b5463/kino-d4/apps/twin/README.md

# KINO Twin acceptance

Build both applications, then serve them from one origin:

```text
npm run build
npm run preview:all
```

Open `http://localhost:4400/dev/twin/` and `http://localhost:4400/studio/` in separate tabs. Keep this checklist blunt: record PASS, FAIL, or BLOCKED with evidence for every line.

Part of this walk is automated: `npm run build && npm run test:acceptance` runs `e2e/twin-acceptance.spec.ts` headless on port 4401, and CI runs the same job on every pull request. It covers the render, inspect, optics, power-on, KDP connect, capture, CAM3 fault, battery sag, measured-override, disconnect and recorder lines. The 3D/WebGL confirmations and the Studio configuration, UART stress, Skew Bench, gallery-scale, Roll and firmware-update lines stay manual.

- [ ] Open KINO Twin and confirm the D4 V1 scene renders without the recovery screen.
- [ ] Inspect components and confirm dimensions and provenance are visible.
- [ ] Change camera pitch and lens-FOV scenario; confirm the camera row and overlap change.
- [ ] Power on Twin; connect Studio with CONNECT KINO TWIN.
- [ ] Confirm HELLO, DEVICE_INFO, CAPABILITIES, and CONFIG_SCHEMA complete through KDP.
- [ ] Configure Wiggle, Quad, and looks in Studio.
- [ ] Perform a four-camera capture.
- [ ] Confirm boot, exposure, UART, SD, and transfer changes appear in Twin's 3D scene.
- [ ] Run the Studio UART stress test and exercise slow-uart and crc-noise faults.
- [ ] Run Skew Bench and compare separate GPIO, VSYNC, and effective-exposure rows.
- [ ] Browse the large simulated gallery without an unbounded load.
- [ ] Exercise Roll connectivity loss, recovery, and upload backlog.
- [ ] Run firmware update UX and confirm target progress and reboot visuals.
- [ ] Set CAM3 offline and confirm Studio diagnoses CAM3 through KDP.
- [ ] Exercise batterySag and fuseBlown; confirm power warnings.
- [ ] Record, save, import, replay, and verify the exact scenario.
- [ ] Enter a real measured override; confirm MEASURED, refreshed geometry, and refreshed collision findings without application-code edits.

## WebSocket bridge (cross-machine Studio)

BroadcastChannel reaches only same-origin tabs. To serve this Twin to a Studio in another browser, container, or machine (issue #29):

```bash
npm run twin:relay                       # dumb message bus on ws://127.0.0.1:5179
# KINO_TWIN_WS_HOST=0.0.0.0 for LAN use — no auth, trusted networks only
```

Open the Twin with `?ws=1` (default relay on this host) or `?ws=ws://host:5179`; open Studio with `?twinWs=ws://host:5179` and its connect screen offers CONNECT KINO TWIN (BRIDGE). Transport only: the wire vocabulary, handshake, busy and close semantics are the same `TwinBusTransport` state machine the BroadcastChannel carrier uses, and `TwinDeviceServer` is unchanged.

## Tier A meshes (converted CAD)

A component renders as a parametric proxy until a real converted mesh is registered for it. The mechanism is in `@kino/three-assets` and needs no application change to use (issue #30):

```ts
import { registerComponentMesh, glbProvider } from '@kino/three-assets';

registerComponentMesh('camera-node', glbProvider(xiaoGlbUrl));
```

The mesh is fitted into the component's resolved dimensions, so the profile stays authoritative: clearance, keepouts, the BOM and the inspector all keep reading the recorded numbers, and a prettier mesh can never quietly move a wall. A missing or broken asset leaves the proxy on screen.

**The conversion itself is a human step and stays out of this repository's build:** download the official STEP (XIAO first), open it in FreeCAD or Blender, export a GLB in millimetres with the part centred on its own origin, and register it as above. Do not commit a mesh whose extents disagree with the profile — the fit will scale it, and the mismatch will only show up as a part that looks wrong next to its neighbours.

## Deliberately deferred

- The converted XIAO GLB itself. The loader, fit and fallback are in place and tested; the asset needs the offline conversion above.
- (shipped in #31) Front-panel DXF, transform CSV, and envelope STEP live in the RECORD tab beside the other engineering exports; the DXF lens-cutout diameter stays PROVISIONAL until a lens barrel is measured.
- Playwright coverage of the WebGL confirmations. The automated walk asserts that the scene mounts and that no render error boundary fires; whether the 3D actually looks right stays a human check.
