b5463/kino-d4/docs/ARCHITECTURE.md

# KINO architecture

KINO has two operating worlds. The camera and Studio form a local instrument. Roll adds a server when photographs need to leave the room. The boundary stays sharp so a network failure cannot disable capture or service work.

## System map

```mermaid
flowchart TB
    subgraph Camera["KINO D4"]
        P4["ESP32-P4 main controller"]
        N1["CAM1 ESP32-S3"]
        N2["CAM2 ESP32-S3"]
        N3["CAM3 ESP32-S3"]
        N4["CAM4 ESP32-S3"]
        SD[("microSD originals")]
        P4 <-->|UART| N1
        P4 <-->|UART| N2
        P4 <-->|UART| N3
        P4 <-->|UART| N4
        P4 --> SD
    end

    Studio["KINO Studio"] <-->|"KDP / Web Serial"| P4
    Device["Device upload client"] --> API["KINO API"]
    P4 --> Device
    API --> PG[("PostgreSQL metadata")]
    API --> Redis[("Redis events")]
    API --> S3[("S3 originals + derivatives")]
    API -->|SSE| Roll["KINO Roll clients"]
    Twin["KINO Twin"] -.->|"virtual transport, same KDP"| Studio
```

## Local device path

Studio connects to the main controller through Web Serial. Boot noise is expected. The decoder scans for the KDP magic bytes, resynchronizes, performs a nonce handshake, then asks the device for identity, capabilities, configuration, camera status, power, storage, and network state.

Feature code never owns a serial port. It talks to `KinoProtocolClient` through a `Transport`:

```text
Studio page
  → device service
  → KinoProtocolClient
  → Transport
  → SerialTransport or simulator transport
  → KDP frame
```

This seam keeps the future Twin honest. A simulated device must obey the same framing, sequence IDs, timeouts, jobs, and capabilities as physical hardware.

## Shared package ownership

| Package | Owns |
|---|---|
| `@kino/kdp` | Frame encoding and decoding, CRC-32, command IDs, wire types, request lifecycle, timing vocabulary, serial and mock transports |
| `@kino/schemas` | Versioned portable documents for devices, configuration, captures, assets, firmware, and errors |
| `@kino/test-fixtures` | Reference device behavior, media fixtures, scenarios, recipes, and device audio |

Wire payloads and portable documents solve different jobs. KDP payloads live inside protocol frames and follow `PROTOCOL_VERSION`. Portable `kino.*` documents carry their own schema name and version. A field name that works on the wire may still be wrong in a stored document. The firmware contract records the known crossings.

## Studio state

Studio keeps three classes of state apart:

- Device truth: the latest value acknowledged or reported by KINO.
- Draft state: local edits that have not been applied.
- Transient state: connection attempts, transfers, calibration jobs, retries, and updates.

The Apply bar exists because draft state cannot masquerade as camera state. After a write, Studio reads back or waits for the device report before showing the value as saved.

## Capture path

The camera captures every original to microSD before network work begins.

```text
four sensor frames
  → central SD originals
  → optional preview
  → resumable upload
  → immutable S3 original keys
  → processing jobs
  → derived wiggle, thumbnail, metadata, export
```

Original keys live under:

```text
rolls/<rollId>/captures/<captureId>/original/cam-<NN>.jpg
```

Workers write under `derived/`. Completion streams the stored object back through SHA-256 before the asset becomes ready. Database uniqueness constraints, rather than preflight reads, enforce capture and asset idempotency under concurrent retries.

## Roll events

The API appends each event to a bounded Redis stream before publishing it live. Guests receive named Server-Sent Events. Reconnects carry `Last-Event-ID` and replay the missed stream range.

One subscriber connection serves all Roll guests in an API process. If that connection drops, the API closes the open SSE responses. Browsers reconnect and replay the gap instead of sitting on a healthy-looking socket that missed photographs.

## Repository map

```text
apps/
  api/                 Fastify API, migrations, auth, uploads, SSE
  studio/              React device workbench
  worker/              BullMQ media workers: derivatives, recaps, exports, purge
  roll-web/            public Roll guest PWA and host dashboard
  twin/                KINO Twin 3D assembly, simulation, and measurement
packages/
  kdp/                 protocol implementation
  schemas/             portable document schemas
  test-fixtures/       reference device and fixtures
  design-system/       shared tokens and accessible primitives
  media/               wiggle frame sequencing shared by web and worker
  hardware-profiles/   versioned D4 geometry, nets, GPIO map
  simulator-engine/    boot, capture choreography, power/thermal models, replay
  three-assets/        parametric 3D component builders
firmware/              ESP-IDF firmware: P4 main controller, XIAO camera node, portable KDP C core
firmware-contract/     firmware-facing contract
infra/                 dev/staging/production compose, backup and drill scripts
kino_dev_spec_pack/    product specifications
kino_twin_spec/        digital-twin specification and source data
docs/                  maintained guides, audits, historical plans
archive/               retained recovery material
```

## Current implementation line

The main branch contains Studio, the full Roll backend and workers, the public Roll client, KINO Twin, shared contracts, production/staging infrastructure with tested backup and restore, and broad tests. All of it runs against the simulated device. The D4-V1 firmware now also lives here (`firmware/`): the P4 and camera-node applications build clean in CI and implement the Milestone 1B single-camera surface, but nothing has run on physical hardware — `firmware/HARDWARE_VALIDATION.md` records what the bench has actually proven (currently nothing), and measured hardware dimensions remain outstanding. Hardware-gated acceptance items are marked as such where they appear.

For exact protocol authority, start at [the firmware contract](../firmware-contract/README.md). For the hardware boundary, read [the hardware reference](HARDWARE.md).
