b5463/kino-d4/docs/DEVICE_COPY.md

# Device copy

Every line the KINO D4 body says on its own screen, and when. Source of truth is `firmware/p4/main/ui.c`, `conditions.h` and `capture.c`. `npm run copy:check` walks those three files and fails when a line they can draw is not in this table, so the sentence above is a check rather than a promise.

## The rule

The person holding the camera has read nothing and will not phone anyone. Each line names what happened and, when there is one, what to do about it. Under 40 characters for a toast, one short line for a banner, two for a dialog. Plain words: lens, photo, card, cells. No codes, no camera numbers, no contract names on the glass; those go to the log and the KDP reply.

## Header chip

| Text | When |
|---|---|
| `PROBLEM` / `CHECK` / `NOTE` | The worst open condition. Absent when there is none. |
| `4571 SHOTS` | Card mounted, photographs left at 6 MB each. |
| `LAST 5` .. `LAST 1` | Five or fewer left. |
| `CARD FULL` | None left. |
| `NO CARD` | No card mounted since boot. |
| `CARD OUT` | The card was pulled while running. |
| `USB` / `BATTERY` | Where the power comes from. |

## STATUS rows

Severity words: PROBLEM stops photographs, CHECK does not yet, NOTE is information.

| Title | Detail | Severity |
|---|---|---|
| No card | Put a card in. Photos cannot be saved. | PROBLEM |
| The card was taken out | Put it back. Photos cannot be saved. | PROBLEM |
| The card cannot be read | Not a format KINO reads. Use a card up to 32 GB, or format it. | PROBLEM |
| This card failed a write | Copy your photos off it and change the card. | PROBLEM |
| This card is slow | Photos take longer to save. A faster card helps. | CHECK |
| The card is full | Delete photos or change the card. | PROBLEM |
| Card nearly full | Room for about N more photos. | CHECK |
| A lens is not answering | The second from the left. Try RESTART THE CAMERAS below. | PROBLEM, with the four cells |
| Lenses are not answering | 2 of 4. Try RESTART THE CAMERAS below. | PROBLEM, with the four cells |
| The cameras need an update | Connect to Studio to update them. | CHECK |
| The date is not set | Wi-Fi or Studio sets it once. | CHECK |
| Cameras not measured | The first photograph measures them. | NOTE |
| The camera lost power while running | Charge or replace the cells. | CHECK |
| Running without Wi-Fi | It crashed 3 times in a row. Restart to try again. | PROBLEM |
| The camera is warm | 78 C inside. The finder slows until it cools. | CHECK |
| The clock is on UTC | Set the time zone in CONNECTION. | NOTE |
| Uploads have no server | Set the Roll server in Studio. Photos stay on the card. | CHECK |

Action rows at the foot of STATUS: **Restart the cameras** (always) and **Measure cameras again** (once measured).

## SHOOT banner

| Text | When |
|---|---|
| `SHOOTING` / `READING` / `SAVING` | The capture's stages. |
| `SAVING - NEXT SHOT QUEUED` | A second shutter press landed while saving; it fires when the report does. |
| `TAKE THE LENS COVER OFF` | On SHOOT, every pane was lit and then all went dark for a second: the cover went on. A body switched on facing the desk says nothing. |
| `CHECK THE SECOND LENS` | On SHOOT, one pane was lit and then went a third as bright as the rest for a second while the others stayed lit. |
| `10` .. `1`, `SELF-TIMER.  PRESS TO CANCEL` | A long shutter press started the timer. |
| `SAVED` | Every lens that answered is on the card. |
| `SAVED, 1 CAMERA MISSED` | A partial photograph; the cells show which. |
| `No card. Put one in.` | Shutter with no card. |
| `Card full. Delete photos or change the card.` | Shutter with no room. |
| `No lens answered. Try a restart.` | No camera node answered the probe. |
| `The lenses did not wake. Try a restart.` | The camera bank did not come back after a cycle. |
| `Card error. Photo not saved.` | The capture folder could not be made, or META.JSON would not commit and the half-made folder was removed. Both end with nothing on the card, so both say so; the log and the KDP reply separate the causes. |

## Working banners

| Text | When |
|---|---|
| `FORMATTING THE CARD` | FORMAT confirmed; the card is locked for the seconds it takes. |
| `RESTARTING THE CAMERAS` | RESTART THE CAMERAS pressed; three seconds. |

## Toasts

| Text | When |
|---|---|
| Card ready, 4571 SHOTS | A card was put in while running and mounted. |
| Card taken out. Photos cannot be saved | The card was pulled while running. |
| Card busy. Try again | The card lock was held for two seconds by a capture or an upload. |
| Card formatted | FORMAT finished. |
| The card could not be formatted | FORMAT failed; the log has the reason. |
| Deleted.  TAP TO UNDO | One photograph moved to the trash; the toast stays thirty seconds and a tap restores it. |
| Restored | UNDO tapped in time. |
| Could not restore it | The folder would not move back. |
| Timer cancelled | A press during the self-timer. |
| Deleting photos | DELETE ALL started on the gallery task. |
| No photos on the card | DELETE ALL with nothing to delete. |
| No card in the slot | FORMAT with nothing in the slot. |
| Cameras measured | The first photograph's measurement stored. |
| Not measured: aim at something with detail | The measurement found a flat scene. |
| The next photo measures the cameras | MEASURE AGAIN pressed. |
| Sent to the roll | SEND TO ROLL queued the photograph. |
| Could not send. Try again later | SEND TO ROLL could not queue it. |
| No active roll | SEND TO ROLL with no Roll joined. |
| No pictures on the card to send | SEND TO ROLL on a photograph with no frames left. |
| Could not save the change | The favourite flag could not be written. |
| Still reading the card | A tile tapped before the gallery had its id. |
| No looks on this camera | LOOK with no recipes. |
| Hold the power slide to switch off | SHUT DOWN row, which has no soft power-off. |
| The cameras did not start. Restart the camera | The shutter, on a body whose capture pipeline failed to come up at boot. Said instead of blaming a capture that is not running. |
| Favourite / Not favourite | FAVOURITE pressed on PHOTO; the mark went on or came off. |
| First photo / Last photo | PREV on the first photograph, or NEXT on the last. |

## Dialogs

| Title | Body | Buttons | When |
|---|---|---|---|
| FIRST START | Take a photograph first. It measures the cameras. See STATUS. | GOT IT | The first boot, once. |
| UPDATED | KINO has been updated. Now on 0.4.58. Nothing to do. | OK | The first boot on a new version, once. |
| RESTART | Back in a moment? KINO restarts and comes back to SHOOT. | RESTART / CANCEL | POWER > RESTART |
| FACTORY RESET | Reset the camera? Settings, networks and roll are erased. | RESET / CANCEL | POWER > FACTORY RESET |
| DELETE | Delete this photo? N frames. This cannot be undone. | DELETE / CANCEL | PHOTO > DELETE |
| DELETE ALL | Delete all photos? N photos. This cannot be undone. | DELETE / CANCEL | STORAGE > DELETE ALL PHOTOS |
| FORMAT CARD | Erase the card? Every photo on it is deleted. | FORMAT / CANCEL | STORAGE > FORMAT CARD |

## Screen rows and labels

What each screen puts on itself, beyond the chip, the banner and the toasts
above. Every one of these is drawn by `ui.c`; the check script walks the same
calls and fails when one of them is not in this table.

### SHOOT

| Text | When |
|---|---|
| `MENU` | The way out, on the back button beside the picture. |
| `WIGGLE` / `QUAD` | The mode, on the decisions bar. Tapping the bar opens LOOK. |
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
