b5463/kino-d4/firmware/FIRMWARE_ROADMAP.md

# KINO D4 firmware roadmap — current state to validated prototype

Dependency-ordered plan from firmware 0.3.0 to a physically validated KINO D4, then toward
product-ready firmware. Derived from the Phase 1 baseline audit of HEAD `7a6066a`.

**Status:** planning document. Nothing here is implemented.
**Companion documents:** [`HARDWARE_VALIDATION.md`](HARDWARE_VALIDATION.md) (bench evidence),
[`FIRMWARE_START_PLAN.md`](FIRMWARE_START_PLAN.md) (original tree plan),
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
