b5463/kino-d4/docs/assets/brand/kino-d4-silver-on-dark.png

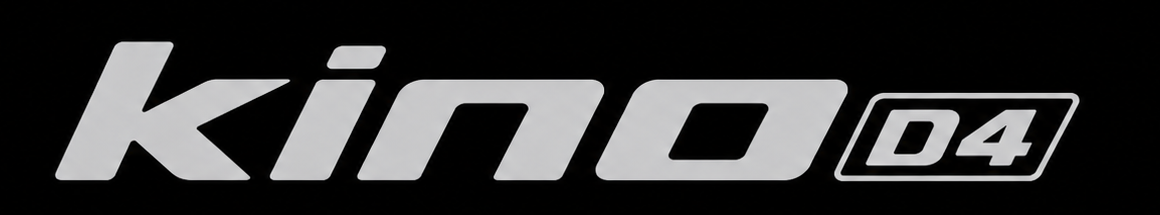
docs/assets/brand/kino-d4-silver-on-dark.png
