b5463/kino-d4/docs/assets/brand/kino-d4-wordmark-sheet.png

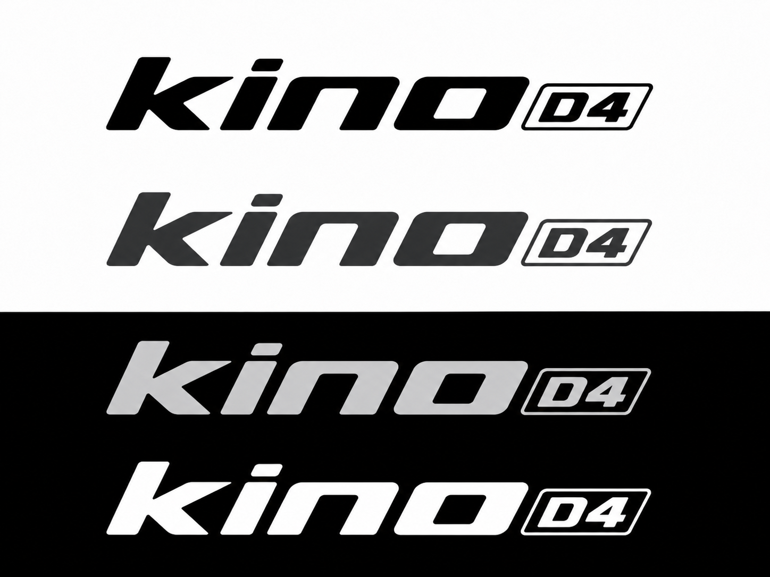
docs/assets/brand/kino-d4-wordmark-sheet.png
