b5463/kino-d4/docs/assets/brand/kino-roll.png

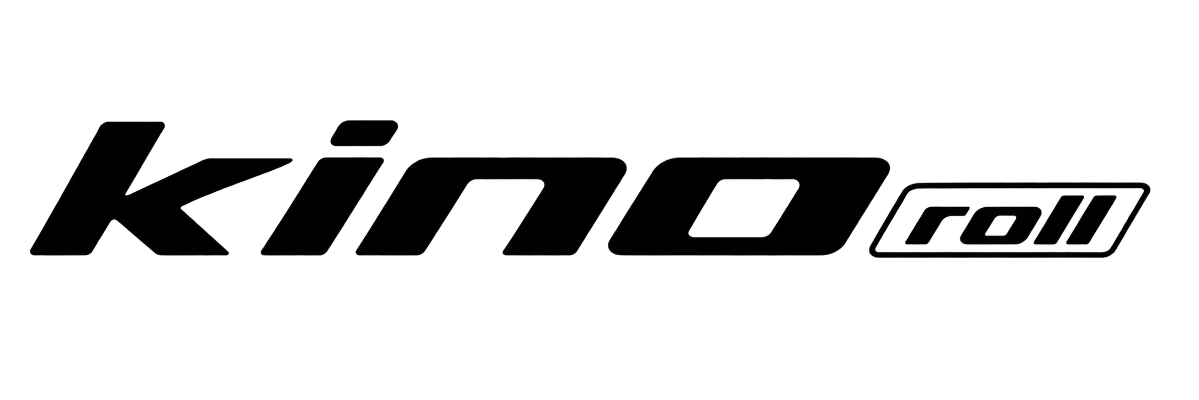
docs/assets/brand/kino-roll.png
