b5463/kino-d4/docs/assets/brand/kino-studio-wordmark.png

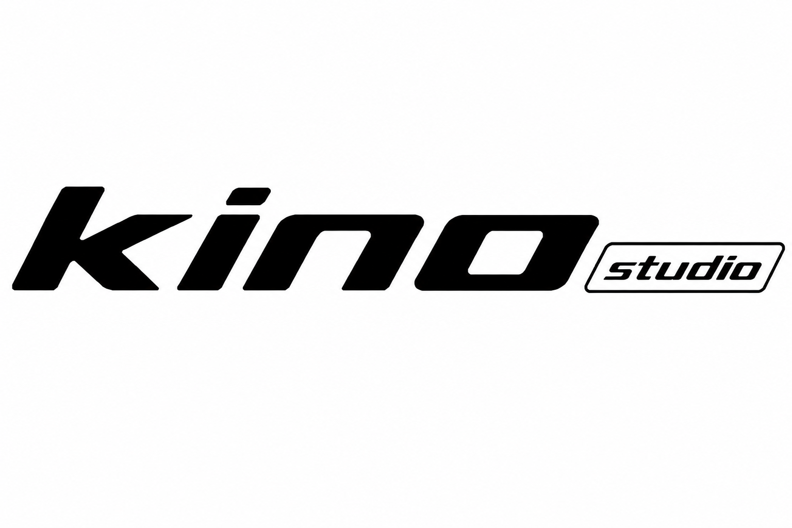
docs/assets/brand/kino-studio-wordmark.png
