b5463/kino-d4/firmware/p4/host_preview/specimen/GUEST.png

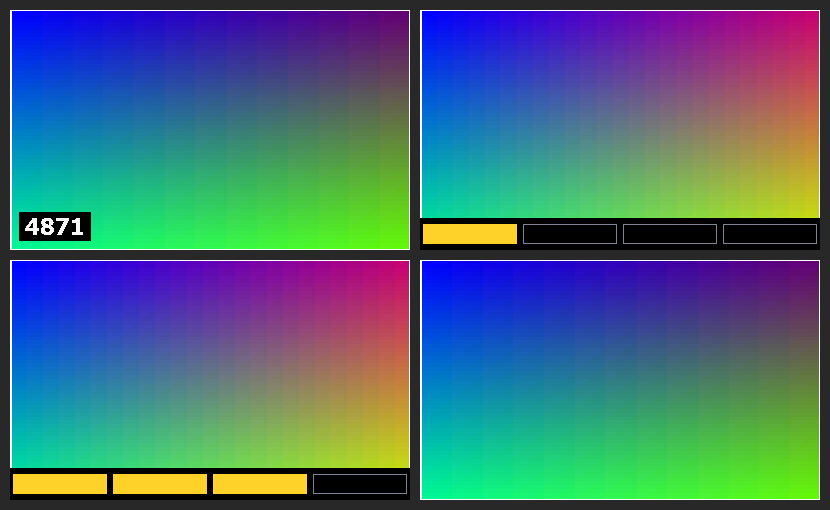
firmware/p4/host_preview/specimen/GUEST.png
