b5463/kino-d4/firmware/p4/host_preview/specimen/MENU_STACK.png

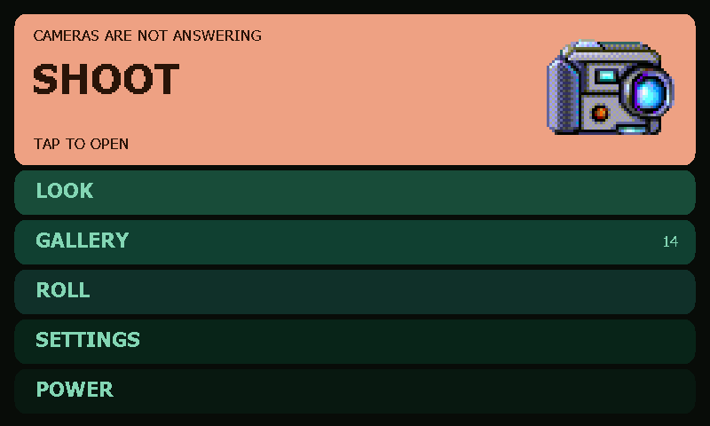
firmware/p4/host_preview/specimen/MENU_STACK.png
