b5463/kino-d4/hardware/cad/KINO_FIELD_BODY/previews/KINO_DOOR_JOINT_COUPON_PREVIEW.png

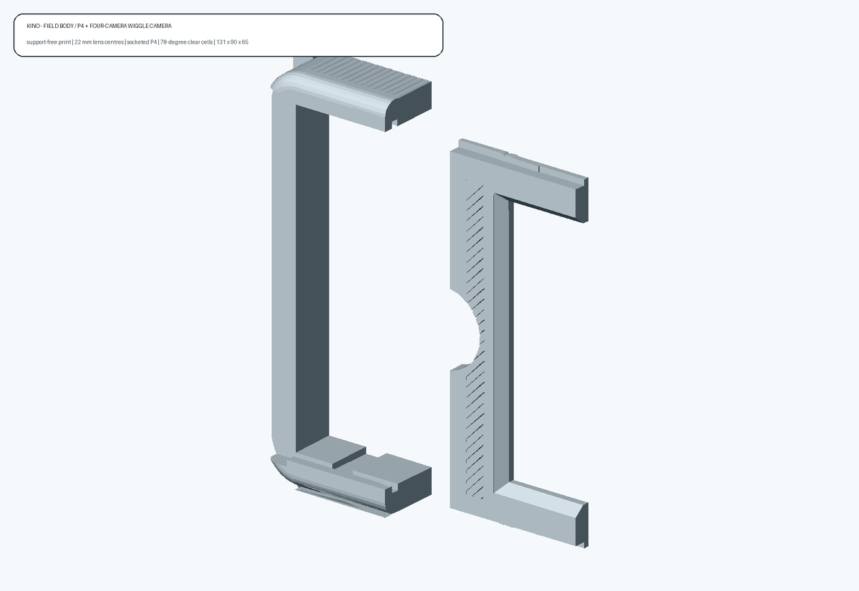
hardware/cad/KINO_FIELD_BODY/previews/KINO_DOOR_JOINT_COUPON_PREVIEW.png
