b5463/kino-d4/hardware/cad/KINO_FIELD_BODY/previews/KINO_FACE_ALIGN_TOOL_PREVIEW.png

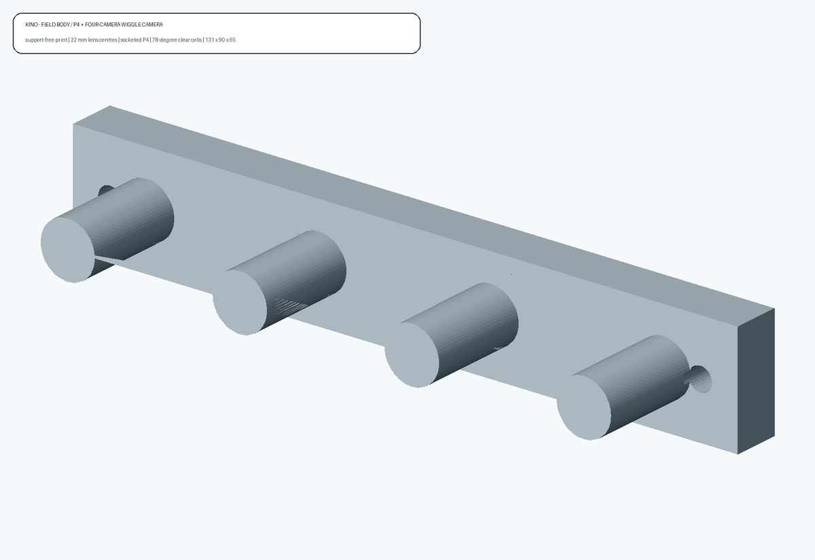
hardware/cad/KINO_FIELD_BODY/previews/KINO_FACE_ALIGN_TOOL_PREVIEW.png
