b5463/kino-d4/hardware/cad/KINO_FIELD_BODY/previews/KINO_FIELD_BEZEL_PREVIEW.png

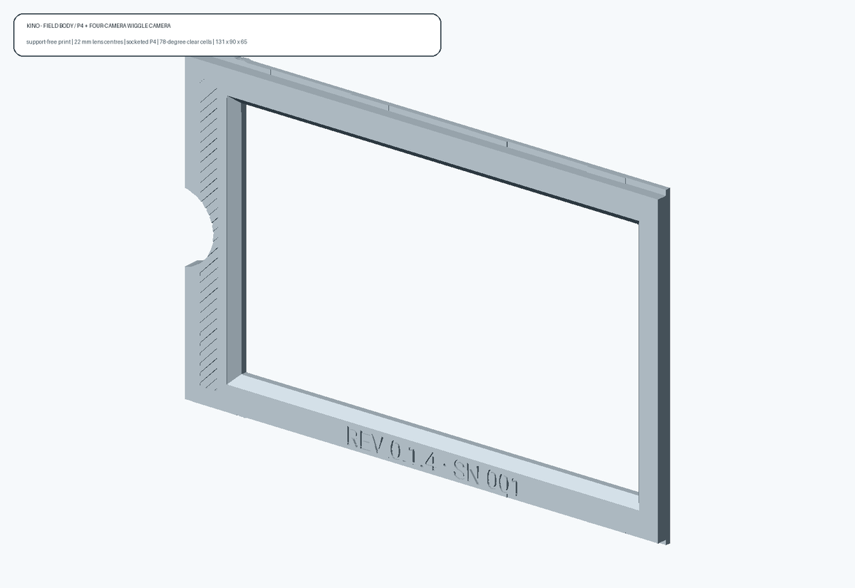
hardware/cad/KINO_FIELD_BODY/previews/KINO_FIELD_BEZEL_PREVIEW.png
