b5463/kino-d4/hardware/cad/KINO_FIELD_BODY/previews/KINO_FIELD_LENS_SLIDER_FRONT.png

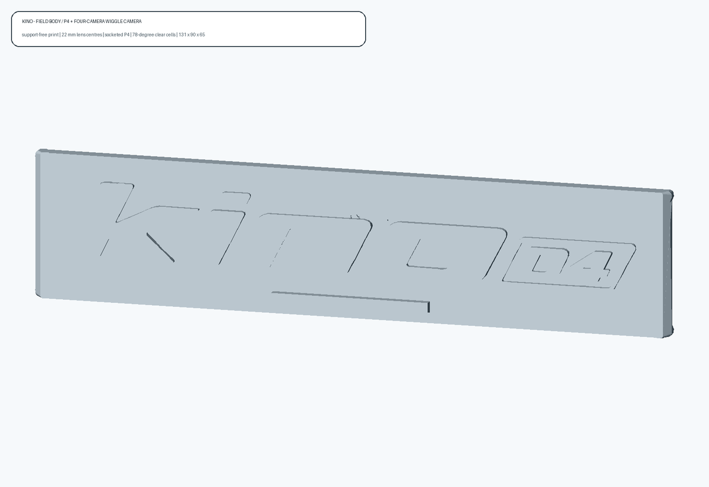
hardware/cad/KINO_FIELD_BODY/previews/KINO_FIELD_LENS_SLIDER_FRONT.png
