b5463/kino-d4/hardware/cad/KINO_FIELD_BODY/previews/KINO_FIELD_LENS_SLIDER_PREVIEW.png

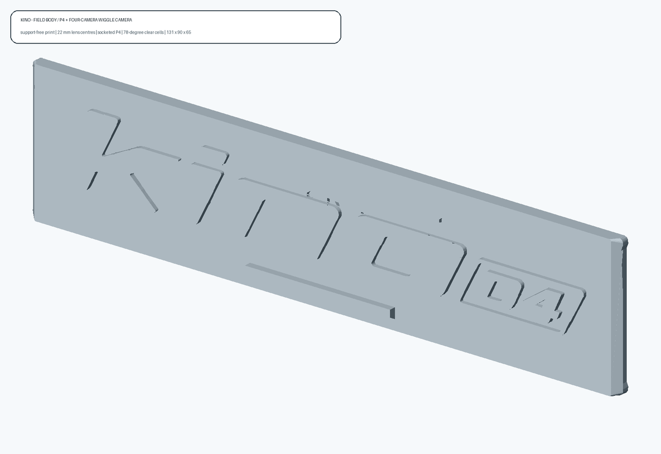
hardware/cad/KINO_FIELD_BODY/previews/KINO_FIELD_LENS_SLIDER_PREVIEW.png
