b5463/kino-d4/hardware/cad/KINO_FIELD_BODY/previews/KINO_PLATE_2_FACE_DOOR_COVER_PREVIEW.png

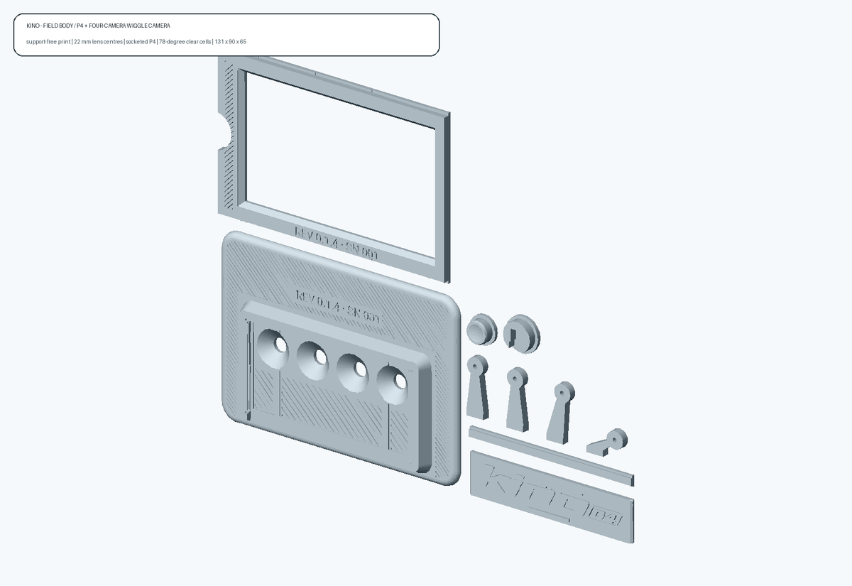
hardware/cad/KINO_FIELD_BODY/previews/KINO_PLATE_2_FACE_DOOR_COVER_PREVIEW.png
