b5463/kino-d4/hardware/cad/KINO_FIELD_BODY/previews/KINO_SPLIT_JOINT_COUPON_PREVIEW.png

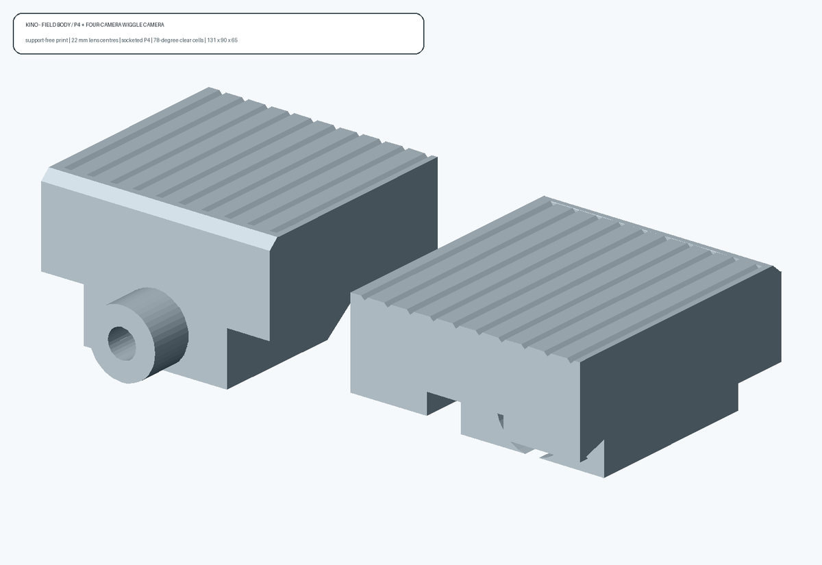
hardware/cad/KINO_FIELD_BODY/previews/KINO_SPLIT_JOINT_COUPON_PREVIEW.png
