b5463/kino-d4/hardware/pcb/kino-d4-carrier-a0/outputs/P4-MOUNTING-TEMPLATE.png

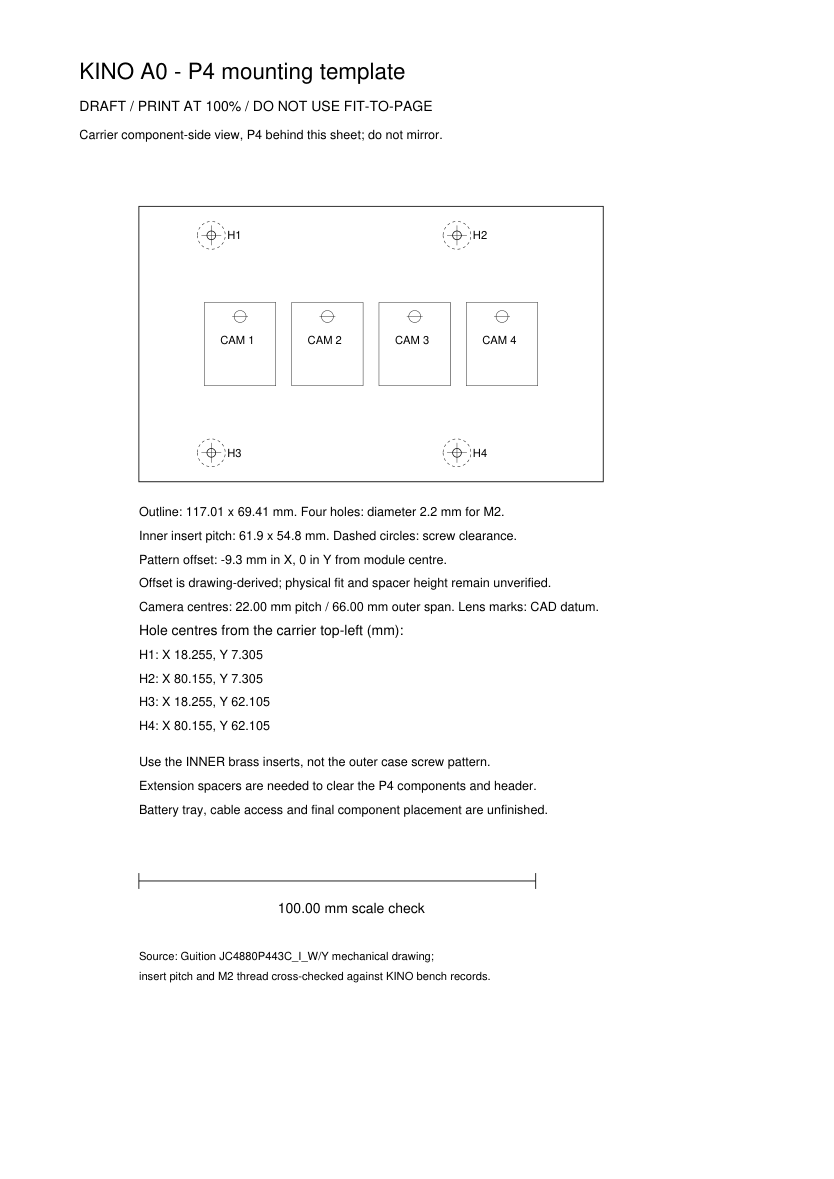
hardware/pcb/kino-d4-carrier-a0/outputs/P4-MOUNTING-TEMPLATE.png
