b5463/kino-d4/hardware/pcb/kino-d4-carrier-a0/outputs/page-3.png

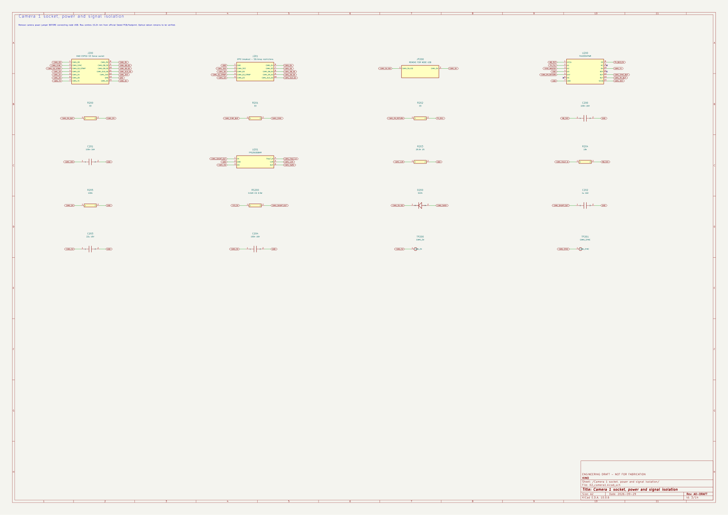
hardware/pcb/kino-d4-carrier-a0/outputs/page-3.png
