b5463/kino-d4/hardware/pcb/kino-d4-carrier-a0/outputs/PLACEMENT-DRAFT.png

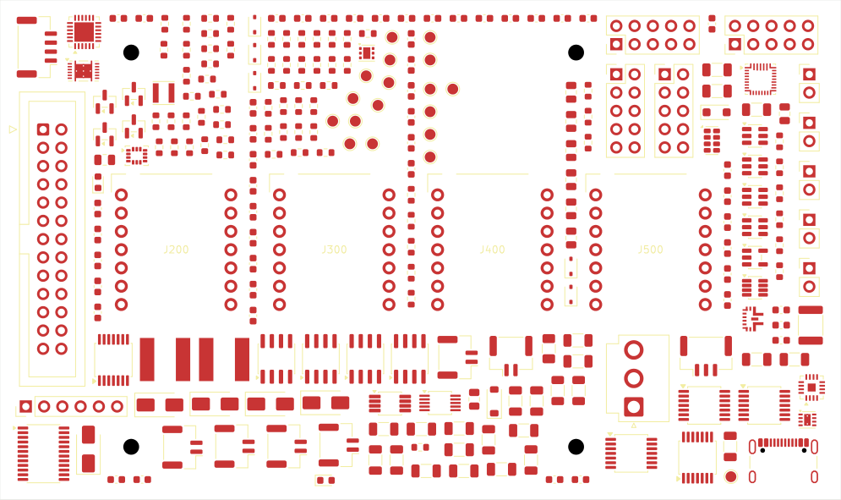
hardware/pcb/kino-d4-carrier-a0/outputs/PLACEMENT-DRAFT.png
