b5463/kino-d4/hardware/pcb/kino-d4-carrier-a0/outputs/REVIEW-TOP.png

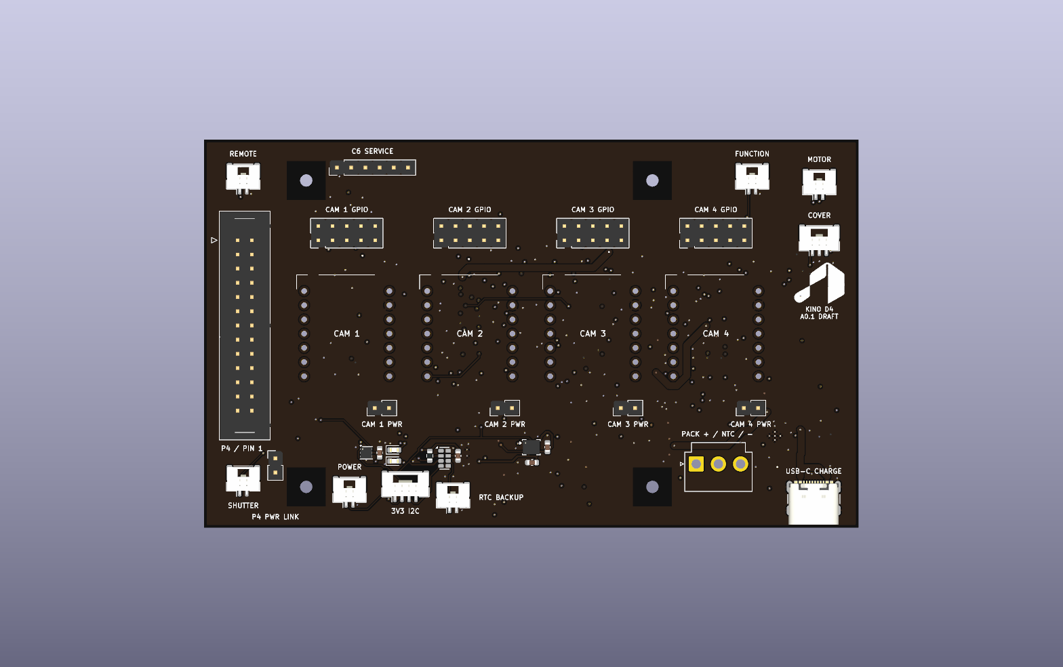
hardware/pcb/kino-d4-carrier-a0/outputs/REVIEW-TOP.png
