b5463/kino-d4/hardware/pcb/kino-d4-mainboard-rev1/outputs/KINO_D4_Mainboard_Rev1-envelope.png

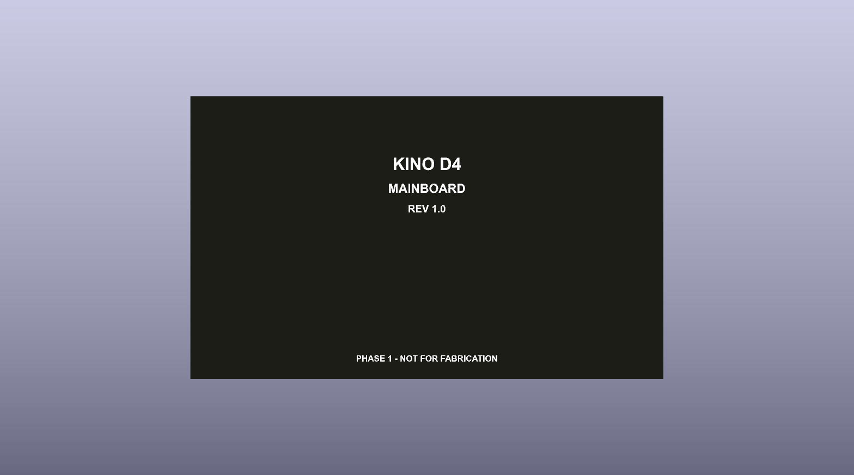
hardware/pcb/kino-d4-mainboard-rev1/outputs/KINO_D4_Mainboard_Rev1-envelope.png
