b5463/kino-d4/hardware/cad/KINO_FIELD_BODY/coupons/KINO_WIGGLE_TEST_RIG.stl

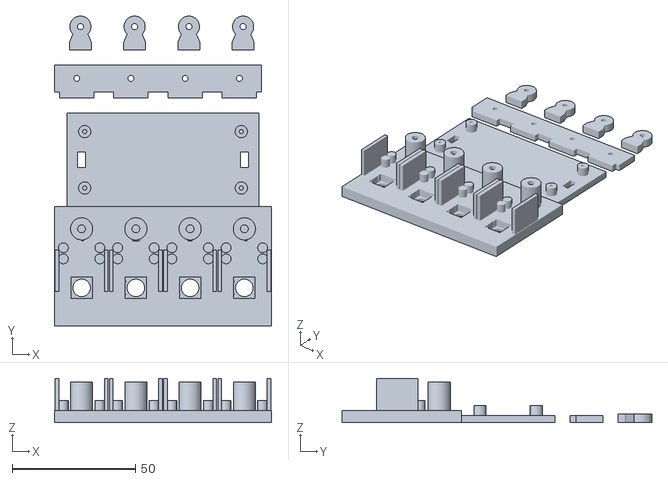
[picture p69: CAD file, 2026-09-08]
hardware/cad/KINO_FIELD_BODY/coupons/KINO_WIGGLE_TEST_RIG.stl
88.0 x 125.7 x 18.0
