b5463/kino-d4/hardware/cad/KINO_FIELD_BODY/print/KINO_FIELD_SHUTTER_BUTTON.stl

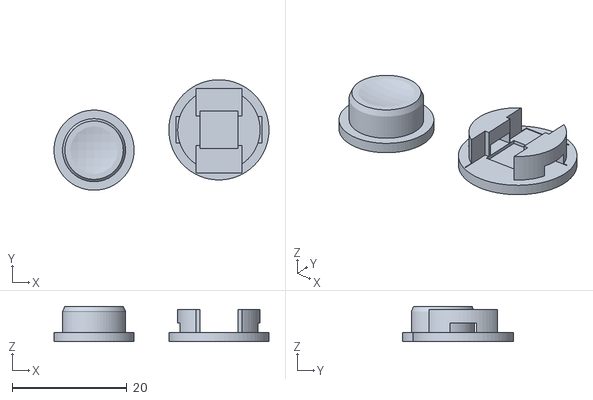
[picture p70: CAD file, 2026-09-08]
hardware/cad/KINO_FIELD_BODY/print/KINO_FIELD_SHUTTER_BUTTON.stl
37.5 x 19.3 x 6.20
