b5463/kino-d4/hardware/cad/KINO_FIELD_BODY/twin/KINO_TWIN_DOOR.stl

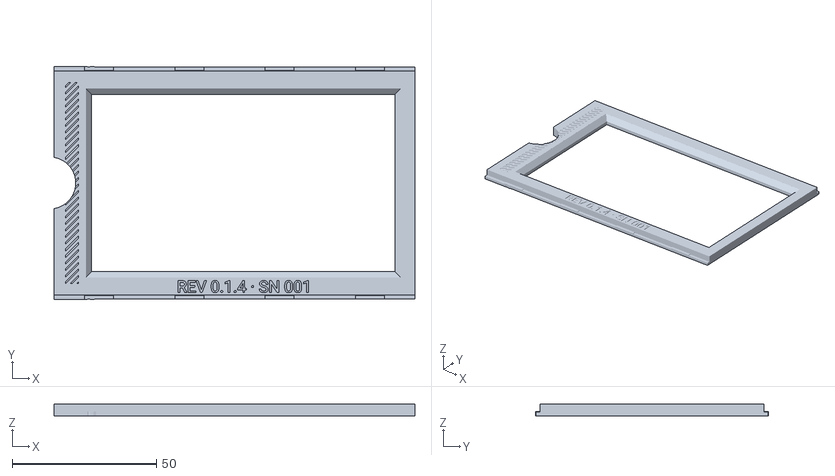
[picture p71: CAD file, 2026-09-19]
hardware/cad/KINO_FIELD_BODY/twin/KINO_TWIN_DOOR.stl
125.0 x 80.7 x 4.00
