b5463/kino-d4/hardware/cad/KINO_FIELD_BODY/coupons/KINO_SHUTTER_COUPON.stl

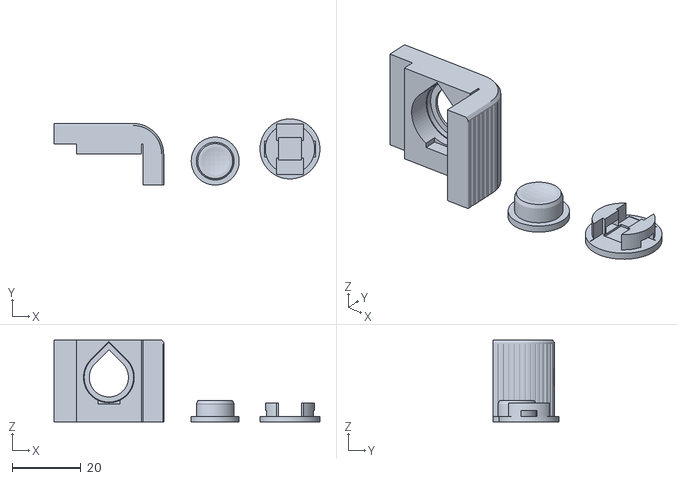
[picture p72: CAD file, 2026-09-08]
hardware/cad/KINO_FIELD_BODY/coupons/KINO_SHUTTER_COUPON.stl
77.6 x 19.3 x 23.9
