b5463/kino-d4/hardware/cad/KINO_FIELD_BODY/coupons/KINO_XIAO_STACK_COUPON.stl

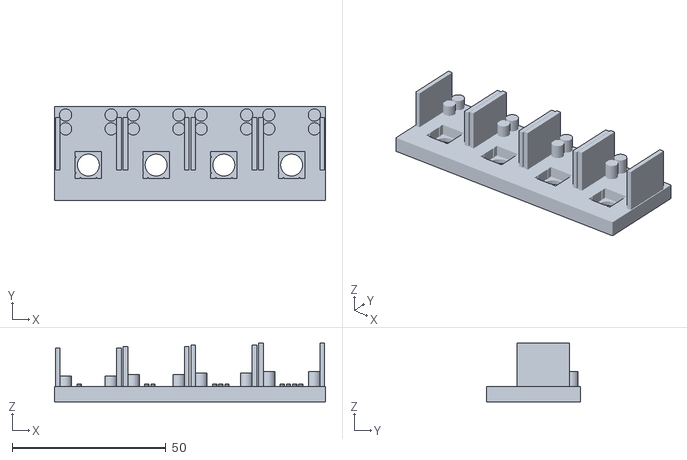
[picture p73: CAD file, 2026-09-08]
hardware/cad/KINO_FIELD_BODY/coupons/KINO_XIAO_STACK_COUPON.stl
88.0 x 30.4 x 19.0
