b5463/kino-d4/hardware/cad/KINO_FIELD_BODY/coupons/KINO_SLIDER_TRACK_COUPON.stl

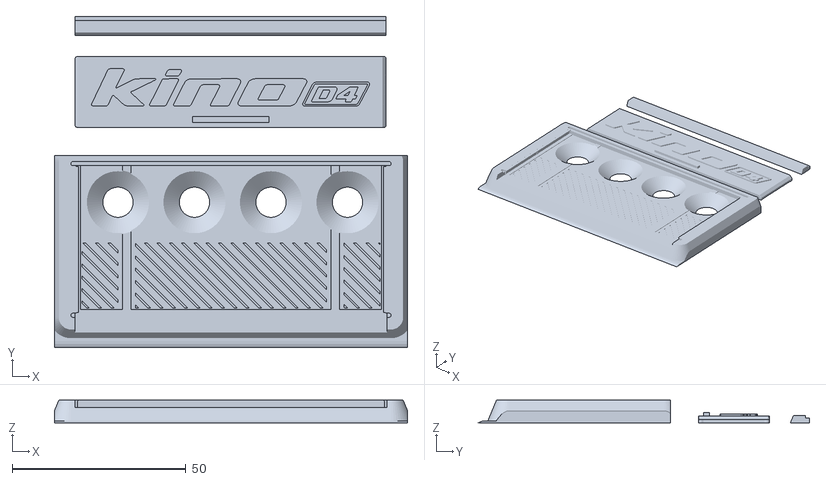
[picture p74: CAD file, 2026-09-08]
hardware/cad/KINO_FIELD_BODY/coupons/KINO_SLIDER_TRACK_COUPON.stl
101.6 x 95.2 x 6.60
