b5463/kino-d4/hardware/cad/KINO_FIELD_BODY/coupons/KINO_WIGGLE_RIG_SKELETAL.stl

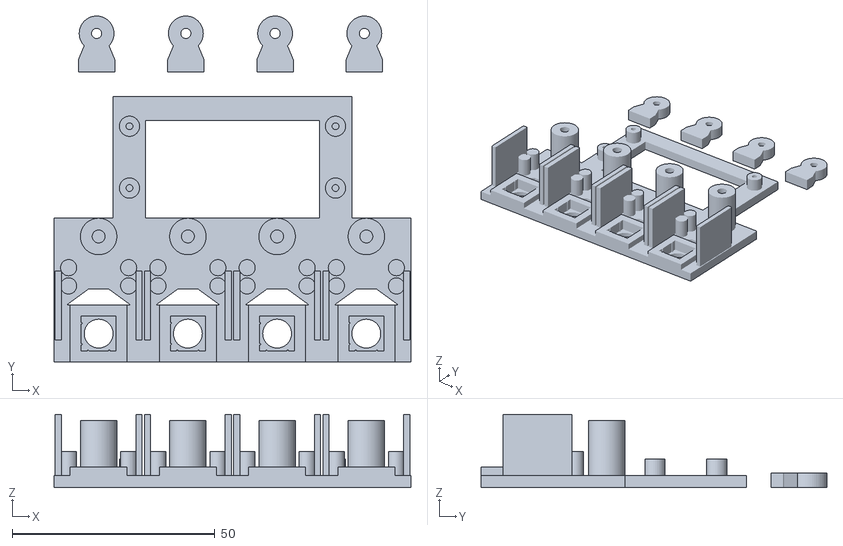
[picture p75: CAD file, 2026-09-08]
hardware/cad/KINO_FIELD_BODY/coupons/KINO_WIGGLE_RIG_SKELETAL.stl
88.0 x 85.3 x 18.0
