b5463/kino-d4/hardware/cad/KINO_FIELD_BODY/coupons/KINO_CAM_FIT_COUPON.stl

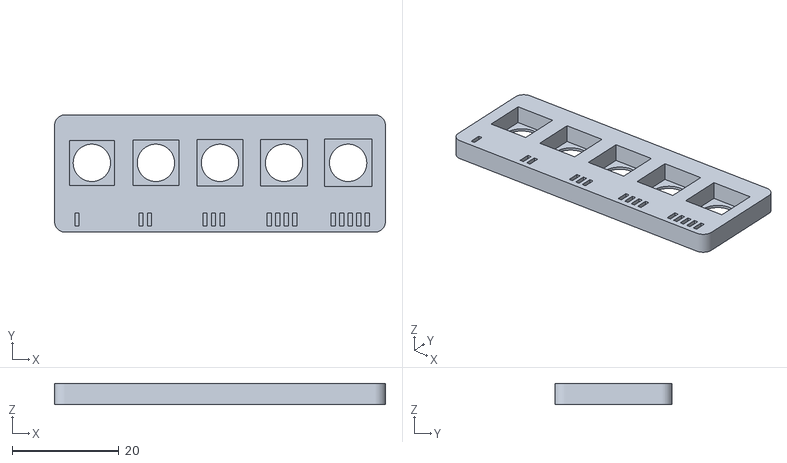
[picture p76: CAD file, 2026-09-08]
hardware/cad/KINO_FIELD_BODY/coupons/KINO_CAM_FIT_COUPON.stl
62.0 x 22.0 x 4.00
