b5463/kino-d4/hardware/cad/KINO_FIELD_BODY/coupons/KINO_FACE_ALIGN_TOOL.stl

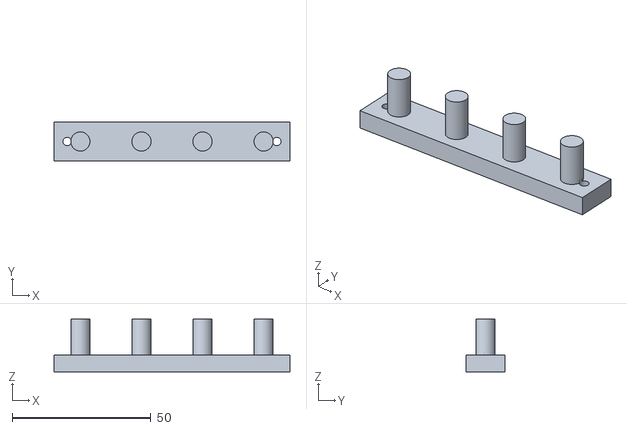
[picture p77: CAD file, 2026-09-08]
hardware/cad/KINO_FIELD_BODY/coupons/KINO_FACE_ALIGN_TOOL.stl
85.0 x 14.0 x 19.0
