b5463/kino-d4/hardware/pcb/kino-d4-carrier-a0/outputs/A02-ASSEMBLY-BACK.png

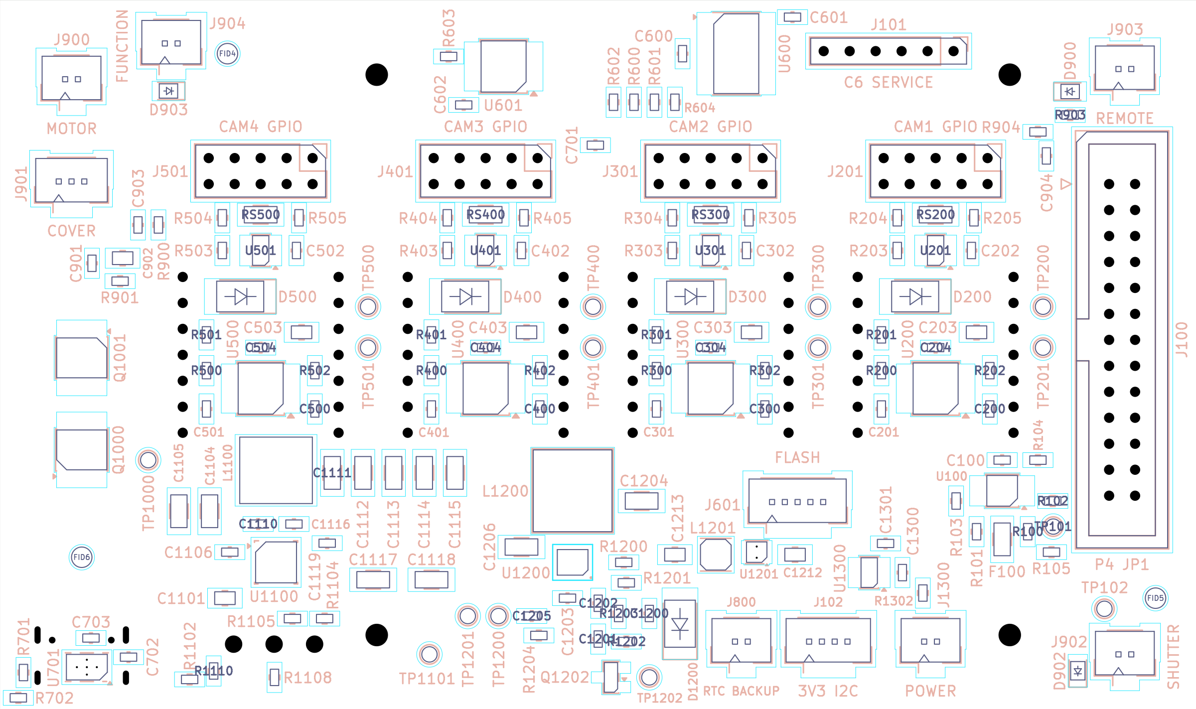
hardware/pcb/kino-d4-carrier-a0/outputs/A02-ASSEMBLY-BACK.png
