b5463/kino-d4/hardware/cad/KINO_FIELD_BODY/previews/KINO_P4_POST_SCREW_TEST_PREVIEW.png

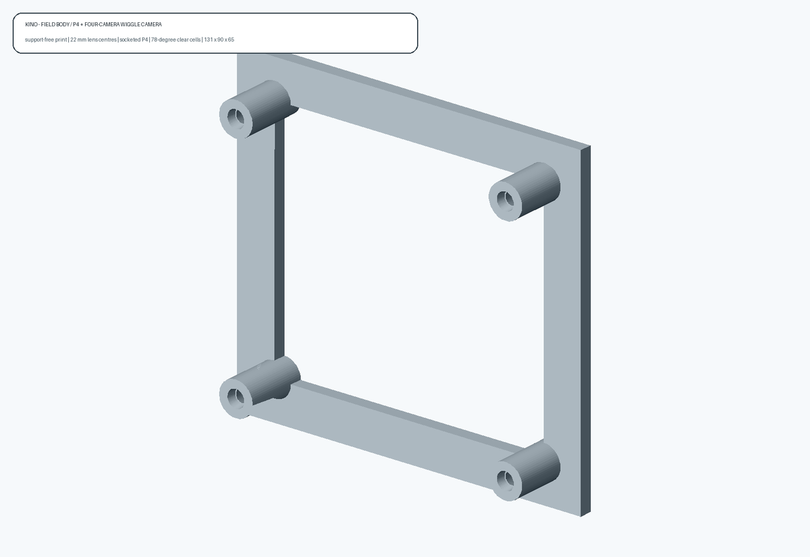
hardware/cad/KINO_FIELD_BODY/previews/KINO_P4_POST_SCREW_TEST_PREVIEW.png
