b5463/kino-d4/hardware/cad/KINO_FIELD_BODY/previews/KINO_WIGGLE_TEST_RIG_PREVIEW.png

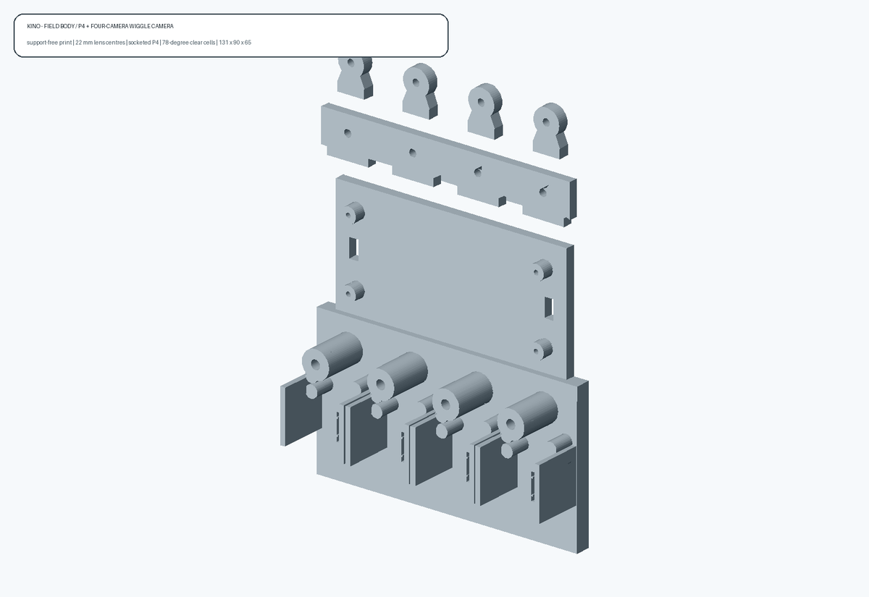
hardware/cad/KINO_FIELD_BODY/previews/KINO_WIGGLE_TEST_RIG_PREVIEW.png
