b5463/kino-d4/packages/test-fixtures/media/frame-01.jpg

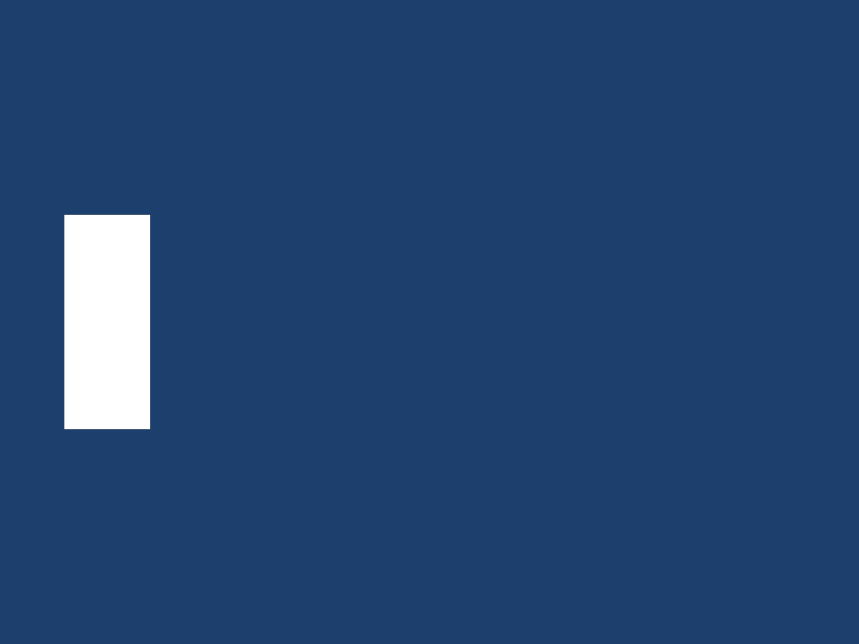
packages/test-fixtures/media/frame-01.jpg
