b5463/kino-d4/hardware/revisions/D4-V1.md

# D4-V1

| Field | Value |
|---|---|
| Product | KINO D4 |
| Physical revision | D4-V1 |
| Current design package | 0.1.3 |
| Lifecycle | Prototype |
| KDP compatibility | Protocol 1 |
| First recorded | 2026-08-17 |
| Physical acceptance | Not passed |

## Fixed architecture

- One Guition JC4880P443C-I-W ESP32-P4 and ESP32-C6 main module.
- Four Seeed XIAO ESP32-S3 Sense camera nodes with OV3660 sensors.
- Four independent switched 5 V camera channels.
- Four full-duplex UART links and one shared sync branch per camera.
- Central microSD storage.
- One 1S LiPo power system with an F3A fuse, protection board, and SW6106 boost stage.
- No built-in flash. The constant-current direct-flash assembly was dropped in design package 0.1.3 (ECN-0003); an external flash module will be used and has no P4 pin in this revision.

## Open items

- Final P4 GPIO assignments. The JP1 header map was measured on the board (ECN-0002) and its twelve GPIOs carry eleven signals: the four camera UART pairs, SYNC_OUT on GPIO32, CAM_PWR_EN on GPIO31, and BTN_SHUTTER on GPIO28 since ECN-0003. Every row is electrically UNVALIDATED until a node answers or the button is pressed on a board. GPIO35 on pin 15 is the spare and stays unconnected. BTN_FN, SLIDE_MODE and the four per-camera power-switch lines have no header pin.
- Measured main-board, battery, BMS, carrier, speaker, and connector envelopes.
- Locked enclosure CAD.
- Locked carrier layout or PCB.
- Closed-enclosure thermal record.
- Effective exposure-skew record from physical hardware.
- Full acceptance and party-duration soak.

## Compatibility rule

A V1-compatible change preserves the camera-node harness, supply topology, controller family, lens order, service openings, and firmware-visible hardware identity. Breaking any of those requires a revision review and may require D4 V2.
