b5463/kino-d4/firmware/components/node_link/include/node_link/node_link.h

// P4 <-> XIAO camera-node link. Reuses the KDP frame layout, CRC and decoder
// from kdp_core on a separate physical UART, so boot-spew tolerance and
// resync behavior are identical on both links. Command ids below are this
// link's own namespace — they never appear on the Studio link.
#ifndef NODE_LINK_H
#define NODE_LINK_H

#define NL_PROTOCOL_VERSION 1

// Default camera-link baud. Escalation to 1.5/2/3 Mbaud is bench work driven
// through KDP SET_LINK_BAUD/LINK_BENCH (milestone 3), not a compile default.
/*
 * 921600. Halving it to 460800 was tried and is not kept.
 *
 * The RX FIFO is 128 bytes, which is 1.39 ms of tolerance at this rate, and
 * overruns do happen: the driver resets the FIFO on one, so the frame in
 * flight is lost and the read times out. 460800 doubles the tolerance and did
 * cut overruns from 4-10 per capture to 1-4, but it did not eliminate them and
 * it doubles every transfer on all four cameras. Since a lost chunk is
 * recovered by a retry either way, the faster line with retries beats the
 * slower line without them.
 */
/*
 * The largest preview frame the link will carry, and both ends mean it.
 *
 * This was two numbers that disagreed (#208): the node treated anything above
 * 32 KB as a photograph-sized leftover and took the next frame, while the body
 * refused anything above 24 KB by size. A 320x240 frame of a detailed scene at
 * the highest preview quality lands between the two, so the node kept it and
 * the body dropped it - the pane blinked on a camera that was working.
 *
 * One number, at the larger value, so there is no band where a frame is
 * acceptable at one end and not the other. The body's buffer is in PSRAM, so
 * the difference costs 8 KB a channel on a body with megabytes to spare.
 */
#define NL_PREVIEW_MAX_BYTES (32 * 1024)

#define NL_DEFAULT_BAUD 921600

/*
 * The rates a node will accept.
 *
 * 921600 is the floor and the fallback. The rest are what the bench is for:
 * the measured cost of a shutter is the largest JPEG divided by the line rate
 * (#218), so this is the only lever on it that does not cost picture quality.
 *
 * Both ends derive the UART clock from a source that divides exactly to all
 * four, so none of them is an approximation with a built-in error budget.
 */
#define NL_BAUD_SUPPORTED_N 4
#define NL_BAUD_SUPPORTED_LIST \
  { 921600, 1500000, 2000000, 3000000 }

/*
 * The rate the body drives the link to, once it has found its nodes.
 *
 * Not NL_DEFAULT_BAUD, which is a different thing and does not move: a node
 * powers on at that rate and both ends fall back to it when a switch fails,
 * so it has to work with no negotiation behind it.
 *
 * 3 Mbaud, measured on KD4-D121BC across 24 captures and six switches in both
 * directions with no CRC failure, resync or timeout: a four-camera capture
 * takes 1755 ms against 3716 ms at 921600, because the cost of a shutter is
 * the largest JPEG divided by the line rate (#218).
 *
 * What it spends is interrupt headroom. The body's receive FIFO is 128 bytes
 * with its threshold at 32, so it has about 1.0 ms to service a full buffer at
 * 921600 and about 0.32 ms at this rate. Anything that blanks interrupts for
 * longer than that loses bytes mid-transfer, which is why #158 moved card
 * writes out of the transfer window. A body that cannot hold it puts all four
 * channels back on the default at boot and says so.
 *
 * `body.linkBaud` overrides this.
 */
#define NL_BAUD_PREFERRED 3000000

/*
 * How long a provisional baud lasts without a clean frame.
 *
 * Long enough for the body to finish its own switch and get a HELLO across at
 * the new rate, short enough that a person watching a bench does not think the
 * camera has died. The body's own revert has to be longer than this, so that
 * the node is always back on the default before the body gives up on it.
 */
#define NL_BAUD_PROBE_MS 2500

// Largest data slice in one NL_CMD_READ response (matches the KDP firmware
// chunk convention; well under KDP_MAX_PAYLOAD).
/*
 * 8192, and the size was tested rather than assumed.
 *
 * An overrun destroys the frame in flight, so shrinking chunks looked like it
 * should limit the damage. It did the opposite: at 2048 a 170 KB capture takes
 * 83 requests instead of 21 and the bench measured about one overrun per
 * request - 30 overruns and 30 retries in a single capture, against 4 with 8 KB
 * chunks. The hazard scales with the number of request/response turnarounds,
 * not with the bytes carried, so fewer and larger chunks is the cheaper trade.
 */
#define NL_CHUNK_MAX 8192
// Largest data slice in one NL_CMD_FW_CHUNK request. Smaller than a READ
// reply because the node's request decoder is sized for requests: 2 KB is
// 22 ms on the link and a 400 KB node image is 200 of them.
#define NL_FW_CHUNK_MAX 2048

typedef enum {
  // -> {} <- {product,protocol,firmware,sessionId,resetReason,chipRevision,
  //           heapKB,psramKB,baud,sensor,sensorPid,sensorDetected,autofocus,
  //           maxResolution}
  NL_CMD_HELLO = 0x01,
  // -> {} <- {state,frameId,frameSize?,heapKB,psramKB,tempC,crcFailures,resyncs,
  //           sensor?}
  /*
   * `sensor` is the last set NL_CMD_SENSOR actually got into the sensor on
   * this node, same field names and same units as the SENSOR reply's
   * `applied`. Only the fields the node has applied appear — and in practice
   * it is always present with at least `quality`, because camsensor_init
   * seeds the read-back JPEG quality on boot. Do not read presence as "the
   * P4 has configured this node".
   *
   * A bench diagnostic, not a control input: the P4 detects a node reset by
   * comparing HELLO's boot session (cam_link.c caches it per camera and
   * clears its change-only sensor cache on a mismatch), and nothing on the
   * P4 parses this field. It is here so a human at a terminal can ask a node
   * what its sensor is actually set to.
   */
  NL_CMD_STATUS = 0x02,
  // -> {resolution?,quality?} <- {ok,frameId,size,durationMs,crc32,heapKB,psramKB,
  //      cmdUs,fbGetUs,frameStartUs,frameAgeUs,
  //      syncSeq,syncEdgeUs|null,syncToCmdUs|null,syncToFrameUs|null}   (0.4.30+, #165:
  //      the node's own esp_timer; syncSeq counts SYNC_IN rising edges since boot and is
  //      the generation id; syncToFrameUs = frameStartUs - syncEdgeUs is the cross-node
  //      comparable figure; none of it is exposure time)
  NL_CMD_CAPTURE = 0x10,
  NL_CMD_READ = 0x11,    // -> {frameId,offset,length} <- BINARY slice (short past EOF)
  NL_CMD_RELEASE = 0x12, // -> {frameId} <- {ok}

  /*
   * ---- RESERVED, NOT IMPLEMENTED ----
   *
   * The arm/trigger flow. Specified here and deliberately unimplemented on
   * both ends: firmware/SYNC_FEASIBILITY.md (verdict SMALL_DRIVER_EXTENSION)
   * establishes that the mechanism is constructible, and the roadmap holds it
   * for M4 so that it is built against measured skew rather than a prediction.
   * A node that receives either of these today answers UNSUPPORTED_COMMAND,
   * which is the correct behaviour for a reserved opcode.
   *
   * Reserving the numbers now costs nothing and stops two people picking the
   * same one later.
   */

  /*
   * NL_CMD_ARM — prepare to capture on a GPIO edge instead of on a command.
   *
   *   -> {resolution?, quality?, timeoutMs?}
   *   <- {ok, armed, armReceivedUs, armedUs}
   *
   * The node prepares the sensor, holds its frame buffer so the driver's
   * capture stalls (buffer availability is the gate — see the study), installs
   * an ISR on BOARD_SYNC_IN, and reports ARMED. It must self-disarm after
   * `timeoutMs` so a node whose trigger never arrives returns to READY rather
   * than holding the buffer for ever.
   */
  NL_CMD_ARM = 0x13,

  /*
   * NL_CMD_TRIGGER_INFO — what the node observed about the last armed capture.
   *
   *   -> {}
   *   <- {ok, frameId, timing:{...}}
   *
   * Every timing field is nullable and MUST be null rather than 0 when the
   * node did not observe it. A fabricated timestamp here would be laundered
   * into a skew figure and then into a product claim.
   *
   *   armReceivedUs    node esp_timer at ARM receipt
   *   armedUs          node esp_timer once the sensor was held and the ISR set
   *   syncEdgeUs       node esp_timer in the GPIO ISR  (null if never fired)
   *   captureStartUs   node esp_timer when the buffer was released to the driver
   *   frameStartUs     camera_fb_t.timestamp — DMA start for the returned
   *                    frame. PUBLIC API, available today, and the one field
   *                    that anchors a cross-node comparison: the difference
   *                    (frameStartUs - syncEdgeUs) is comparable between nodes
   *                    with no clock synchronisation between them.
   *   frameCompleteUs  node esp_timer when esp_camera_fb_get() returned
   *
   * All values are that node's own esp_timer microseconds and share no epoch
   * with any other node or with the P4. Only DIFFERENCES within one node are
   * meaningful across nodes.
   *
   * What this is not: none of these is exposure skew. Frame start is not
   * exposure start, and a rolling shutter integrates per row. The three
   * kino.capture skews stay null with an unavailableReason regardless of what
   * this reports.
   */
  NL_CMD_TRIGGER_INFO = 0x14,

  /*
   * NL_CMD_SENSOR — put capture settings into the sensor before the shutter.
   *
   *   -> {aeLevel?, gainCeiling?, denoise?, sharpness?, quality?}
   *   <- {ok:true, applied:{...}}
   *
   * Why it exists: a QUAD slot carries exposureBias and gain per camera and
   * every look carries a capture block (jpegQuality, exposureBias, gainLimit,
   * denoise, sharpness), and until this command none of it reached a sensor.
   * The link could only ask for a resolution and a JPEG quality, so a slot set
   * to -1.5 EV and a slot set to 0 EV produced the same photograph and the
   * only honest thing to call the exposure controls was decorative.
   *
   * Request fields, all OPTIONAL — an absent field means "leave that knob as
   * it is", which is what makes the P4's change-only cache possible:
   *
   *   aeLevel      -2..2, the AEC target offset. The driver takes -5..5 on the
   *                OV3660; the link is narrower because that is the range
   *                Studio's exposureBias slider covers.
   *   gainCeiling  an X-FACTOR, not an enum ordinal: 2, 4, 8, 16, 32, 64 or
   *                128. Anything else is snapped to the nearest of those by
   *                the node, so a look's gainLimit of 12 may be sent as it is.
   *   denoise      0..8, 0 being off.
   *   sharpness    -3..3.
   *   quality      the SENSOR's JPEG scale, 5..63, where LOWER is better —
   *                not the 60..95 percentage the KDP contract and Studio use.
   *                The P4 converts (pure_quality_to_sensor). Optional because
   *                NL_CMD_CAPTURE also carries it.
   *
   * The reply's `applied` echoes what the sensor accepted AFTER clamping and
   * snapping, field by field, and it is the only truthful record of the
   * exposure: META.JSON stores this, never what was asked. A knob the node
   * could not write (no such setter on the detected part, or the driver
   * refused the value) is simply absent from `applied`.
   *
   * NACK HARDWARE_ERROR when no sensor answered the node's bus. A NACK or a
   * timeout does not stop the capture: a photograph taken with the previous
   * settings beats no photograph.
   */
  NL_CMD_SENSOR = 0x15,

  /*
   * NL_CMD_SET_BAUD - change the link's speed, with a way back.
   *
   *   -> {baud}     one of NL_BAUD_SUPPORTED
   *   <- {ok, baud, revertMs}   sent at the OLD baud, before the switch
   *
   * The reply goes out at the current rate and the node switches only once
   * that reply has left the shift register. So the body always hears the
   * acknowledgement, whatever happens next.
   *
   * THE REVERT IS THE POINT. This link has no flow control and no out-of-band
   * channel: if the two ends disagree about the rate, nothing either of them
   * sends can say so. The node therefore treats a switch as provisional. It
   * arms a deadline of `revertMs`, and unless a frame decodes cleanly at the
   * new rate before then, it puts the baud back to NL_DEFAULT_BAUD. The body
   * has the same rule in reverse, so a failed negotiation costs a couple of
   * seconds and settles back where it started.
   *
   * A capture in flight is not a good moment: the node refuses with BUSY
   * while it holds a frame.
   */
  NL_CMD_SET_BAUD = 0x16,

  NL_CMD_REBOOT = 0x20,  // -> {} <- {ok}, then the node restarts

  /*
   * Firmware update, proxied by the P4 from the host's FW_* session
   * (firmware/p4/main/fw_update.c). The node writes the image into the OTA
   * slot it is not running, verifies the whole thing against the SHA-256
   * named at BEGIN, selects the slot and restarts. Its bootloader has
   * rollback armed: the image confirms itself when it answers its first
   * HELLO, and an image that never does is rolled back on the next reset,
   * which the P4 forces by cycling the camera bank.
   *
   *   FW_BEGIN -> {size, sha256, version}  <- {ok, chunkSize, slot}
   *   FW_CHUNK -> BINARY: u32 LE offset, then data  <- {ok, received}
   *   FW_END   -> {}  <- {ok, verified}, then the node restarts
   *   FW_ABORT -> {}  <- {ok}
   *
   * Refusals: BAD_SIZE, BAD_OFFSET (chunks are in order), NO_SESSION,
   * SHORT_IMAGE, CHECKSUM_FAILED, FLASH_WRITE, HARDWARE_ERROR (a node still on
   * the single-app table has no slot to write), BUSY (a capture is held).
   */
  NL_CMD_FW_BEGIN = 0x30,
  NL_CMD_FW_CHUNK = 0x31,
  NL_CMD_FW_END = 0x32,
  NL_CMD_FW_ABORT = 0x33,
} nl_cmd_t;

// Node state machine, reported as strings in NL_CMD_STATUS. The P4 maps
// these onto the KDP CameraState vocabulary.
#define NL_STATE_BOOTING "booting"
#define NL_STATE_INIT_SENSOR "initializing-sensor"
#define NL_STATE_READY "ready"
#define NL_STATE_EXPOSING "exposing"
#define NL_STATE_JPEG_READY "jpeg-ready"
#define NL_STATE_TRANSFERRING "transferring"
#define NL_STATE_ERROR "error"
/* RESERVED alongside NL_CMD_ARM: sensor prepared, frame buffer held, GPIO ISR
 * installed, waiting for the trigger edge. No node reports this yet. */
#define NL_STATE_ARMED "armed"

#endif
