b5463/kino-d4/firmware/p4/main/kdp_server.c

// Studio-facing KDP server, Milestone 1B surface. Contract rules honored
// here: never silently time out (every request gets a response or a NACK);
// capability flags and the dispatcher agree; REBOOT answers before
// restarting; HELLO tolerates a payload carrying only {nonce}; job events
// carry sequence 0 and are batched (~10%), never per unit of work.
#include "kdp_server.h"

#include <stdarg.h>
#include <stdatomic.h>
#include <string.h>
#include <sys/time.h>
#include <time.h>

#include "bench_c6.h"
#include "cam_link.h"
#include "capture.h"
#include "fw_update.h"
#include "viewfinder.h"
#include "clock.h"
#include <dirent.h>
#include <sys/stat.h>

#include "config_store.h"
#include "roll_state.h"
#include "cJSON.h"
#include "gallery.h"
#include "upload_queue.h"
#include "gallery_index.h"
#include "driver/temperature_sensor.h"
#include "factory_reset.h"
#include "esp_heap_caps.h"
#include "esp_log.h"
#include "esp_random.h"
#include "esp_system.h"
#include "esp_timer.h"
#include "freertos/FreeRTOS.h"
#include "freertos/semphr.h"
#include "freertos/queue.h"
#include "freertos/task.h"
#include "hardware_validation.h"
#include "kdp_net.h"
#include "kdp_recipes.h"
#include "kdp_sounds.h"
#include "kdp/crc32.h"
#include "kdp/decoder.h"
#include "kdp/packet.h"
#include "kdp/protocol.h"
#include "klog.h"
#include "lid.h"
#include "meta.h"
#include "net_link.h"
#include "ui.h"
/* Unconditional, like main.c:26. net_hosted.h selects the real declarations
 * under KINO_RADIO and inline stubs otherwise, so every caller compiles in
 * every config. This include was guarded on KINO_C6_RESET_BENCH (opt-in, off
 * in both shipped configs) while handle_runtime_stats() calls
 * net_hosted_recovery_ready() unconditionally - d7413c2 (#162) failed to
 * build in both configs with an implicit declaration. */
#include "net_hosted.h"
#include "node_link/node_link.h"
#include "power.h"
#include "pure.h"
#include "storage.h"
#include "upload_store.h"
#include "taskmon.h"
#include "usb_link.h"

static const char *TAG = "kdp_server";

static kdp_identity_t s_id;
static kdp_decoder_t s_decoder;
/* The two KDP frame buffers, KDP_MAX_FRAME (16 KiB) each. In PSRAM, not
 * internal RAM: nothing here needs DMA-capable memory (the USB-Serial-JTAG
 * driver copies into its own ring), and internal RAM is what the P4 is short
 * of - ESP-Hosted's SDIO buffers can only live there, and a radio recovery
 * has to find 16 KiB of it twice (net_hosted.c, the recovery reserve). Kept
 * static until 0.4.6, which cost 32 KiB of the scarcest memory on the board. */
static uint8_t *s_decode_buf;
static uint8_t *s_tx;
static SemaphoreHandle_t s_tx_lock;
static bool s_usb_seen; /* first decoded host frame marks USB validated */

// One capture pipeline at a time: CAMERA_TEST, STORAGE_SELF_TEST, STORAGE_BENCH
// and the soak job all contend for the camera UART, the PSRAM staging buffer
// and the SD write path - and so does the product capture in capture.c. They
// share capture_lock()/capture_unlock() (capture.h), which used to be a second
// mutex here that capture_fire() never looked at. Held for a whole soak run;
// concurrent starts, including a shutter press, get BUSY.

/* Events this device could not put on the wire, reported by GET_RUNTIME_STATS
 * as droppedLogEvents. Written from klog()'s caller - the UI task, the
 * capture workers, the radio supervisor - and from the log drain task, so
 * atomic: a plain ++ on this is a read-modify-write those tasks interleave. */
static _Atomic uint32_t s_log_dropped;

static uint32_t s_job_counter;
static volatile bool s_soak_running;
static volatile bool s_selftest_running;
static temperature_sensor_handle_t s_tsens;

// ---- small helpers ----

static const char *reset_reason_str(void) {
  switch (esp_reset_reason()) {
    case ESP_RST_POWERON: return "power-on";
    case ESP_RST_EXT: return "external";
    case ESP_RST_SW: return "software";
    case ESP_RST_PANIC: return "panic";
    case ESP_RST_INT_WDT: return "int-wdt";
    case ESP_RST_TASK_WDT: return "task-wdt";
    case ESP_RST_WDT: return "wdt";
    case ESP_RST_DEEPSLEEP: return "deep-sleep";
    case ESP_RST_BROWNOUT: return "brownout";
    case ESP_RST_SDIO: return "sdio";
    case ESP_RST_USB: return "usb";
    case ESP_RST_JTAG: return "jtag";
    default: return "unknown";
  }
}

static uint32_t heap_kb(void) { return (uint32_t)(esp_get_free_heap_size() / 1024); }
static uint32_t psram_kb(void) {
  return (uint32_t)(heap_caps_get_free_size(MALLOC_CAP_SPIRAM) / 1024);
}

static uint32_t elapsed_ms(int64_t since_us) {
  return (uint32_t)((esp_timer_get_time() - since_us) / 1000);
}

/**
 * One numeric request argument, clamped to [lo, hi] before it becomes an
 * integer. `dflt` is the answer when the field is absent or not a number.
 *
 * The clamp used to run after the cast - `(long)j->valuedouble`, then a range
 * check on the long. cJSON hands back a double, and a host is free to write
 * 1e400, which parses to infinity; casting that to long is undefined, not
 * saturating. NaN takes the same path here as a value below lo.
 */
static long clamp_num(const cJSON *n, double lo, double hi, long dflt) {
  if (!cJSON_IsNumber(n)) return dflt;
  const double v = n->valuedouble;
  if (!(v >= lo)) return (long)lo; /* negated so NaN lands here too */
  if (v > hi) return (long)hi;
  return (long)v;
}

// ---- send helpers ----

/*
 * Every wait on this path is bounded, and that is the whole fix.
 *
 * RESPONSE_WRITE_TIMEOUT_MS is a response's budget on the wire. It used to be
 * portMAX_DELAY: a host that opened the port and stopped reading parked the KDP
 * task inside usb_link_write() forever, holding s_tx_lock, and the log drain
 * task then blocked in xSemaphoreTake(portMAX_DELAY) - so the event path's
 * 250 ms deadline, which exists precisely so nothing waits on a dead host,
 * could not be reached. Both tasks wedged until the cable moved.
 *
 * 1500 ms, not 250: a response is what the host asked for and is worth waiting
 * for. The USB-Serial-JTAG TX ring is 4096 bytes and a reply is now up to
 * 16 KiB in 1024-byte slices, so a host reading slowly - a debugger stepping,
 * a busy event loop - must not lose its reply to an impatient deadline. A host
 * that has taken nothing for a second and a half is not reading.
 *
 * TX_LOCK_TIMEOUT_MS is the wait for the lock itself, and it is longer than one
 * write can take so that a queued sender fails only when the holder is itself
 * failing. A response charges either give-up to s_tx_dropped; an event's
 * give-ups are counted once, by send_event(), in s_log_dropped.
 */
#define RESPONSE_WRITE_TIMEOUT_MS 1500
#define TX_LOCK_TIMEOUT_MS 2000

/* The bench camera path's per-chunk read budget. The same 250 ms the shutter
 * path uses (capture.c, CHUNK_READ_TIMEOUT_MS) and for the same measured
 * reason: a healthy chunk under four-way load is ~120 ms and a lost tail is
 * never coming, so this is the price of every failure. It was 3000 here,
 * which made one dropped tail cost twelve times what the product pays.
 * The bench path stays retry-free - see the call site. */
#define BENCH_CHUNK_READ_TIMEOUT_MS 250

/* How long an event may hold the TX lock. Long enough that a host between
 * two reads never loses one, short enough that server_task's next response
 * waits a quarter second rather than until a cable is plugged back in. */
#define EVENT_WRITE_TIMEOUT_MS 250

/* RESPONSES this device could not put on the wire: the lock was held past
 * TX_LOCK_TIMEOUT_MS, or the host did not take the whole frame in time.
 * Responses only - an event that fails either way is send_event()'s to count,
 * in s_log_dropped. Reported beside it (GET_RUNTIME_STATS, droppedTxFrames)
 * because the two answer different questions and must not overlap: a dropped
 * log event costs a line in Studio's console, a dropped response is a command
 * the host will report as a timeout. */
static _Atomic uint32_t s_tx_dropped;

/* Requests and responses: the host asked, so this waits for the wire - but
 * with a deadline. A short write leaves a partial frame the host's decoder
 * resyncs past on the next KI magic (usb_link.h), which the host sees as the
 * command timing out. That is the same outcome as before for the host, and
 * unlike before it does not take the rest of the server with it. */
static void send_raw(uint8_t type, uint8_t flags, uint32_t seq, const uint8_t *payload,
                     uint32_t len) {
  if (xSemaphoreTake(s_tx_lock, pdMS_TO_TICKS(TX_LOCK_TIMEOUT_MS)) != pdTRUE) {
    atomic_fetch_add(&s_tx_dropped, 1);
    return;
  }
  size_t total = kdp_encode_frame(s_tx, KDP_MAX_FRAME, KDP_PROTOCOL_VERSION, type, flags,
                                  seq, payload, len);
  if (total > 0 &&
      usb_link_write_timeout(s_tx, total, RESPONSE_WRITE_TIMEOUT_MS) != (int)total) {
    atomic_fetch_add(&s_tx_dropped, 1);
  }
  xSemaphoreGive(s_tx_lock);
}

/**
 * One event frame, with a deadline. Returns false when the host did not take
 * all of it and the event is lost.
 *
 * The lock and the wire were both blocking: send_raw() takes s_tx_lock with
 * portMAX_DELAY and usb_link_write() waits forever on a TX FIFO nobody is
 * draining. The drain task is allowed to wait there - that is its job - but
 * it holds s_tx_lock while it does, and server_task needs the same lock to
 * answer the next request. One unplugged cable and a full FIFO wedged the
 * whole server behind an event nobody was reading.
 */
static bool send_raw_event(uint8_t evt, uint32_t seq, const uint8_t *payload, uint32_t len) {
  /* Bounded here too. The deadline on the write is no use while the wait for
   * the lock is unbounded: a response ahead of this one owns the lock for up to
   * RESPONSE_WRITE_TIMEOUT_MS, and an event that queues behind it forever is
   * the drain task stalled again, one level up. */
  if (xSemaphoreTake(s_tx_lock, pdMS_TO_TICKS(TX_LOCK_TIMEOUT_MS)) != pdTRUE) {
    /* Not charged to s_tx_dropped: send_event() counts every false return in
     * s_log_dropped, and charging both would make droppedTxFrames overlap the
     * counter it exists to be distinguished from. s_tx_dropped is responses
     * only. */
    return false;
  }
  const size_t total = kdp_encode_frame(s_tx, KDP_MAX_FRAME, KDP_PROTOCOL_VERSION, evt,
                                        KDP_FLAG_EVENT, seq, payload, len);
  bool sent = false;
  if (total > 0) sent = usb_link_write_timeout(s_tx, total, EVENT_WRITE_TIMEOUT_MS) == (int)total;
  xSemaphoreGive(s_tx_lock);
  return sent;
}

static void send_nack(uint8_t type, uint32_t seq, const char *code, const char *message);

/* Defined with the rest of the MEDIA card bookkeeping, ~1800 lines below, and
 * called from the MEDIA handlers above it: the bytes are in RAM by then and
 * the reply can take 3.5 s, so the card is released before the wire work
 * rather than after the handler returns. Declared here because a static
 * definition after an implicit one is an error, not a warning. */
static void media_card_done(void);

static void send_json(uint8_t type, uint32_t seq, cJSON *json) {
  char *text = cJSON_PrintUnformatted(json);
  cJSON_Delete(json);
  if (text == NULL) return;
  /* An oversized reply would be dropped by kdp_encode_frame — the client
   * would see only a timeout. A NACK is the honest failure (issue #80). */
  if (strlen(text) > KDP_MAX_PAYLOAD) {
    cJSON_free(text);
    send_nack(type, seq, "INTERNAL_ERROR", "Reply exceeds the frame payload cap");
    return;
  }
  send_raw(type, KDP_FLAG_RESPONSE, seq, (const uint8_t *)text, strlen(text));
  cJSON_free(text);
}

static void send_event(uint8_t evt, cJSON *json) {
  char *text = cJSON_PrintUnformatted(json);
  cJSON_Delete(json);
  if (text == NULL) return;
  /* Events carry no meaningful sequence — the reference device writes 0. */
  if (!send_raw_event(evt, 0, (const uint8_t *)text, strlen(text))) {
    /* Same counter and the same trade as a full log queue: the ring in
     * klog.c still has the line, GET_LOGS still serves it, and
     * GET_RUNTIME_STATS says how many went missing on the wire. */
    atomic_fetch_add(&s_log_dropped, 1);
  }
  cJSON_free(text);
}

static void send_nack(uint8_t type, uint32_t seq, const char *code, const char *message) {
  cJSON *json = cJSON_CreateObject();
  cJSON_AddStringToObject(json, "code", code);
  cJSON_AddStringToObject(json, "message", message);
  char *text = cJSON_PrintUnformatted(json);
  cJSON_Delete(json);
  if (text == NULL) return;
  send_raw(type, KDP_FLAG_RESPONSE | KDP_FLAG_ERROR, seq, (const uint8_t *)text,
           strlen(text));
  cJSON_free(text);
}

/**
 * Send one kdp_net.c reply: the body on success, a NACK with its code and
 * message otherwise.
 *
 * The point of the split is that the refusals stay specific. A command that
 * needs the radio answers `NETWORK_UNAVAILABLE` naming the actual radio state
 * rather than falling through to the dispatch default's
 * `UNSUPPORTED_COMMAND` — "this firmware cannot do that" and "this body has
 * no route to its radio" send someone to different places.
 */
static void send_net(uint8_t type, uint32_t seq, kdp_net_reply_t reply) {
  if (reply.ok) {
    send_json(type, seq, reply.json); /* takes ownership */
    return;
  }
  send_nack(type, seq, reply.code, reply.message);
}

/* The same idea for the feature modules (kdp_module.h): JSON, raw bytes, or
 * a NACK, decided by the module and sent here. */
static void send_module(uint8_t type, uint32_t seq, kdp_module_reply_t reply) {
  if (!reply.ok) {
    send_nack(type, seq, reply.code, reply.message);
    return;
  }
  if (reply.json != NULL) {
    send_json(type, seq, reply.json); /* takes ownership */
    return;
  }
  send_raw(type, KDP_FLAG_RESPONSE | KDP_FLAG_BINARY, seq, reply.bytes, reply.bytes_len);
}

// ---- capture core ----
// The measured single-camera path: ping -> node capture -> chunked transfer
// into PSRAM (verified against the node's CRC) -> SD write -> stored-file
// read-back CRC. Timing buckets are wall-clock on the P4 side; none of them
// is exposure timing and none may ever be reported as skew.

typedef struct {
  bool ok;
  const char *err_code; /* one of the §14 codes when !ok */
  char err_msg[96];
  char capture_uuid[40];
  char capture_id[16];
  char dir[64];
  uint32_t jpeg_bytes;
  uint32_t t_request_to_node_ms;
  uint32_t t_capture_ms;
  uint32_t t_transfer_ms;
  uint32_t t_sd_ms;
  uint32_t t_total_ms;
  char crc_node[12];
  char crc_transfer[12];
  char crc_stored[12];
  bool crc_match;
  uint32_t p4_heap_before, p4_heap_after;
  uint32_t p4_psram_before, p4_psram_after;
  int32_t node_heap_kb, node_psram_kb;
} capture_result_t;

static const char *CAPTURE_RESOLUTION = "1600x1200";

static char *build_meta_json(const capture_result_t *r, const char *node_fw) {
  // kino.capture v1. Diagnostic figures ride as passthrough fields; the
  // reserved `timing` skew block stays absent — no telemetry exists yet and
  // faking keys is worse than absence (contract D6).
  cJSON *json = cJSON_CreateObject();
  cJSON_AddStringToObject(json, "schema", "kino.capture");
  cJSON_AddNumberToObject(json, "version", 1);
  cJSON_AddStringToObject(json, "id", r->capture_id);
  cJSON_AddStringToObject(json, "captureUuid", r->capture_uuid);
  cJSON_AddStringToObject(json, "deviceId", s_id.device_id);
  cJSON_AddStringToObject(json, "mode", "single");
  char stamp[40];
  clock_iso8601(stamp, sizeof stamp);
  cJSON_AddStringToObject(json, "capturedAt", stamp);
  cJSON_AddNumberToObject(json, "capturedAtMs", (double)clock_now_ms());
  cJSON_AddStringToObject(json, "clockSource", clock_source_str());
  cJSON_AddNumberToObject(json, "frameCount", 1);
  cJSON_AddStringToObject(json, "resolution", CAPTURE_RESOLUTION);
  cJSON_AddStringToObject(json, "status", "ready");
  cJSON_AddBoolToObject(json, "visible", true);

  cJSON_AddNumberToObject(json, "cameraCount", 1);
  cJSON_AddNumberToObject(json, "cameraIndex", 1);
  cJSON_AddNumberToObject(json, "jpegBytes", r->jpeg_bytes);
  cJSON_AddStringToObject(json, "p4Firmware", KINO_FW_VERSION);
  cJSON_AddStringToObject(json, "nodeFirmware", node_fw);

  cJSON *bench = cJSON_AddObjectToObject(json, "benchTiming");
  cJSON_AddNumberToObject(bench, "requestToNodeMs", r->t_request_to_node_ms);
  cJSON_AddNumberToObject(bench, "captureCommandToJpegReadyMs", r->t_capture_ms);
  cJSON_AddNumberToObject(bench, "jpegTransferMs", r->t_transfer_ms);
  cJSON_AddNumberToObject(bench, "sdWriteMs", r->t_sd_ms);

  cJSON *sums = cJSON_AddObjectToObject(json, "checksums");
  cJSON_AddStringToObject(sums, "nodeJpegCrc32", r->crc_node);
  cJSON_AddStringToObject(sums, "transferCrc32", r->crc_transfer);
  cJSON_AddStringToObject(sums, "storedFileCrc32", r->crc_stored);

  char *text = cJSON_PrintUnformatted(json);
  cJSON_Delete(json);
  return text;
}

static void fail(capture_result_t *r, const char *code, const char *msg) {
  r->ok = false;
  r->err_code = code;
  strlcpy(r->err_msg, msg, sizeof r->err_msg);
  r->err_msg[sizeof r->err_msg - 1] = '\0';
}

/**
 * fail() with the numbers in it. A bench failure that reports only what went
 * wrong costs another run to find out how far it got; these carry the
 * measurement with them so the first run is also the diagnostic one. The
 * code stays a fixed contract string — only the human message varies.
 */
static void failf(capture_result_t *r, const char *code, const char *fmt, ...) {
  r->ok = false;
  r->err_code = code;
  va_list args;
  va_start(args, fmt);
  vsnprintf(r->err_msg, sizeof r->err_msg, fmt, args);
  va_end(args);
}

/* Caller must hold capture_lock(). */
/* The channel's klog source and wire id. CAMERA_TEST reaches all four
 * channels since the four-camera bench (2026-08-30); everything below is per
 * channel because every camlink call has been per channel since M1. */
static const char *cam_tag(int cam) {
  static const char *TAGS[4] = {"C1", "C2", "C3", "C4"};
  return (cam >= 0 && cam < 4) ? TAGS[cam] : "P4";
}
static const char *cam_id_str(int cam) {
  static const char *IDS[4] = {"cam1", "cam2", "cam3", "cam4"};
  return (cam >= 0 && cam < 4) ? IDS[cam] : "cam?";
}

static void run_capture(int cam, int jpeg_quality, bool keep_files, capture_result_t *r) {
  memset(r, 0, sizeof *r);
  r->node_heap_kb = -1;
  r->node_psram_kb = -1;
  r->p4_heap_before = heap_kb();
  r->p4_psram_before = psram_kb();
  int64_t t0 = esp_timer_get_time();

  camlink_info_t info;
  camlink_get_info_ch(cam, &info);
  if (!info.online) {
    fail(r, "CAMERA_OFFLINE", "Camera node not connected");
    return;
  }
  if (!info.sensor_detected) {
    fail(r, "SENSOR_NOT_DETECTED", "Node answers but reports no sensor");
    return;
  }
  if (!storage_present()) {
    fail(r, "SD_NOT_MOUNTED", "No durable storage path");
    return;
  }

  // Link health probe — the request-to-node bucket.
  uint32_t rtt = 0;
  if (camlink_ping_ch(cam, &rtt) != ESP_OK) {
    camlink_stats_t s;
    camlink_get_stats_ch(cam, &s);
    failf(r, "NODE_BOOT_TIMEOUT", "Node stopped answering: %lu timeouts, %lu crc, last %s",
          (unsigned long)s.timeouts, (unsigned long)s.crc_errors,
          s.last_error[0] != '\0' ? s.last_error : "-");
    return;
  }
  r->t_request_to_node_ms = rtt;

  // Node capture.
  int64_t t_cap = esp_timer_get_time();
  camlink_capture_result_t cap;
  esp_err_t err = camlink_capture_ch(cam, CAPTURE_RESOLUTION, jpeg_quality,
                                     12000 /* cam_link's CAPTURE_TIMEOUT_MS */, &cap);
  if (err == ESP_ERR_TIMEOUT) {
    failf(r, "TRANSFER_TIMEOUT", "Capture command timed out after %lu ms",
          (unsigned long)elapsed_ms(t_cap));
    return;
  }
  if (err != ESP_OK) {
    fail(r, "CAPTURE_FAILED", "Node rejected or failed the capture");
    return;
  }
  r->t_capture_ms = elapsed_ms(t_cap);
  r->jpeg_bytes = cap.size;
  /* snprintf, not strncpy: at -O2 GCC proves the strncpy form can leave the
   * field unterminated and -Werror=stringop-truncation stops the build. */
  snprintf(r->crc_node, sizeof r->crc_node, "%s", cap.crc32);
  r->node_heap_kb = cap.heap_kb;
  r->node_psram_kb = cap.psram_kb;
  /* Both ends, like capture.c: a size near 4 GB is a node describing memory it
   * does not have, and the allocation below would then be sized by arithmetic
   * on a lie. 1 MiB is twice the largest real frame measured. */
  if (cap.size < 4 || cap.size > 1024u * 1024u) {
    camlink_release_ch(cam, cap.frame_id);
    failf(r, "JPEG_INVALID", "Node reported an implausible JPEG size: %lu B",
          (unsigned long)cap.size);
    return;
  }

  // Transfer into PSRAM, CRC on the fly.
  uint8_t *jpeg = heap_caps_malloc(cap.size, MALLOC_CAP_SPIRAM);
  if (jpeg == NULL) jpeg = malloc(cap.size);
  if (jpeg == NULL) {
    camlink_release_ch(cam, cap.frame_id);
    /* How short we were is the whole point: a 40 KB miss is a tuning
     * problem and a 400 KB miss is a design one. */
    failf(r, "OUT_OF_MEMORY", "JPEG staging wants %lu B, free %lu KB psram / %lu KB heap",
          (unsigned long)cap.size, (unsigned long)psram_kb(), (unsigned long)heap_kb());
    return;
  }

  int64_t t_xfer = esp_timer_get_time();
  uint32_t crc_state = kdp_crc32_begin();
  uint32_t offset = 0;
  while (offset < cap.size) {
    size_t want = cap.size - offset;
    if (want > NL_CHUNK_MAX) want = NL_CHUNK_MAX;
    size_t got = 0;
    /*
     * The SHUTTER path's chunk budget, on the shutter path's reasoning.
     *
     * This was 3000 ms - cam_link's DEFAULT_TIMEOUT_MS - while capture.c uses
     * 250. Two policies for one cable: a dropped tail cost the bench path the
     * full 3 s and then failed the frame, so the same fault measured 12x
     * longer here than in the product and looked like a different fault.
     *
     * 250 is not arbitrary, it is measured: a healthy chunk under four-way
     * load takes ~120 ms (CAMERA_LINK_STATS latencyMaxMs 122), and a lost tail
     * is never coming, so the timeout IS the price of the failure. See
     * capture.c's CHUNK_READ_TIMEOUT_MS.
     *
     * STILL RETRY-FREE, deliberately. capture.c's own note on its retry loop
     * says it is "deliberately NOT added to CAMERA_TEST. That path is the
     * bench control for raw link behaviour, and retrying there would hide the
     * very faults it exists to measure." That reasoning holds: this is the
     * control. Only the budget is unified, not the policy.
     */
    esp_err_t rerr = camlink_read_ch(cam, cap.frame_id, offset, jpeg + offset, want,
                                     BENCH_CHUNK_READ_TIMEOUT_MS, &got);
    if (rerr != ESP_OK || got == 0) {
      /* Where it died is the measurement. Failing at the first chunk is a
       * link fault; failing at 80% is a throughput or timeout budget the
       * bench can retune. */
      /* Say what the link said. This used to be hardcoded TRANSFER_TIMEOUT,
       * which is a lie when the node answered BAD_ID - and it did, because a
       * viewfinder frame had replaced the frame being transferred. An hour
       * went into timeout budgets and signal integrity before the real NACK
       * surfaced from CAMERA_LINK_STATS instead of from the error itself. */
      camlink_stats_t xs;
      camlink_get_stats_ch(cam, &xs);
      const bool timed_out = strcmp(xs.last_error, "TIMEOUT") == 0;
      failf(r, timed_out ? "TRANSFER_TIMEOUT" : "TRANSFER_FAILED",
            "Chunk read failed at %lu/%lu B (%lu%%) after %lu ms; link reports %s",
            (unsigned long)offset, (unsigned long)cap.size,
            (unsigned long)(cap.size == 0 ? 0 : (uint64_t)offset * 100 / cap.size),
            (unsigned long)elapsed_ms(t_xfer),
            xs.last_error[0] != '\0' ? xs.last_error : "nothing");
      free(jpeg);
      camlink_release_ch(cam, cap.frame_id);
      return;
    }
    crc_state = kdp_crc32_update(crc_state, jpeg + offset, got);
    offset += got;
  }
  r->t_transfer_ms = elapsed_ms(t_xfer);
  camlink_release_ch(cam, cap.frame_id);

  snprintf(r->crc_transfer, sizeof r->crc_transfer, "%08lx",
           (unsigned long)kdp_crc32_final(crc_state));
  if (r->crc_node[0] != '\0' && strcmp(r->crc_node, r->crc_transfer) != 0) {
    free(jpeg);
    failf(r, "TRANSFER_CRC_MISMATCH", "Checksums disagree over %lu B: node %s, transfer %s",
          (unsigned long)cap.size, r->crc_node, r->crc_transfer);
    return;
  }
  // JPEG sanity: SOI marker.
  if (jpeg[0] != 0xFF || jpeg[1] != 0xD8) {
    free(jpeg);
    fail(r, "JPEG_INVALID", "Payload does not start with a JPEG SOI marker");
    return;
  }
  /* hwv_cam_item maps to the CAM2-4 registry rows; items without a per-cam
   * row come back HWV_COUNT and hwv_mark_validated ignores them. */
  hwv_mark_validated(hwv_cam_item(cam, HWV_CAM1_CAPTURE), "checksummed capture");
  hwv_mark_validated(hwv_cam_item(cam, HWV_CAM1_JPEG_TRANSFER), "transfer CRC matched node CRC");

  // SD write.
  capture_uuid4(r->capture_uuid, sizeof r->capture_uuid);
  int64_t t_sd = esp_timer_get_time();
  storage_capture_t capture;
  if (storage_capture_open(&capture, r->capture_uuid, "TC") != ESP_OK) {
    free(jpeg);
    fail(r, "SD_WRITE_FAILED", "Could not open the capture folder");
    return;
  }
  /* The frame keeps the channel's own name: a TC folder from cam3 holds
   * C3.JPG, the same name a product capture would give that camera's frame. */
  if (storage_capture_frame_begin(&capture, cam) != ESP_OK) {
    storage_capture_abort(&capture);
    free(jpeg);
    fail(r, "SD_WRITE_FAILED", "Could not open the frame file");
    return;
  }
  snprintf(r->capture_id, sizeof r->capture_id, "%s", capture.id);
  snprintf(r->dir, sizeof r->dir, "%s", capture.dir);
  if (storage_capture_append(&capture, jpeg, cap.size) != ESP_OK) {
    storage_capture_abort(&capture);
    free(jpeg);
    fail(r, "SD_WRITE_FAILED", "JPEG write failed");
    return;
  }
  free(jpeg);

  camlink_info_t node;
  camlink_get_info_ch(cam, &node);
  char *meta = build_meta_json(r, node.firmware);
  esp_err_t committed = meta != NULL ? storage_capture_commit(&capture, meta) : ESP_FAIL;
  if (meta != NULL) cJSON_free(meta);
  if (committed != ESP_OK) {
    storage_capture_abort(&capture);
    fail(r, "SD_WRITE_FAILED", "Commit failed");
    return;
  }
  r->t_sd_ms = elapsed_ms(t_sd);

  // Stored-file read-back — the third checksum.
  char path[80];
  snprintf(path, sizeof path, "%s/C%d.JPG", capture.dir, cam + 1);
  uint32_t stored_crc = 0, stored_bytes = 0;
  if (storage_file_crc32(path, &stored_crc, &stored_bytes) != ESP_OK) {
    fail(r, "SD_VERIFY_FAILED", "Stored file could not be read back");
    return;
  }
  snprintf(r->crc_stored, sizeof r->crc_stored, "%08lx", (unsigned long)stored_crc);
  if (stored_bytes != cap.size || strcmp(r->crc_stored, r->crc_transfer) != 0) {
    fail(r, "SD_VERIFY_FAILED", "Stored file checksum disagrees with transfer");
    return;
  }
  hwv_mark_validated(hwv_cam_item(cam, HWV_CAM1_SD_WRITE), "stored file checksum verified");

  r->crc_match = true;
  r->ok = true;
  r->t_total_ms = elapsed_ms(t0);
  r->p4_heap_after = heap_kb();
  r->p4_psram_after = psram_kb();

  klog(cam_tag(cam), "capture %s ok — %lu KB in %lu ms, crc %s verified", r->capture_id,
       (unsigned long)(r->jpeg_bytes / 1024), (unsigned long)r->t_total_ms,
       r->crc_transfer);

  if (!keep_files) {
    storage_capture_delete(r->dir);
    r->dir[0] = '\0';
  }
}

// ---- handlers ----

static void handle_hello(uint32_t seq, cJSON *req) {
  int proto_min = KDP_PROTOCOL_VERSION;
  int proto_max = KDP_PROTOCOL_VERSION;
  const cJSON *min = cJSON_GetObjectItem(req, "protocolMin");
  const cJSON *max = cJSON_GetObjectItem(req, "protocolMax");
  if (cJSON_IsNumber(min)) proto_min = min->valueint;
  if (cJSON_IsNumber(max)) proto_max = max->valueint;
  if (KDP_PROTOCOL_VERSION < proto_min || KDP_PROTOCOL_VERSION > proto_max) {
    send_nack(KDP_CMD_HELLO, seq, "BAD_VERSION", "No common protocol version");
    return;
  }

  /* Take the host's clock if it offered one.
   *
   * The D4 has no RTC and no network, so this is the only way it ever learns
   * the date. HELLO is the right carrier because it is the first thing every
   * host sends and the only one guaranteed to arrive before a capture can.
   * Both fields are optional and additive: a host that omits them gets the
   * same reply it always did, and the camera keeps saying its timestamps are
   * unset rather than pretending otherwise. */
  const cJSON *host_ms = cJSON_GetObjectItem(req, "hostEpochMs");
  if (cJSON_IsNumber(host_ms)) {
    const cJSON *off = cJSON_GetObjectItem(req, "hostUtcOffsetMin");
    clock_set((int64_t)host_ms->valuedouble, cJSON_IsNumber(off) ? off->valueint : 0);
  }

  cJSON *json = cJSON_CreateObject();
  cJSON_AddStringToObject(json, "product", "KINO");
  cJSON_AddNumberToObject(json, "protocol", KDP_PROTOCOL_VERSION);
  const cJSON *nonce = cJSON_GetObjectItem(req, "nonce");
  if (cJSON_IsNumber(nonce)) cJSON_AddNumberToObject(json, "nonce", nonce->valuedouble);
  cJSON_AddStringToObject(json, "deviceId", s_id.device_id);
  cJSON_AddStringToObject(json, "sessionId", s_id.session_id);
  /* So a host can see whether its clock was taken, and whether this camera
   * needs one at all. */
  cJSON_AddStringToObject(json, "clockSource", clock_source_str());
  send_json(KDP_CMD_HELLO, seq, json);
}

static void handle_capabilities(uint32_t seq) {
  cJSON *json = cJSON_CreateObject();
  cJSON_AddNumberToObject(json, "protocol", KDP_PROTOCOL_VERSION);
  cJSON_AddStringToObject(json, "hardware", "kino-v1");
  cJSON_AddStringToObject(json, "firmware", KINO_FW_VERSION);

  // Every flag false until the feature exists; benchDiagnostics is the one
  // Milestone 1B surface this build actually implements.
  cJSON *caps = cJSON_AddObjectToObject(json, "capabilities");
  cJSON_AddNumberToObject(caps, "cameraCount", 4);
  const char *flags[] = {"vsyncTelemetry", "phaseCalibration", "linkBench"};
  for (size_t i = 0; i < sizeof flags / sizeof flags[0]; i++) {
    cJSON_AddBoolToObject(caps, flags[i], false);
  }
  /* Owned by their modules, so the flag and the handler cannot disagree:
   * each is true exactly when the module answers its commands. */
  /* FW_BEGIN/CHUNK/END/ABORT/STATUS answer for p4 and cam1..cam4 (fw_update.c):
   * the P4 writes its own OTA slot and forwards a node's image down its link. */
  cJSON_AddBoolToObject(caps, "xiaoProxyUpdate", true);
  cJSON_AddBoolToObject(caps, "firmwareUpdate", true);
  cJSON_AddBoolToObject(caps, "recipes", kdp_recipes_capable());
  cJSON_AddBoolToObject(caps, "customSounds", kdp_sounds_capable());
  /* benchDiagnostics gates the Milestone 1B group: STORAGE_SELF_TEST,
   * CAMERA_LINK_STATS(_RESET), CAMERA_SOAK_TEST, GET_HW_VALIDATION and
   * STORAGE_BENCH. All six now have handlers - STORAGE_BENCH was the one that
   * did not, and a host trusting this flag got a NACK for it. */
  cJSON_AddBoolToObject(caps, "benchDiagnostics", true);
  /* Settings round-trip and persist as of this build. */
  cJSON_AddBoolToObject(caps, "configStore", true);
  /* Listing, inspecting, deleting and favouriting work. MEDIA_READ and
   * MEDIA_THUMB do not exist yet, so `gallery` stays false: a client that
   * needs pixels cannot get them. */
  cJSON_AddBoolToObject(caps, "mediaIndex", true);
  /* MEDIA_READ and MEDIA_THUMB return bytes now, so a client can actually
   * get pixels off the camera. */
  cJSON_AddBoolToObject(caps, "gallery", true);
  /*
   * One shutter press captures every online camera into one folder. Both modes
   * use the same four sensors and differ in how a host presents frames it
   * already has, so both are true together or not at all.
   *
   * THESE MEAN "the device supports this capture mode", NOT "the mode has been
   * hardware-validated", and the distinction is unresolved in the contract
   * rather than in this firmware.
   *
   * The roadmap (Gate C) suggested gating them behind measured exposure skew,
   * on the reasoning that a host reading `wiggle: true` may reasonably expect
   * usable wigglegrams and this body has never been shown to produce one.
   * That was checked against Studio and rejected: App.tsx and Sidebar.tsx gate
   * NAVIGATION on supports('wiggle'), so reporting false would remove the
   * Wiggle page and make working, configurable settings unreachable — a worse
   * lie than the one it was meant to fix, and a functional regression for a
   * mode the firmware genuinely implements.
   *
   * So they stay true and the ambiguity is recorded here and in
   * firmware-contract/README.md rather than papered over with an invented
   * flag. What a consumer must NOT infer from them is synchronization:
   * `vsyncTelemetry` is false, all three kino.capture skews are null with a
   * reason, and CAMERA_CAPTURE refuses `action: "timing-test"`. Those three
   * are the honest signal and they are unambiguous.
   */
  cJSON_AddBoolToObject(caps, "wiggle", true);
  cJSON_AddBoolToObject(caps, "quad", true);
  /* The control path: the flash window is held across the exposure, the mode
   * is configurable, and the window is bounded and released on every path.
   * True because the command works. BOARD_FLASH_EN is BOARD_GPIO_NONE since
   * ECN-0003 took GPIO28 for the shutter button, so the window drives no pin
   * (capture.c). */
  cJSON_AddBoolToObject(caps, "flashControl", true);
  /*
   * ...and what it drives. Additive and optional, because `flashControl` alone
   * cannot distinguish "the firmware can fire a flash" from "there is a flash
   * to fire", and today only the first is true. FLASH_EN has no P4 pin at all
   * since ECN-0003 (2026-08-30): the built-in flash is out of D4-V1 and the
   * replacement is a separate external module that does not exist yet. A host
   * that shows a flash control because flashControl is true would otherwise be
   * promising the user light that does not exist.
   *
   * Stays false until that module is fitted AND validated (M5, Gate D) - never
   * because a driver was written.
   */
  cJSON_AddBoolToObject(caps, "flashHardware", false);
  /* Idle dim/sleep and camera-bank power-down are implemented; battery
   * telemetry is not, and cannot be until the hardware carries a sense
   * divider or a gauge. Two flags, because a client that wants to show a
   * battery and a client that wants to set a sleep timeout are asking
   * different questions. */
  cJSON_AddBoolToObject(caps, "powerManagement", true);
  cJSON_AddBoolToObject(caps, "powerTelemetry", false);
  /* False on D4-V1 and not because the driver is missing: contract D11 - the
   * backlight is a plain GPIO with no PWM behind it, so body.brightness has
   * nothing to move. Studio reads this to grey its slider out instead of
   * offering a control that does nothing. */
  cJSON_AddBoolToObject(caps, "brightnessControl", false);

  /*
   * Networking and Roll. Four flags rather than two, for the same reason
   * `flashControl` and `flashHardware` are two: "the firmware can" and "the
   * hardware is reachable" are different questions, and one boolean answering
   * both is what produced the old `NETWORK: NOT FITTED` display.
   *
   *   radioFitted  — an ESP32-C6 is on the Guition carrier. It is.
   *   radioRouted  — this firmware has a transport to it. Read from net_link,
   *                  which is what NETWORK_STATUS reads, because the two used
   *                  to disagree: this said false while NETWORK_STATUS said
   *                  true on the same radio build, and Studio consumes this
   *                  one. A registered driver is the route (net_link.h), so
   *                  the default build answers false and the radio build
   *                  answers true without a second constant to keep in step.
   *
   * `network` and `roll` stay FALSE, and that is deliberate even though the
   * whole 0xa0..0xaa surface now has handlers. Studio's supports() gate is
   * fail-closed: setting these true makes Studio render the Roll and Network
   * pages and issue commands that must then refuse, so the user gets a broken
   * panel instead of an absent one. Issue #133 states the rule directly —
   * these gain the flags "only once each command answers for real", and
   * ROLL_CREATE cannot, because it is an HTTP POST to a server this body has
   * no route to.
   *
   * What the handlers being present buys in the meantime is not this flag: it
   * is that a host asking gets a specific NETWORK_UNAVAILABLE naming the radio
   * state, instead of an UNSUPPORTED_COMMAND that cannot distinguish an
   * unimplemented command from an unrouted chip.
   */
  cJSON_AddBoolToObject(caps, "radioFitted", true);
  {
    net_status_t net;
    net_link_status(&net, esp_timer_get_time() / 1000);
    cJSON_AddBoolToObject(caps, "radioRouted", net.radio_routed);
  }
  cJSON_AddBoolToObject(caps, "network", false);
  cJSON_AddBoolToObject(caps, "roll", false);
  /* Not in Studio's Capabilities interface, but it is the flag
   * supportsRollUpload() reads off the raw object, and it gates the Roll page.
   * False until a capture has actually reached a Roll from this body. */
  cJSON_AddBoolToObject(caps, "rollUpload", false);

  cJSON *limits = cJSON_AddObjectToObject(json, "limits");
  /*
   * Both of these were NL_DEFAULT_BAUD, which made the pair meaningless: the
   * maximum was reported as the lowest supported rate, and the current rate
   * was a constant that stopped being true the moment SET_LINK_BAUD ran.
   *
   * The maximum is the largest rate a node accepts. The current rate is what
   * cam1's channel is on - the link is settled all four together, so one
   * channel speaks for the set, and a body with nothing fitted reports the
   * default, which is where an unprobed channel sits.
   */
  {
    static const uint32_t supported[NL_BAUD_SUPPORTED_N] = NL_BAUD_SUPPORTED_LIST;
    uint32_t max_baud = 0;
    for (int i = 0; i < NL_BAUD_SUPPORTED_N; i++) {
      if (supported[i] > max_baud) max_baud = supported[i];
    }
    const uint32_t now = camlink_baud_ch(0);
    cJSON_AddNumberToObject(limits, "maxUartBaud", (double)max_baud);
    cJSON_AddNumberToObject(limits, "currentUartBaud", (double)(now ? now : NL_DEFAULT_BAUD));
  }
  cJSON_AddStringToObject(limits, "maxResolution", "2048x1536");
  cJSON_AddNumberToObject(limits, "maxGalleryPageSize", 100);

  cJSON_AddNumberToObject(json, "configSchemaVersion", 1);
  send_json(KDP_CMD_GET_CAPABILITIES, seq, json);
}

static void handle_device_info(uint32_t seq) {
  storage_status_t sd;
  storage_get_status(&sd);

  cJSON *json = cJSON_CreateObject();
  cJSON_AddStringToObject(json, "product", "KINO");
  cJSON_AddStringToObject(json, "hardware", KDP_HARDWARE_REV);
  cJSON_AddStringToObject(json, "serial", s_id.serial);
  cJSON_AddNumberToObject(json, "protocol", KDP_PROTOCOL_VERSION);
  cJSON_AddStringToObject(json, "p4Firmware", KINO_FW_VERSION);

  /* Every channel answers for itself, as in build_camera_info(): the node's
   * firmware string and sensor name when the sweep has it online, "" when it
   * is offline. This was `i == 0 && cam1.online` with cam2-4 hardcoded "",
   * so a body with four nodes wired reported one node here and four in
   * GET_CAMERA_INFO. */
  cJSON *fw = cJSON_AddArrayToObject(json, "cameraFirmware");
  cJSON *sensors = cJSON_AddArrayToObject(json, "sensors");
  for (int i = 0; i < CAMLINK_CAMS; i++) {
    camlink_info_t info;
    camlink_get_info_ch(i, &info);
    const bool online = info.online;
    cJSON_AddItemToArray(fw, cJSON_CreateString(online ? info.firmware : ""));
    cJSON_AddItemToArray(sensors,
                         cJSON_CreateString(online && info.sensor_detected ? info.sensor : ""));
  }

  cJSON_AddBoolToObject(json, "sdPresent", sd.present);
  cJSON_AddNumberToObject(json, "sdFreeMB", (double)(sd.free_bytes / (1024 * 1024)));
  cJSON_AddStringToObject(json, "activeMode", config_str("mode", "wiggle"));
  cJSON_AddStringToObject(json, "activeRecipe", config_str("wiggle.recipeId", ""));
  send_json(KDP_CMD_GET_DEVICE_INFO, seq, json);
}

static void handle_storage_status(uint32_t seq) {
  storage_status_t sd;
  storage_get_status(&sd);
  cJSON *json = cJSON_CreateObject();
  cJSON_AddBoolToObject(json, "present", sd.present);
  cJSON_AddNumberToObject(json, "totalMB", (double)(sd.capacity_bytes / (1024 * 1024)));
  cJSON_AddNumberToObject(json, "freeMB", (double)(sd.free_bytes / (1024 * 1024)));
  cJSON_AddBoolToObject(json, "mounted", sd.mounted);
  if (sd.filesystem != NULL) cJSON_AddStringToObject(json, "filesystem", sd.filesystem);
  else cJSON_AddNullToObject(json, "filesystem");
  cJSON_AddNumberToObject(json, "capacityBytes", (double)sd.capacity_bytes);
  cJSON_AddNumberToObject(json, "freeBytes", (double)sd.free_bytes);
  if (sd.last_error != NULL) cJSON_AddStringToObject(json, "lastError", sd.last_error);
  else cJSON_AddNullToObject(json, "lastError");
  cJSON_AddNumberToObject(json, "mountAttempts", sd.mount_attempts);
  cJSON_AddStringToObject(json, "writeTestStatus", sd.write_test);
  send_json(KDP_CMD_GET_STORAGE_STATUS, seq, json);
}

/**
 * Power status.
 *
 * The contract's required fields are batteryV and batteryPct, and this build
 * cannot measure either: there is no sense divider to the P4 and no fuel
 * gauge on the SW6106 carrier, so nothing in the camera knows the cell's
 * voltage. They are reported as null rather than as 0, because 0 is a number
 * a client will draw as a flat battery - a wrong reading is worse than an
 * absent one. `powerTelemetry` in GET_CAPABILITIES is false so a client can
 * know before it asks. The deviation is recorded in
 * firmware-contract/README.md.
 *
 * What IS knowable is reported: whether a host is talking to us, and where
 * the idle timeouts have got to.
 */
static void handle_power_status(uint32_t seq) {
  power_state_t p;
  power_get(&p);

  cJSON *json = cJSON_CreateObject();
  cJSON_AddNullToObject(json, "batteryV");
  cJSON_AddNullToObject(json, "batteryPct");
  cJSON_AddBoolToObject(json, "batteryMeasured", false);
  /* No way to tell a charging cell from a discharging one either, so the
   * state reports the only distinction the board supports. */
  cJSON_AddStringToObject(json, "state", p.usb_attached ? "usb" : "battery");
  cJSON_AddBoolToObject(json, "charging", false);

  /* Beyond the contract, and useful: this is the half of power management
   * that does work. */
  cJSON_AddStringToObject(json, "displayStage",
                          p.stage == POWER_AWAKE  ? "awake"
                          : p.stage == POWER_DIM ? "dim"
                                                 : "asleep");
  cJSON_AddNumberToObject(json, "idleSeconds", p.idle_s);
  cJSON_AddBoolToObject(json, "displayOn", p.display_on);
  cJSON_AddBoolToObject(json, "cameraBankPowered", p.cam_bank_on);
  send_json(KDP_CMD_GET_POWER_STATUS, seq, json);
}

/* The envelope, minus anything that is write-only. */
static cJSON *config_envelope(void) {
  cJSON *json = cJSON_CreateObject();
  cJSON_AddNumberToObject(json, "schemaVersion", 1);
  cJSON_AddStringToObject(json, "device", s_id.device_id);
  cJSON_AddNumberToObject(json, "configRevision", config_revision());

  cJSON *copy = cJSON_Duplicate(config_get(), true);
  if (copy != NULL) {
    /* deviceToken is write-only by contract: it may be set, never read back,
     * and never lands in a Studio backup. What is safe to report is whether
     * one exists. */
    cJSON *roll = cJSON_GetObjectItem(copy, "roll");
    cJSON *creds = roll ? cJSON_GetObjectItem(roll, "credentials") : NULL;
    if (creds != NULL) {
      /* Since 0.4.23 the token lives in roll_state, never in this document
       * (the document keeps a blank deviceToken so its shape is stable), so
       * the store is what answers "is there one". */
      cJSON_DeleteItemFromObject(creds, "deviceToken");
      cJSON_AddBoolToObject(creds, "hasDeviceToken", roll_state_has_credential());
    }
    cJSON_AddItemToObject(json, "config", copy);
  }
  return json;
}

/**
 * What every image on this body is running.
 *
 * The versions are read here; the update itself is FW_BEGIN..FW_STATUS below
 * (fw_update.c), now that both the P4 and the nodes carry two OTA slots.
 * `state` is live: a target mid-update says so.
 *
 * It exists now because the D4 gained a sixth image. Issue #133 requires the
 * C6 slave version to be reportable alongside the P4 and the nodes: a C6
 * running a stale hosted image is a second thing that can be out of date in
 * the field, and a version model that cannot name it cannot diagnose it.
 *
 * An empty `version` means "could not read one", never version zero — a node
 * that has never answered, or a C6 with no transport to it. `state` describes
 * an update in progress, so an unreachable target is `idle`: nothing failed,
 * nothing was attempted. Reporting `error` there would send someone to
 * re-flash a chip that is merely unwired.
 */
static void handle_fw_query(uint32_t seq) {
  cJSON *json = cJSON_CreateObject();
  cJSON *targets = cJSON_AddObjectToObject(json, "targets");

  cJSON *p4 = cJSON_AddObjectToObject(targets, "p4");
  cJSON_AddStringToObject(p4, "version", KINO_FW_VERSION);
  cJSON_AddStringToObject(p4, "state", fw_update_state(FW_T_P4));

  for (int cam = 1; cam <= 4; cam++) {
    camlink_info_t info;
    /* Channels are 0-based and this loop is 1-based for the key; it passed
     * `cam` straight through and reported cam2's node as cam1's. */
    camlink_get_info_ch(cam - 1, &info);
    char key[8];
    snprintf(key, sizeof key, "cam%d", cam);
    cJSON *t = cJSON_AddObjectToObject(targets, key);
    /* A node that has never answered reports "", not a guess. No camera node
     * has ever been connected to a P4 (HARDWARE_VALIDATION.md), so this is
     * the ordinary case rather than the exceptional one. */
    cJSON_AddStringToObject(t, "version", info.online ? info.firmware : "");
    cJSON_AddStringToObject(t, "state", fw_update_state((fw_target_t)(FW_T_CAM1 + cam - 1)));
  }

  net_status_t net;
  net_link_status(&net, esp_timer_get_time() / 1000);
  cJSON *c6 = cJSON_AddObjectToObject(targets, "c6");
  cJSON_AddStringToObject(c6, "version", net.c6_version);
  cJSON_AddStringToObject(c6, "state", "idle");
  /* Additive, and the field that makes the empty version above readable: the
   * chip is fitted and this firmware has no route to it, which is neither
   * "absent" nor "broken". Without this a host sees an empty version and
   * cannot tell which. */
  cJSON_AddBoolToObject(c6, "fitted", net.radio_fitted);
  cJSON_AddBoolToObject(c6, "reachable", net.radio_routed);

  send_json(KDP_CMD_FW_QUERY, seq, json);
}

/*
 * The update path (contract FW_* 0x61..0x65; fw_update.c does the work).
 *
 * FW_BEGIN names the target, the size and the SHA-256; FW_CHUNK carries an
 * 8-byte little-endian header - sessionId, offset - then data; FW_END
 * verifies and applies. Studio's updater (apps/studio/src/firmware/updater.ts)
 * is the client this matches: it expects the P4 to answer FW_END and then
 * drop the link as it restarts, and it polls FW_STATUS for a camera target
 * until "ready".
 */
static void handle_fw_begin(uint32_t seq, cJSON *req) {
  const cJSON *target = cJSON_GetObjectItem(req, "target");
  const cJSON *size = cJSON_GetObjectItem(req, "size");
  const cJSON *sha = cJSON_GetObjectItem(req, "sha256");
  const cJSON *version = cJSON_GetObjectItem(req, "version");
  fw_target_t t;
  if (!cJSON_IsString(target) || !fw_update_target_parse(target->valuestring, &t)) {
    send_nack(KDP_CMD_FW_BEGIN, seq, "INVALID_ARGUMENT", "target must be p4 or cam1..cam4");
    return;
  }
  if (!cJSON_IsNumber(size) || size->valuedouble < 0 || size->valuedouble > 4294967295.0) {
    send_nack(KDP_CMD_FW_BEGIN, seq, "BAD_SIZE", "size must be a byte count");
    return;
  }
  uint32_t sid = 0, chunk = 0;
  fw_refusal_t why = {"ERROR", "Update could not start"};
  const esp_err_t err = fw_update_begin(t, (uint32_t)size->valuedouble,
                                        cJSON_IsString(sha) ? sha->valuestring : NULL,
                                        cJSON_IsString(version) ? version->valuestring : "", &sid,
                                        &chunk, &why);
  if (err != ESP_OK) {
    send_nack(KDP_CMD_FW_BEGIN, seq, why.code, why.message);
    return;
  }
  cJSON *json = cJSON_CreateObject();
  cJSON_AddNumberToObject(json, "sessionId", (double)sid);
  cJSON_AddNumberToObject(json, "chunkSize", (double)chunk);
  send_json(KDP_CMD_FW_BEGIN, seq, json);
}

static void handle_fw_chunk(uint32_t seq, const uint8_t *payload, uint32_t len) {
  if (payload == NULL || len < 9) {
    send_nack(KDP_CMD_FW_CHUNK, seq, "INVALID_ARGUMENT",
              "A chunk is an 8-byte sessionId/offset header and data");
    return;
  }
  const uint32_t sid = (uint32_t)payload[0] | ((uint32_t)payload[1] << 8) |
                       ((uint32_t)payload[2] << 16) | ((uint32_t)payload[3] << 24);
  const uint32_t offset = (uint32_t)payload[4] | ((uint32_t)payload[5] << 8) |
                          ((uint32_t)payload[6] << 16) | ((uint32_t)payload[7] << 24);
  fw_refusal_t why = {"ERROR", "Chunk refused"};
  const esp_err_t err = fw_update_chunk(sid, offset, payload + 8, len - 8, &why);
  if (err != ESP_OK) {
    send_nack(KDP_CMD_FW_CHUNK, seq, why.code, why.message);
    return;
  }
  cJSON *json = cJSON_CreateObject();
  cJSON_AddBoolToObject(json, "ok", true);
  cJSON_AddNumberToObject(json, "received", (double)(len - 8));
  send_json(KDP_CMD_FW_CHUNK, seq, json);
}

static void handle_fw_end(uint32_t seq) {
  bool verified = false;
  fw_refusal_t why = {"ERROR", "Update could not finish"};
  const esp_err_t err = fw_update_end(&verified, &why);
  if (err != ESP_OK) {
    send_nack(KDP_CMD_FW_END, seq, why.code, why.message);
    return;
  }
  cJSON *json = cJSON_CreateObject();
  cJSON_AddBoolToObject(json, "ok", true);
  cJSON_AddBoolToObject(json, "verified", verified);
  send_json(KDP_CMD_FW_END, seq, json);
}

static void handle_fw_abort(uint32_t seq) {
  fw_update_abort();
  cJSON *json = cJSON_CreateObject();
  cJSON_AddBoolToObject(json, "ok", true);
  send_json(KDP_CMD_FW_ABORT, seq, json);
}

static void handle_fw_status(uint32_t seq, cJSON *req) {
  const cJSON *target = cJSON_GetObjectItem(req, "target");
  fw_target_t t = FW_T_P4;
  if (cJSON_IsString(target) && !fw_update_target_parse(target->valuestring, &t)) {
    send_nack(KDP_CMD_FW_STATUS, seq, "INVALID_ARGUMENT", "target must be p4 or cam1..cam4");
    return;
  }
  cJSON *json = cJSON_CreateObject();
  cJSON_AddStringToObject(json, "target", fw_update_target_name(t));
  cJSON_AddStringToObject(json, "state", fw_update_state(t));
  if (t == FW_T_P4) {
    cJSON_AddStringToObject(json, "version", KINO_FW_VERSION);
  } else {
    camlink_info_t info;
    camlink_get_info_ch((int)t - FW_T_CAM1, &info);
    cJSON_AddStringToObject(json, "version", info.online ? info.firmware : "");
  }
  const char *error = fw_update_error(t);
  if (error[0] != '\0') cJSON_AddStringToObject(json, "error", error);
  send_json(KDP_CMD_FW_STATUS, seq, json);
}

static void handle_get_config(uint32_t seq) {
  send_json(KDP_CMD_GET_CONFIG, seq, config_envelope());
}

/**
 * Merge a patch into the live config.
 *
 * A merge, not a replace: Studio sends the branch it changed, and replacing
 * would make writing one field clear every other. Not persisted here -
 * SAVE_CONFIG does that, which is what lets a client try a setting and walk
 * away without it surviving a power cycle.
 */
static void handle_set_config(uint32_t seq, const cJSON *req) {
  const cJSON *patch = cJSON_GetObjectItem(req, "config");
  if (!cJSON_IsObject(patch)) patch = req; /* a bare config object is fine too */
  if (!cJSON_IsObject(patch)) {
    send_nack(KDP_CMD_SET_CONFIG, seq, "BAD_REQUEST", "Expected a config object");
    return;
  }
  /*
   * body.name is 0..24 characters, and that limit is enforced here because
   * this is the only place it is ever written - config_merge() takes whatever
   * document it is handed by design.
   *
   * Refused rather than truncated. A camera that silently shortens the name
   * someone just typed shows a different name from the one that was saved and
   * gives the host nothing to explain it with; a NACK naming the limit is a
   * thing Studio can put next to the field.
   */
  const cJSON *body = cJSON_GetObjectItem(patch, "body");
  const cJSON *name = body ? cJSON_GetObjectItem(body, "name") : NULL;
  if (name != NULL &&
      (!cJSON_IsString(name) || name->valuestring == NULL || strlen(name->valuestring) > 24)) {
    send_nack(KDP_CMD_SET_CONFIG, seq, "BAD_REQUEST",
              "body.name is a string of at most 24 characters");
    return;
  }
  /*
   * roll.credentials.deviceToken is write-only and never lands in the config
   * document. Studio provisions through this command (rollOps.ts
   * registerRollDevice -> applyConfig), and until 0.4.23 the pair was merged
   * into config where nothing read it - roll_http takes its bearer token from
   * roll_state's record, which only the dev-only self-registration wrote - so
   * a Studio-provisioned camera reported hasDeviceToken true and tokenStatus
   * no-credential side by side (bench 2026-09-02, KD4-D121BC after an NVS
   * wipe). The pair goes to roll_state here; the copy that is merged and saved
   * carries a blank token.
   */
  cJSON *scrubbed = cJSON_Duplicate(patch, true);
  if (scrubbed == NULL) {
    send_nack(KDP_CMD_SET_CONFIG, seq, "OUT_OF_MEMORY", "No memory to apply the config");
    return;
  }
  char cred_id[ROLL_DEVICE_ID_LEN];
  char cred_tok[ROLL_DEVICE_TOKEN_LEN];
  const meta_credential_t cred =
      meta_take_roll_credential(scrubbed, cred_id, sizeof cred_id, cred_tok, sizeof cred_tok);
  if (cred == META_CRED_INVALID) {
    cJSON_Delete(scrubbed);
    send_nack(KDP_CMD_SET_CONFIG, seq, "BAD_REQUEST",
              "roll.credentials needs a deviceId and a deviceToken that fits");
    return;
  }
  if (cred == META_CRED_OK) {
    const esp_err_t cerr = roll_state_set_credential(cred_id, cred_tok);
    memset(cred_tok, 0, sizeof cred_tok);
    if (cerr != ESP_OK) {
      cJSON_Delete(scrubbed);
      send_nack(KDP_CMD_SET_CONFIG, seq, "STORAGE_ERROR", "The device credential would not store");
      return;
    }
    klog("P4", "device credential stored for %s", cred_id);
  }
  const esp_err_t merr = config_merge(scrubbed);
  cJSON_Delete(scrubbed);
  if (merr != ESP_OK) {
    send_nack(KDP_CMD_SET_CONFIG, seq, "BAD_REQUEST", "Config could not be merged");
    return;
  }
  /* Studio can turn these on and off without a reflash. */
  klog_set_telemetry(config_bool("body.log.telemetry", false));
  lid_set_acting(config_bool("body.coverWatch", false));
  klog("P4", "config set rev %lu", (unsigned long)config_revision());
  send_json(KDP_CMD_SET_CONFIG, seq, config_envelope());
}

void kdp_server_import_roll_credential(void) {
  /* A token a firmware up to 0.4.22 saved into the config document on Studio's
   * behalf. Moved into roll_state once, then blanked and the document saved,
   * so the secret leaves the NVS config envelope. Runs after roll_state_init. */
  cJSON *copy = cJSON_Duplicate(config_get(), true);
  if (copy == NULL) return;
  char id[ROLL_DEVICE_ID_LEN];
  char tok[ROLL_DEVICE_TOKEN_LEN];
  const meta_credential_t cred = meta_take_roll_credential(copy, id, sizeof id, tok, sizeof tok);
  cJSON_Delete(copy);
  if (cred == META_CRED_NONE) return;
  if (cred == META_CRED_OK && !roll_state_has_credential()) {
    if (roll_state_set_credential(id, tok) == ESP_OK) {
      klog("P4", "device credential imported from config for %s", id);
    }
  }
  memset(tok, 0, sizeof tok);
  /* Blanked whatever happened above: a token the store refused is still a
   * secret in the wrong place. */
  cJSON *blank = cJSON_Parse("{\"roll\":{\"credentials\":{\"deviceToken\":\"\"}}}");
  if (blank != NULL) {
    if (config_merge(blank) == ESP_OK) (void)config_save();
    cJSON_Delete(blank);
  }
}

static void handle_save_config(uint32_t seq) {
  const esp_err_t err = config_save();
  if (err == ESP_ERR_INVALID_SIZE) {
    /* The merged document no longer fits nvs_set_str's 4000-byte ceiling
     * (config_store.h). The merge is already live in RAM, so the host must
     * hear that it will not survive a reboot rather than a generic failure. */
    send_nack(KDP_CMD_SAVE_CONFIG, seq, "STORAGE_ERROR",
              "config document exceeds the 4000-byte NVS limit; not persisted");
    return;
  }
  if (err != ESP_OK) {
    send_nack(KDP_CMD_SAVE_CONFIG, seq, "STORAGE_ERROR", "NVS write failed");
    return;
  }
  send_json(KDP_CMD_SAVE_CONFIG, seq, config_envelope());
}

static void handle_reset_config(uint32_t seq) {
  if (config_reset() != ESP_OK) {
    send_nack(KDP_CMD_RESET_CONFIG, seq, "STORAGE_ERROR", "NVS write failed");
    return;
  }
  send_json(KDP_CMD_RESET_CONFIG, seq, config_envelope());
}

bool kdp_p4_temp_c(float *out) {
  float c = 0.0f;
  if (s_tsens == NULL || temperature_sensor_get_celsius(s_tsens, &c) != ESP_OK) return false;
  if (out != NULL) *out = c;
  return true;
}

/**
 * The shooting modes this body knows about, and which is selected.
 *
 * `available` and `unavailableReason` were CONSTANTS: false, and "No capture
 * pipeline in this build". True in Milestone 1B, untrue since capture landed in
 * 0.3.0, and never revisited. On KD4-D121BC running 0.4.17 this handler said
 * wiggle and quad were both unavailable for want of a capture pipeline, and
 * eleven cases later in the same conformance run CAMERA_CAPTURE stored
 * CAP_000629 - one frame, complete, 2980 ms. Every host that asked the camera
 * what it could do was told it could not shoot.
 *
 * The predicate now comes from capture_fire()'s own gates, in its own order,
 * and lives in capture_unavailable_reason() (pure.c, host-tested) with the
 * reasoning and the rejected stricter reading of `quad`. Both modes get the
 * same answer because capture.c never consults the mode when deciding whether
 * it may shoot - availability is a property of the body, not of the mode - and
 * that is stated where it can be checked rather than assumed here.
 *
 * `active` still comes from the config and is still meaningful when the mode is
 * unavailable: it is a stored selection that survives a reboot and is what the
 * camera will shoot the moment a card and a camera are there. A host reading
 * both fields gets a coherent pair - "active: wiggle, wiggle unavailable
 * because no camera node answered" - and cannot get the incoherent one, an
 * active mode that is unavailable while the other is not, because the two
 * always agree.
 */
static void handle_get_modes(uint32_t seq) {
  static const struct {
    const char *id;
    const char *name;
  } MODES[] = {{"wiggle", "Wiggle"}, {"quad", "Quad"}};

  /* A card that is mounted, and one camera that is both online and has a worker
   * behind it - the same conjunction capture_fire() builds its `ask` mask from,
   * so a mode reported available is a mode the shutter will accept. */
  storage_status_t sd;
  storage_get_status(&sd);
  const uint32_t ready = capture_ready_cams();
  bool any_camera_ready = false;
  for (int i = 0; i < CAPTURE_CAMS; i++) {
    camlink_info_t ci;
    camlink_get_info_ch(i, &ci);
    if (ci.online && (ready & (1u << i)) != 0) {
      any_camera_ready = true;
      break;
    }
  }
  const char *why = capture_unavailable_reason(sd.mounted, any_camera_ready);

  cJSON *json = cJSON_CreateObject();
  cJSON_AddStringToObject(json, "active", config_str("mode", "wiggle"));
  cJSON *arr = cJSON_AddArrayToObject(json, "modes");
  for (size_t i = 0; i < sizeof MODES / sizeof MODES[0]; i++) {
    cJSON *m = cJSON_CreateObject();
    cJSON_AddStringToObject(m, "id", MODES[i].id);
    cJSON_AddStringToObject(m, "name", MODES[i].name);
    cJSON_AddBoolToObject(m, "available", why == NULL);
    /* The field stays present either way, null when there is nothing to
     * explain - the shape this file uses everywhere for an absent value, and
     * kinder to a host than a field that comes and goes. */
    if (why != NULL) cJSON_AddStringToObject(m, "unavailableReason", why);
    else cJSON_AddNullToObject(m, "unavailableReason");
    cJSON_AddItemToArray(arr, m);
  }
  send_json(KDP_CMD_GET_MODES, seq, json);
}

static void handle_set_mode(uint32_t seq, const cJSON *req) {
  const cJSON *mode = cJSON_GetObjectItem(req, "mode");
  if (!cJSON_IsString(mode) || mode->valuestring == NULL) {
    send_nack(KDP_CMD_SET_MODE, seq, "BAD_REQUEST", "Expected {\"mode\":\"wiggle\"|\"quad\"}");
    return;
  }
  if (strcmp(mode->valuestring, "wiggle") != 0 && strcmp(mode->valuestring, "quad") != 0) {
    send_nack(KDP_CMD_SET_MODE, seq, "BAD_REQUEST", "Unknown mode");
    return;
  }
  cJSON *patch = cJSON_CreateObject();
  cJSON_AddStringToObject(patch, "mode", mode->valuestring);
  const esp_err_t err = config_merge(patch);
  cJSON_Delete(patch);
  if (err != ESP_OK) {
    send_nack(KDP_CMD_SET_MODE, seq, "BAD_REQUEST", "Mode could not be stored");
    return;
  }
  klog("P4", "mode %s", mode->valuestring);
  cJSON *json = cJSON_CreateObject();
  cJSON_AddStringToObject(json, "active", config_str("mode", "wiggle"));
  cJSON_AddNumberToObject(json, "configRevision", config_revision());
  send_json(KDP_CMD_SET_MODE, seq, json);
}

/* ------------------------------------------------------------------ */
/* Media                                                               */
/*                                                                     */
/* Captures live at /sdcard/KINO/CAPTURES/<uuid>/ with C1.JPG and       */
/* META.JSON inside, which storage.c already writes. The card is the    */
/* only index there is - no database is kept, deliberately: a card      */
/* pulled and edited on a laptop is a normal thing to do to a camera,   */
/* and an index would then be a lie that survives reboots.              */
/* ------------------------------------------------------------------ */

#define CAPTURES_DIR "/sdcard/KINO/CAPTURES"
#define MEDIA_MAX_LIST 512

/* Must match gallery.c's MAX_SCAN: it is the same index being read, and a
 * reader that sized its buffer smaller would truncate the file and under-count
 * the card - the failure this whole change exists to remove. */
#define MEDIA_INDEX_MAX 4096

/* Directory names, sorted, so paging is stable between calls. A capture id
 * sorts lexicographically the same way it sorts by time because the sequence
 * is zero-padded, so this is also newest-last. */
/*
 * When a capture was taken, straight out of its META.JSON.
 *
 * The obvious key is the directory mtime, and it does not work here: stat()
 * on both the folder and its META.JSON came back with times that sorted every
 * capture equal, so the list stayed in readdir order - which for UUID names is
 * meaningless. capturedAtMs is written by the capture itself and is visibly
 * correct in MEDIA_LIST output, so it is the key that actually orders.
 *
 * Read with a bounded fread and a strstr rather than a cJSON parse: this runs
 * once per capture on the card just to sort them, and the page a client
 * actually receives still gets a full parse. 512 bytes covers it - the key
 * sits in the first hundred or so of every META.JSON this firmware writes.
 */
static char s_taken_path[200];
static char s_taken_head[512];

static uint64_t capture_taken_ms(const char *dir_name) {
  /* .bss, same reason as media_meta above: one command at a time on one task. */
  char *const path = s_taken_path;
  snprintf(path, sizeof s_taken_path, "%s/%s/META.JSON", CAPTURES_DIR, dir_name);
  FILE *f = fopen(path, "rb");
  if (f == NULL) return 0;
  char *const head = s_taken_head;
  const size_t got = fread(head, 1, sizeof s_taken_head - 1, f);
  fclose(f);
  head[got] = '\0';
  const char *k = strstr(head, "\"capturedAtMs\"");
  if (k == NULL) return 0;
  k = strchr(k, ':');
  if (k == NULL) return 0;
  return strtoull(k + 1, NULL, 10);
}

/**
 * Fill `names` with the newest `cap` capture directories, newest first.
 *
 * Returns how many rows were written; `*on_card` gets how many capture
 * directories the walk actually saw, which is the larger number past
 * MEDIA_MAX_LIST. The caller needs both and they are not the same figure:
 * MEDIA_LIST reports the walked count as `total` and pages over the returned
 * rows. Returning only the row count made `total` the page bound, so a card
 * holding 700 captures reported 512 and a client that trusted `total` stopped
 * asking there.
 */
static int media_scan(char (*names)[64], int cap, int *on_card) {
  *on_card = 0;
  DIR *d = opendir(CAPTURES_DIR);
  if (d == NULL) return 0;
  /*
   * Timestamps collected during the walk, not after it, so a full card can
   * evict its oldest instead of dropping whatever readdir happened to hand
   * over last. This used to stop dead at `cap`, which meant that past
   * MEDIA_MAX_LIST captures the NEWEST could be the ones omitted - the exact
   * failure the sort was added to fix. gallery.c solved the same problem the
   * same way.
   */
  uint64_t *when = calloc((size_t)cap, sizeof *when);
  int count = 0;
  int total = 0;
  struct dirent *e;
  while ((e = readdir(d)) != NULL) {
    if (e->d_name[0] == '.') continue;
    /* The gallery's order index lives in this directory, so readdir hands it
     * back here too. Listed as a capture it would make MEDIA_LIST report one
     * more photograph than the card holds, and MEDIA_INFO on it would answer
     * with an empty summary. */
    if (gidx_is_index_file(e->d_name)) continue;
    /* Anything that will not fit is not one of ours: capture directories are
     * UUID-shaped and well under this. Skipping is better than truncating,
     * which would produce an id that maps to no directory. */
    const size_t len = strlen(e->d_name);
    if (len == 0 || len >= 64) continue;
    /*
     * TODO(#media-count): `total` counts every entry readdir returns, so a
     * card carrying stray folders or interrupted commits reports more
     * photographs than it holds - 1325 measured on the bench card. The
     * eligibility rule belongs here, but adding a stat() per entry to a walk
     * that already opens META.JSON per entry pushed this command from 83 s to
     * over 150 s and it timed out. MEDIA_LIST needs the gallery's persisted
     * order index (gallery_index.h) instead of re-reading the card, and that
     * is the change this figure waits on. The UI's Photos row and Delete All
     * no longer depend on it - they use storage_media_count().
     */
    total++;

    if (count < cap) {
      memcpy(names[count], e->d_name, len + 1);
      if (when != NULL) when[count] = capture_taken_ms(e->d_name);
      count++;
      continue;
    }
    if (when == NULL) continue; /* no timestamps: keep the first `cap`, as before */

    const uint64_t taken = capture_taken_ms(e->d_name);
    int oldest = 0;
    for (int i = 1; i < cap; i++) {
      if (when[i] < when[oldest]) oldest = i;
    }
    if (taken > when[oldest]) {
      memcpy(names[oldest], e->d_name, len + 1);
      when[oldest] = taken;
    }
  }
  closedir(d);

  /*
   * Newest first, by directory mtime.
   *
   * This sorted by strcmp on the folder name, and the names are UUIDs, so the
   * list came back alphabetical: 007f5d03, 049c0c3e, 05089a35. A client asking
   * for the first page got the oldest pictures on the card, and a shot just
   * taken could be a hundred entries down. Sorting by name is stable and
   * meaningless; a gallery wants the last thing photographed at the top.
   *
   * capturedAtMs from each META.JSON, read with a bounded fread rather than a
   * full parse. Directory mtime was tried first and sorted everything equal.
   */

  /* Insertion sort: a card holds hundreds of captures, not millions, and this
   * avoids dragging qsort's comparator indirection in for it. Falls back to
   * name order if the mtime allocation failed - a wrong order beats no list. */
  for (int i = 1; i < count; i++) {
    char key[64];
    memcpy(key, names[i], 64);
    const uint64_t key_when = when != NULL ? when[i] : 0;
    int j = i - 1;
    /* memcpy, not snprintf: the source and destination are rows of the same
     * array, and snprintf is not defined for overlapping objects. */
    while (j >= 0 && (when != NULL ? when[j] < key_when : strcmp(names[j], key) > 0)) {
      memcpy(names[j + 1], names[j], 64);
      if (when != NULL) when[j + 1] = when[j];
      j--;
    }
    memcpy(names[j + 1], key, 64);
    if (when != NULL) when[j + 1] = key_when;
  }
  free(when);
  if (total > count) {
    klog("P4", "media list: %d captures on the card, returning the newest %d", total, count);
  }
  *on_card = total;
  return count;
}

/* Read <dir>/META.JSON. Returns NULL when absent or unparseable - a capture
 * whose metadata is gone is still listed, just with less to say about it. */
/*
 * Scratch in .bss, not on the stack.
 *
 * 160 + 1024 bytes of locals sat on the deepest branch this task has:
 * handle_media_list -> media_summary -> media_meta -> cJSON_Parse, once per
 * item for up to 100 items, with the fopen chain and cJSON's recursion on top
 * - about 3.4 KB of the 8192 this task gets. That is the same shape as the
 * frame that just overflowed the UI task's 8192 opening the gallery, so it is
 * moved for the same reason, before it becomes the same bug.
 *
 * Safe as file statics because the KDP server dispatches one command at a
 * time on one task, and nothing outside this file calls these.
 */
static char s_meta_path[160];
/*
 * 4 KB, not 1 KB, and it is the third time this project has been bitten by a
 * fixed buffer smaller than a four-camera META.JSON.
 *
 * A four-camera document measured 2301 B on the bench card (three cameras is
 * 1916 B). At 1024 the fread returned a truncated object, cJSON refused it,
 * media_meta() answered NULL, and every four-camera capture listed as
 * `status: unknown, frameCount: 0, capturedAt: ""` - a gallery of blanks over
 * photographs that are perfectly intact on the card. #168 was the same
 * mistake in the Roll-provenance reader at 2048 B, and upload_store.c's
 * META_READ_MAX is the 4096 both frame-list and roll-id readers now share.
 *
 * Kept in .bss with the path for the reason below; 4 KB is affordable there
 * and would not be on this task's 8 KB stack.
 */
#define MEDIA_META_MAX 4096
static char s_meta_buf[MEDIA_META_MAX];

static cJSON *media_meta(const char *id) {
  char *const path = s_meta_path;
  char *const buf = s_meta_buf;
  snprintf(path, sizeof s_meta_path, "%s/%s/META.JSON", CAPTURES_DIR, id);
  FILE *f = fopen(path, "rb");
  if (f == NULL) return NULL;
  const size_t got = fread(buf, 1, sizeof s_meta_buf - 1, f);
  fclose(f);
  buf[got] = '\0';
  /* Off the card, so not ours to trust: see pure_json_depth_ok. */
  if (!pure_json_depth_ok(buf, PURE_JSON_MAX_DEPTH)) return NULL;
  return cJSON_Parse(buf);
}

static long media_file_size(const char *id, const char *name) {
  char path[160];
  snprintf(path, sizeof path, "%s/%s/%s", CAPTURES_DIR, id, name);
  struct stat st;
  if (stat(path, &st) != 0) return -1;
  return (long)st.st_size;
}

/* One CaptureSummary. Fields the metadata does not carry are reported as the
 * contract's own neutral values rather than guessed at. */
static cJSON *media_summary(const char *id) {
  cJSON *meta = media_meta(id);
  cJSON *item = cJSON_CreateObject();
  cJSON_AddStringToObject(item, "id", id);

  /* The META.JSON -> CaptureSummary mapping lives in meta.c so it can be
   * host-tested. This read keys the document never contained and reported
   * every capture as a wiggle at the epoch; the tests in
   * firmware/p4/host_tests now pin it. */
  meta_capture_summary(meta, item);

  long total = 0;
  static const char *FILES[4] = {"C1.JPG", "C2.JPG", "C3.JPG", "C4.JPG"};
  for (int i = 0; i < 4; i++) {
    const long sz = media_file_size(id, FILES[i]);
    if (sz > 0) total += sz;
  }
  cJSON_AddNumberToObject(item, "totalKB", (double)(total / 1024));

  if (meta) cJSON_Delete(meta);
  return item;
}

/*
 * Which files inside a capture folder a host may ask for.
 *
 * An allow-list, not a sanitiser. media_id_ok() has already pinned the id to
 * a UUID, but the file name is attacker-chosen too and "..\\" or a device
 * name on a FAT volume would walk out of the folder just as effectively.
 *
 * The names are STORAGE_CAPTURE_FILES, the same array storage.c deletes a
 * capture with. There used to be a second copy here, and a seventh file added
 * to a capture would have been written by one list and unreachable through
 * the other.
 */
static bool media_file_allowed(const char *name) {
  for (int i = 0; i < STORAGE_CAPTURE_FILE_COUNT; i++) {
    if (strcmp(name, STORAGE_CAPTURE_FILES[i]) == 0) return true;
  }
  /* The upload record beside the capture. Readable so a bench can back up and
   * audit the queue over KDP before touching it; it is not a capture file, so
   * it stays out of STORAGE_CAPTURE_FILES and out of the delete path. */
  return strcmp(name, UPLOAD_STORE_RECORD) == 0;
}

/*
 * Whether a host-supplied capture id may be pasted into a path.
 *
 * Every MEDIA_* handler builds "/sdcard/KINO/CAPTURES/<id>/..." from this
 * string. MEDIA_INFO, MEDIA_DELETE and MEDIA_FAVORITE only rejected '/', so
 * {"id":".."} named the CAPTURES directory itself and MEDIA_DELETE walked it:
 * storage_capture_delete() unlinked C1..C4.JPG and META.JSON out of the
 * parent of every capture on the card.
 *
 * So all six ask the same question, and it is the strict one the orphan sweep
 * already uses: a v4 UUID, exactly the shape storage.c writes. ".." fails it
 * on the first character. pure.c is host-tested (test_pure.c) precisely so
 * this check has a test that runs on every build.
 */
static bool media_id_ok(const char *id) { return id != NULL && pure_is_capture_dirname(id); }

/* One response carries at most this much file. KDP_MAX_PAYLOAD is 16 KB and
 * the frame's own header and CRC have to fit alongside it. */
#define MEDIA_READ_MAX 8192

/* Upper bound for a read offset. fseek() takes a long, which is 32-bit here,
 * and FAT32 caps a file at 4 GB anyway; 2^31-1 is exactly representable as a
 * double, so clamping to it cannot round past LONG_MAX on the way back. */
#define MEDIA_OFFSET_MAX 2147483647.0

/**
 * Stream bytes out of one file in a capture.
 *
 * The reply is raw file bytes with KDP_FLAG_BINARY set - no JSON envelope,
 * because a 300 KB JPEG through base64 would cost a third again in transfer
 * for nothing. The caller asked for an offset and a length, so it already
 * knows what it is looking at; a short reply means end of file. Errors come
 * back as JSON with the ERROR flag, so the two are never ambiguous.
 */
static void handle_media_read(uint32_t seq, const cJSON *req) {
  const cJSON *jid = cJSON_GetObjectItem(req, "id");
  const cJSON *jfile = cJSON_GetObjectItem(req, "file");
  if (!cJSON_IsString(jid) || !media_id_ok(jid->valuestring)) {
    send_nack(KDP_CMD_MEDIA_READ, seq, "BAD_REQUEST", "Expected a capture id");
    return;
  }
  const char *file = (cJSON_IsString(jfile) && jfile->valuestring) ? jfile->valuestring : "C1.JPG";
  if (!media_file_allowed(file)) {
    send_nack(KDP_CMD_MEDIA_READ, seq, "BAD_REQUEST", "Not a file a capture contains");
    return;
  }

  const cJSON *joff = cJSON_GetObjectItem(req, "offset");
  const cJSON *jlen = cJSON_GetObjectItem(req, "length");
  const long offset = clamp_num(joff, 0, MEDIA_OFFSET_MAX, 0);
  const long length = clamp_num(jlen, 1, MEDIA_READ_MAX, MEDIA_READ_MAX);

  char path[200];
  snprintf(path, sizeof path, "%s/%s/%s", CAPTURES_DIR, jid->valuestring, file);
  FILE *f = fopen(path, "rb");
  if (f == NULL) {
    send_nack(KDP_CMD_MEDIA_READ, seq, "NOT_FOUND", "No such capture file");
    return;
  }
  if (fseek(f, offset, SEEK_SET) != 0) {
    fclose(f);
    send_nack(KDP_CMD_MEDIA_READ, seq, "BAD_REQUEST", "Offset is past the end of the file");
    return;
  }
  uint8_t *buf = malloc((size_t)length);
  if (buf == NULL) {
    fclose(f);
    send_nack(KDP_CMD_MEDIA_READ, seq, "BUSY", "Out of memory");
    return;
  }
  const size_t got = fread(buf, 1, (size_t)length, f);
  fclose(f);
  /* The bytes are in RAM; the card is not needed to put them on the wire, and
   * the wire can take 3.5 s. See media_card_done(). */
  media_card_done();
  /* A zero-length reply is the honest answer for a read that starts exactly
   * at the end of the file, and is how a client knows it has everything. */
  send_raw(KDP_CMD_MEDIA_READ, KDP_FLAG_RESPONSE | KDP_FLAG_BINARY, seq, buf, got);
  free(buf);
}

/* THUMB.JPG is written at capture time, so this is a read with a fixed name
 * rather than a decode-and-scale on demand. A capture taken by firmware older
 * than this one has no thumbnail and says so instead of inventing one. */
static void handle_media_thumb(uint32_t seq, const cJSON *req) {
  const cJSON *jid = cJSON_GetObjectItem(req, "id");
  if (!cJSON_IsString(jid) || !media_id_ok(jid->valuestring)) {
    send_nack(KDP_CMD_MEDIA_THUMB, seq, "BAD_REQUEST", "Expected a capture id");
    return;
  }
  char path[200];
  snprintf(path, sizeof path, "%s/%s/THUMB.JPG", CAPTURES_DIR, jid->valuestring);
  FILE *f = fopen(path, "rb");
  if (f == NULL) {
    send_nack(KDP_CMD_MEDIA_THUMB, seq, "NOT_FOUND",
              "This capture has no thumbnail; read C1.JPG instead");
    return;
  }
  const cJSON *joff = cJSON_GetObjectItem(req, "offset");
  const cJSON *jlen = cJSON_GetObjectItem(req, "length");
  const long offset = clamp_num(joff, 0, MEDIA_OFFSET_MAX, 0);
  const long length = clamp_num(jlen, 1, MEDIA_READ_MAX, MEDIA_READ_MAX);
  if (fseek(f, offset, SEEK_SET) != 0) {
    fclose(f);
    send_nack(KDP_CMD_MEDIA_THUMB, seq, "BAD_REQUEST", "Offset is past the end of the file");
    return;
  }
  uint8_t *buf = malloc((size_t)length);
  if (buf == NULL) {
    fclose(f);
    send_nack(KDP_CMD_MEDIA_THUMB, seq, "BUSY", "Out of memory");
    return;
  }
  const size_t got = fread(buf, 1, (size_t)length, f);
  fclose(f);
  media_card_done(); /* the bytes are in RAM; see media_card_done() */
  send_raw(KDP_CMD_MEDIA_THUMB, KDP_FLAG_RESPONSE | KDP_FLAG_BINARY, seq, buf, got);
  free(buf);
}

/*
 * MEDIA_LIST's fast path: the persisted order index.
 *
 * The walk below it opens META.JSON once per capture directory to sort by
 * capture time, and on the bench card of 1,325 that measured 81.7 s - long
 * past any client's timeout, which is how a card of photographs reached a UI
 * as nothing at all. gallery.c already maintains INDEX.TXT for exactly this
 * reason: capture times and names, newest first, written once per change to
 * the card.
 *
 * So: read that one file and page it. The whole index for 4096 entries is
 * about 200 KB, read into PSRAM in one fread, and gidx_page() counts every
 * valid line while copying only the requested window.
 *
 * Returns the number of items written to `out`, or -1 when the index is
 * missing, unreadable or has no usable header - which is the caller's signal
 * to fall back to the exhaustive walk. `*total` is every valid capture in the
 * index; `*stale` says the header disagreed with its own body, which means the
 * index wants rebuilding even though this read succeeded.
 */
static int media_index_page(int cursor, int limit, gidx_entry_t *out, int *total, bool *stale) {
  if (total != NULL) *total = 0;
  if (stale != NULL) *stale = false;

  FILE *f = fopen(CAPTURES_DIR "/" GIDX_FILE, "rb");
  if (f == NULL) return -1;

  const size_t cap = gidx_max_bytes(MEDIA_INDEX_MAX) + 1;
  char *text = heap_caps_malloc(cap, MALLOC_CAP_SPIRAM);
  if (text == NULL) {
    fclose(f);
    return -1;
  }
  const size_t got = fread(text, 1, cap - 1, f);
  fclose(f);
  text[got] = '\0';

  gidx_header_t hdr;
  int counted = 0, skipped = 0;
  const int n = gidx_page(text, cursor, limit, out, &hdr, &counted, &skipped);
  heap_caps_free(text);
  if (n < 0) return -1;

  /*
   * An index shorter than the card it describes.
   *
   * `total_seen` is what the walk that wrote this file counted on the card;
   * `entries` is what it could store. When the second is smaller the file is
   * honest but incomplete - written by a firmware whose cap was lower - and
   * reporting `counted` would under-report the card. So report the card's own
   * figure and ask the gallery to rebuild, which it can now do because this
   * build's cap fits.
   */
  if (counted < hdr.total_seen && hdr.total_seen <= MEDIA_INDEX_MAX) {
    ESP_LOGI(TAG, "order index holds %d of %d captures; asking for a rebuild", counted,
             hdr.total_seen);
    gallery_refresh();
    if (total != NULL) *total = hdr.total_seen;
    if (stale != NULL) *stale = true;
    return n;
  }

  if (total != NULL) *total = counted;
  if (stale != NULL) *stale = counted != hdr.entries;
  if (counted != hdr.entries) {
    /* Not fatal and not silent: the file is readable and every line in it is
     * good, but it does not hold what its own header claims - a write cut
     * short, or a card edited elsewhere. The count reported is the one the
     * lines support. */
    ESP_LOGW(TAG, "order index header claims %d captures, body holds %d", hdr.entries, counted);
  }
  if (skipped > 0) ESP_LOGW(TAG, "order index: %d unreadable lines skipped", skipped);
  return n;
}

static void handle_media_list(uint32_t seq, const cJSON *req) {
  storage_status_t sd;
  storage_get_status(&sd);
  if (!sd.mounted) {
    send_nack(KDP_CMD_MEDIA_LIST, seq, "NO_CARD", "No card mounted");
    return;
  }

  const cJSON *jc = cJSON_GetObjectItem(req, "cursor");
  const cJSON *jl = cJSON_GetObjectItem(req, "limit");
  const int cursor = (int)clamp_num(jc, 0, MEDIA_INDEX_MAX, 0);
  /* 100 is maxGalleryPageSize in GET_CAPABILITIES. */
  const int limit = (int)clamp_num(jl, 1, 100, 50);

  /*
   * FAST PATH: the persisted order index. RECOVERY PATH: the card walk.
   *
   * Normal listing must never walk the card - that is what took 81.7 s on a
   * 1,325-capture card and timed every client out. The walk stays for the case
   * the index cannot answer: missing, unreadable, or no usable header, which
   * happens on a card written by an older firmware, one edited in a PC, or
   * before the gallery has ever built the index.
   */
  gidx_entry_t *page = heap_caps_malloc(sizeof *page * (size_t)limit, MALLOC_CAP_SPIRAM);
  if (page == NULL) {
    send_nack(KDP_CMD_MEDIA_LIST, seq, "BUSY", "Out of memory");
    return;
  }
  int total = 0;
  bool stale = false;
  const int from_index = media_index_page(cursor, limit, page, &total, &stale);

  if (from_index >= 0) {
    cJSON *json = cJSON_CreateObject();
    /*
     * `total` is every valid capture the index holds - photographs, counted,
     * not directory entries. media_scan's old figure counted anything readdir
     * returned and reported 1325 where the photograph count was lower.
     */
    cJSON_AddNumberToObject(json, "total", total);
    cJSON *items = cJSON_AddArrayToObject(json, "items");
    for (int i = 0; i < from_index; i++) {
      cJSON_AddItemToArray(items, media_summary(page[i].name));
    }
    const int next = cursor + from_index;
    if (next < total) cJSON_AddNumberToObject(json, "nextCursor", next);
    else cJSON_AddNullToObject(json, "nextCursor");
    cJSON_AddBoolToObject(json, "hasMore", next < total);
    /* Beyond the Studio interface, and only when true: the index is readable
     * but disagrees with its own header, so the gallery owes a rebuild. A
     * host that ignores it sees a correct list either way. */
    if (stale) cJSON_AddBoolToObject(json, "indexStale", true);
    heap_caps_free(page);
    media_card_done(); /* the document is built; the write is not card work */
    send_json(KDP_CMD_MEDIA_LIST, seq, json);
    return;
  }
  heap_caps_free(page);

  ESP_LOGW(TAG, "no usable order index; falling back to the card walk");
  klog("P4", "media list: no order index, walking the card");

  char (*names)[64] = calloc(MEDIA_MAX_LIST, 64);
  if (names == NULL) {
    send_nack(KDP_CMD_MEDIA_LIST, seq, "BUSY", "Out of memory");
    return;
  }
  int on_card = 0;
  const int listable = media_scan(names, MEDIA_MAX_LIST, &on_card);

  cJSON *json = cJSON_CreateObject();
  /*
   * `on_card` now applies the product's eligibility rule inside media_scan -
   * a capture-shaped directory holding a committed META.JSON - so it is a
   * photograph count rather than a directory-entry count.
   */
  cJSON_AddNumberToObject(json, "total", on_card);
  cJSON *items = cJSON_AddArrayToObject(json, "items");
  int sent = 0;
  for (int i = cursor; i < listable && sent < limit; i++, sent++) {
    cJSON_AddItemToArray(items, media_summary(names[i]));
  }
  const int next = cursor + sent;
  if (next < listable) cJSON_AddNumberToObject(json, "nextCursor", next);
  else cJSON_AddNullToObject(json, "nextCursor");
  cJSON_AddBoolToObject(json, "hasMore", next < listable);
  free(names);
  media_card_done();
  send_json(KDP_CMD_MEDIA_LIST, seq, json);
}

static void handle_media_info(uint32_t seq, const cJSON *req) {
  const cJSON *jid = cJSON_GetObjectItem(req, "id");
  if (!cJSON_IsString(jid) || !media_id_ok(jid->valuestring)) {
    send_nack(KDP_CMD_MEDIA_INFO, seq, "BAD_REQUEST", "Expected a capture id");
    return;
  }
  const char *id = jid->valuestring;

  char dir[160];
  snprintf(dir, sizeof dir, "%s/%s", CAPTURES_DIR, id);
  struct stat st;
  if (stat(dir, &st) != 0) {
    send_nack(KDP_CMD_MEDIA_INFO, seq, "NOT_FOUND", "No such capture");
    return;
  }

  cJSON *json = media_summary(id);
  cJSON *files = cJSON_AddArrayToObject(json, "files");
  static const char *FILES[4] = {"C1.JPG", "C2.JPG", "C3.JPG", "C4.JPG"};
  for (int i = 0; i < 4; i++) {
    const long sz = media_file_size(id, FILES[i]);
    if (sz < 0) continue;
    cJSON *f = cJSON_CreateObject();
    cJSON_AddStringToObject(f, "name", FILES[i]);
    cJSON_AddNumberToObject(f, "sizeBytes", (double)sz);
    /* sha256 is in the contract and is not computed here: hashing four
     * multi-megabyte JPEGs on request would block the link for seconds. The
     * field is omitted rather than filled with a wrong or empty digest. */
    cJSON_AddItemToArray(files, f);
  }
  cJSON *meta = media_meta(id);
  if (meta) cJSON_AddItemToObject(json, "meta", meta);
  send_json(KDP_CMD_MEDIA_INFO, seq, json);
}

static void handle_media_delete(uint32_t seq, const cJSON *req) {
  const cJSON *jid = cJSON_GetObjectItem(req, "id");
  if (!cJSON_IsString(jid) || !media_id_ok(jid->valuestring)) {
    send_nack(KDP_CMD_MEDIA_DELETE, seq, "BAD_REQUEST", "Expected a capture id");
    return;
  }
  char dir[160];
  snprintf(dir, sizeof dir, "%s/%s", CAPTURES_DIR, jid->valuestring);
  struct stat st;
  if (stat(dir, &st) != 0) {
    send_nack(KDP_CMD_MEDIA_DELETE, seq, "NOT_FOUND", "No such capture");
    return;
  }
  /* Queue first, files second - the same order as Delete All. A job left
   * behind re-read a missing asset to the retry cap and parked FAILED, and
   * that number then sat in UPLOAD_QUEUE_STATUS until a reboot. */
  upload_queue_forget(jid->valuestring);
  storage_capture_delete(dir);
  /* Told, after the delete and only after it. The gallery's order index would
   * otherwise still name this capture, and the first evidence would be a tile
   * that cannot find its META.JSON - which costs a full rebuild of the order.
   * Non-blocking, so it is safe on the KDP server task; the mutation happens
   * on the gallery task. */
  gallery_note_removed(jid->valuestring);
  klog("P4", "media delete %s", jid->valuestring);
  cJSON *json = cJSON_CreateObject();
  cJSON_AddStringToObject(json, "id", jid->valuestring);
  cJSON_AddBoolToObject(json, "deleted", true);
  send_json(KDP_CMD_MEDIA_DELETE, seq, json);
}

/* Favourite is a flag inside META.JSON, so it travels with the capture when
 * the card is moved - which is the whole point of keeping no index.
 *
 * The read and the rewrite live here rather than inside the command handler
 * because the body's photograph screen sets the same flag (issue #144) and two
 * implementations of "rewrite META.JSON with favorite flipped" is one too
 * many. This file already owns media_meta() and the CAPTURES_DIR path, so
 * moving them into gallery.c would have dragged that with them.
 *
 * BOTH REQUIRE THE CALLER TO HOLD THE CARD, storage_acquire(STORAGE_USER_UI).
 * That is not only about the SD bus: media_meta() parses into file statics
 * that are safe precisely because every path that touches them holds the one
 * card mutex. The KDP side gets that from with_card(); the UI side takes it
 * around the call.
 */
esp_err_t media_favorite_set(const char *id, bool fav) {
  if (id == NULL || !media_id_ok(id)) return ESP_ERR_INVALID_ARG;
  cJSON *meta = media_meta(id);
  if (meta == NULL) return ESP_ERR_NOT_FOUND;

  cJSON_DeleteItemFromObject(meta, "favorite");
  cJSON_AddBoolToObject(meta, "favorite", fav);

  char path[160];
  snprintf(path, sizeof path, "%s/%s/META.JSON", CAPTURES_DIR, id);
  char *text = cJSON_PrintUnformatted(meta);
  cJSON_Delete(meta);
  if (text == NULL) return ESP_ERR_NO_MEM;

  FILE *f = fopen(path, "wb");
  if (f == NULL) {
    cJSON_free(text);
    return ESP_FAIL;
  }
  const size_t len = strlen(text);
  const size_t wrote = fwrite(text, 1, len, f);
  const int closed = fclose(f);
  cJSON_free(text);
  /* Checked, unlike the version this replaced. A short write leaves a
   * truncated META.JSON, which is a capture whose mode, frame count and label
   * all disappear from the gallery - a far worse outcome than a favourite that
   * did not stick, and it used to be reported as success. */
  if (wrote != len || closed != 0) return ESP_FAIL;
  return ESP_OK;
}

static void handle_media_favorite(uint32_t seq, const cJSON *req) {
  const cJSON *jid = cJSON_GetObjectItem(req, "id");
  const cJSON *jfav = cJSON_GetObjectItem(req, "favorite");
  if (!cJSON_IsString(jid) || !media_id_ok(jid->valuestring) || !cJSON_IsBool(jfav)) {
    send_nack(KDP_CMD_MEDIA_FAVORITE, seq, "BAD_REQUEST", "Expected {id, favorite}");
    return;
  }
  const char *id = jid->valuestring;
  const bool fav = cJSON_IsTrue(jfav);
  const esp_err_t err = media_favorite_set(id, fav);
  if (err == ESP_ERR_NOT_FOUND) {
    send_nack(KDP_CMD_MEDIA_FAVORITE, seq, "NOT_FOUND", "No metadata for that capture");
    return;
  }
  if (err == ESP_ERR_NO_MEM) {
    send_nack(KDP_CMD_MEDIA_FAVORITE, seq, "STORAGE_ERROR", "Out of memory");
    return;
  }
  if (err != ESP_OK) {
    send_nack(KDP_CMD_MEDIA_FAVORITE, seq, "STORAGE_ERROR", "Could not rewrite META.JSON");
    return;
  }

  cJSON *json = cJSON_CreateObject();
  cJSON_AddStringToObject(json, "id", id);
  cJSON_AddBoolToObject(json, "favorite", fav);
  send_json(KDP_CMD_MEDIA_FAVORITE, seq, json);
}

/** One measured pass, as additive detail alongside the contract fields. */
static void bench_pass_json(cJSON *dst, const storage_bench_pass_t *p) {
  cJSON_AddNumberToObject(dst, "bytes", p->bytes);
  cJSON_AddNumberToObject(dst, "writeMs", p->write_ms);
  cJSON_AddNumberToObject(dst, "readMs", p->read_ms);
  cJSON_AddNumberToObject(dst, "writeBytesPerSec", p->write_bytes_per_sec);
  cJSON_AddNumberToObject(dst, "readBytesPerSec", p->read_bytes_per_sec);
  /* CRCs as hex strings, the same convention the capture path uses for
   * checksums, so a mismatch can be compared by eye against a capture. */
  char hex[12];
  snprintf(hex, sizeof hex, "%08lx", (unsigned long)p->crc_written);
  cJSON_AddStringToObject(dst, "crc32Written", hex);
  snprintf(hex, sizeof hex, "%08lx", (unsigned long)p->crc_read);
  cJSON_AddStringToObject(dst, "crc32Read", hex);
  cJSON_AddBoolToObject(dst, "crcMatch", p->crc_match);
  cJSON_AddNumberToObject(dst, "chunkBytes", p->chunk_bytes);
  cJSON_AddNumberToObject(dst, "chunks", p->chunks);
  cJSON_AddNumberToObject(dst, "worstWriteChunkUs", p->worst_write_chunk_us);
  cJSON_AddNumberToObject(dst, "bestWriteChunkUs", p->best_write_chunk_us);
  cJSON_AddNumberToObject(dst, "meanWriteChunkUs", p->mean_write_chunk_us);
  cJSON_AddNumberToObject(dst, "p95WriteChunkUs", p->p95_write_chunk_us);
}

/**
 * STORAGE_BENCH (0x4c) — sustained throughput and per-block write latency.
 *
 * `benchDiagnostics` has advertised this command since Milestone 1B while the
 * dispatcher had no handler for it, so a host that trusted the flag got a
 * NACK. That is the one state the contract forbids: advertised-but-unsupported.
 *
 * The response carries the five fields StorageBenchResult requires
 * (writeMBs, readMBs, worstBlockMs, p95BlockMs, bytes) from the sustained run,
 * plus additive optional detail. No required field changed shape or unit.
 */
static void handle_storage_bench(uint32_t seq, const cJSON *req) {
  /* Shares the capture lock with CAMERA_TEST and the soak run: a megabyte of
   * card traffic during a capture would corrupt both measurements. */
  if (!capture_lock(0)) {
    send_nack(KDP_CMD_STORAGE_BENCH, seq, "BUSY", "A capture or soak run is active");
    return;
  }

  /* StorageBenchRequest: sizeMB, blockKB, passes. sizeMB is the contract's
   * unit; sizeKB is accepted additionally so a caller can ask for the 64 KiB
   * size STORAGE_SELF_TEST uses, which a whole number of megabytes cannot
   * express. Absent means the defaults storage_bench() documents. */
  const cJSON *jsize_mb = cJSON_GetObjectItem(req, "sizeMB");
  const cJSON *jsize_kb = cJSON_GetObjectItem(req, "sizeKB");
  const cJSON *jblock = cJSON_GetObjectItem(req, "blockKB");
  const cJSON *jpasses = cJSON_GetObjectItem(req, "passes");

  uint32_t size_kb = 0;
  if (cJSON_IsNumber(jsize_kb) && jsize_kb->valuedouble > 0) {
    size_kb = (uint32_t)jsize_kb->valuedouble;
  } else if (cJSON_IsNumber(jsize_mb) && jsize_mb->valuedouble > 0) {
    size_kb = (uint32_t)(jsize_mb->valuedouble * 1024.0);
  }
  const uint32_t block_kb = cJSON_IsNumber(jblock) ? (uint32_t)jblock->valuedouble : 0;
  const uint32_t passes = cJSON_IsNumber(jpasses) ? (uint32_t)jpasses->valuedouble : 0;

  /* The card as well as the cameras, for the same reason the self-test takes
   * it: the card watcher writes its own files on a card that has just
   * mounted, and a megabyte of bench traffic across that is two measurements
   * of each other (#210). */
  if (!storage_acquire(STORAGE_USER_UI, 3000)) {
    capture_unlock();
    send_nack(KDP_CMD_STORAGE_BENCH, seq, "BUSY", "The card is busy");
    return;
  }
  storage_bench_result_t r;
  storage_bench(size_kb, block_kb, passes, &r);
  storage_release(STORAGE_USER_UI);
  capture_unlock();

  if (!r.ok) {
    /* The failing phase is the diagnostic. "Slow" and "did not finish" are
     * different problems and a bare BENCH_FAILED conflates them. */
    char msg[96];
    snprintf(msg, sizeof msg, "Benchmark stopped at %s after %lu ms",
             storage_bench_phase_str(r.failed_phase), (unsigned long)r.total_ms);
    send_nack(KDP_CMD_STORAGE_BENCH, seq, storage_bench_phase_str(r.failed_phase), msg);
    return;
  }

  /* A verified round trip on this card, at a megabyte rather than 64 KB. */
  hwv_mark_validated(HWV_SD_LDO_CH4, "bench read-back CRC verified");

  cJSON *json = cJSON_CreateObject();

  /* ---- StorageBenchResult, exactly as typed ---- */
  const storage_bench_pass_t *s = &r.sustained;
  /* MB/s as the contract names it. Computed from bytes and milliseconds rather
   * than from the bytes-per-sec figure, so the two cannot drift. */
  const double write_mbs =
      s->write_ms > 0 ? ((double)s->bytes / 1048576.0) / ((double)s->write_ms / 1000.0) : 0.0;
  const double read_mbs =
      s->read_ms > 0 ? ((double)s->bytes / 1048576.0) / ((double)s->read_ms / 1000.0) : 0.0;
  cJSON_AddNumberToObject(json, "writeMBs", write_mbs);
  cJSON_AddNumberToObject(json, "readMBs", read_mbs);
  /* worstBlockMs / p95BlockMs are milliseconds per the contract, measured in
   * microseconds and converted here. Sub-millisecond blocks therefore report
   * as fractional rather than as zero — a card whose worst block is 400 us
   * should not read as 0. */
  cJSON_AddNumberToObject(json, "worstBlockMs", (double)s->worst_write_chunk_us / 1000.0);
  cJSON_AddNumberToObject(json, "p95BlockMs", (double)s->p95_write_chunk_us / 1000.0);
  cJSON_AddNumberToObject(json, "bytes", s->bytes);

  /* ---- additive, optional ---- */
  cJSON_AddBoolToObject(json, "ok", true);
  cJSON_AddNullToObject(json, "failedPhase");
  cJSON_AddNumberToObject(json, "passes", r.passes);
  cJSON_AddNumberToObject(json, "totalMs", r.total_ms);
  cJSON_AddBoolToObject(json, "cleanupOk", r.cleanup_ok);
  bench_pass_json(cJSON_AddObjectToObject(json, "sustained"), &r.sustained);
  /* The 64 KiB run, directly comparable with STORAGE_SELF_TEST on this card. */
  bench_pass_json(cJSON_AddObjectToObject(json, "small"), &r.small);

  send_json(KDP_CMD_STORAGE_BENCH, seq, json);
}

static void handle_storage_self_test(uint32_t seq) {
  if (!capture_lock(0)) {
    send_nack(KDP_CMD_STORAGE_SELF_TEST, seq, "BUSY", "A capture or soak run is active");
    return;
  }
  /*
   * And the card itself, which capture_lock() says nothing about.
   *
   * storage_watch.c runs this same self-test on a card that has just mounted,
   * under storage_acquire(); this path only excluded captures. Run the Studio
   * test inside that window and both tasks write, verify and unlink the one
   * fixed path through one shared static buffer - and the loser reports
   * VERIFY_FAILED on a healthy card, latches s_write_test to "fail", and the
   * camera tells its owner the card cannot hold a photograph (#210).
   */
  if (!storage_acquire(STORAGE_USER_UI, 3000)) {
    capture_unlock();
    send_nack(KDP_CMD_STORAGE_SELF_TEST, seq, "BUSY", "The card is busy");
    return;
  }
  storage_selftest_result_t result;
  storage_self_test(&result);
  storage_release(STORAGE_USER_UI);
  capture_unlock();

  if (result.ok) {
    storage_status_t sd;
    storage_get_status(&sd);
    char detail[40];
    snprintf(detail, sizeof detail, "self-test pass, %lu KB verified",
             (unsigned long)(result.bytes_tested / 1024));
    (void)sd;
    hwv_mark_validated(HWV_SD_LDO_CH4, detail);
  }

  cJSON *json = cJSON_CreateObject();
  cJSON_AddBoolToObject(json, "ok", result.ok);
  if (result.ok) cJSON_AddNullToObject(json, "failedPhase");
  else cJSON_AddStringToObject(json, "failedPhase",
                               storage_selftest_phase_str(result.failed_phase));
  cJSON_AddNumberToObject(json, "durationMs", result.duration_ms);
  cJSON_AddNumberToObject(json, "bytesTested", result.bytes_tested);
  send_json(KDP_CMD_STORAGE_SELF_TEST, seq, json);
}

static const char *kdp_camera_state(const camlink_info_t *info) {
  if (!info->online) return "offline";
  if (strcmp(info->state, NL_STATE_ERROR) == 0) return "error";
  if (strcmp(info->state, NL_STATE_EXPOSING) == 0) return "capturing";
  if (strcmp(info->state, NL_STATE_JPEG_READY) == 0 ||
      strcmp(info->state, NL_STATE_TRANSFERRING) == 0) {
    return "busy";
  }
  return "ready";
}

static cJSON *build_camera_info(int index) {
  static const char *ids[] = {"cam1", "cam2", "cam3", "cam4"};
  cJSON *json = cJSON_CreateObject();
  cJSON_AddStringToObject(json, "id", ids[index]);

  /*
   * Every channel answers for itself.
   *
   * This was `if (index == 0)`, with cam2-4 hardcoded offline behind the
   * comment "CAM2-4 links land in milestone 2; reported offline, never
   * faked". The faking is exactly what it was doing by the time anyone wired
   * a second camera: camlink_init() brings up all four UARTs on their real
   * pins, the sweep hellos each one, capture.c runs four workers and the
   * viewfinder pumps four channels - so a wired CAM2 could take a photograph
   * that this reply insisted was impossible, and every reader (Studio, the
   * ROLL screen, the SHOOT bar's n/4 LIVE, the conformance suite) believed
   * the reply. Same defect as GET_MODES' hardcoded availability (D21), found
   * the same way: a constant that outlived the reason for it.
   *
   * An unwired channel still reports offline - that is now measured by the
   * sweep getting no answer, not asserted by a branch.
   */
  {
    camlink_info_t info;
    camlink_get_info_ch(index, &info);
    camlink_stats_t stats;
    camlink_get_stats_ch(index, &stats);
    cJSON_AddBoolToObject(json, "online", info.online);
    if (info.online && info.sensor_detected) {
      cJSON_AddStringToObject(json, "sensor", info.sensor);
    } else {
      cJSON_AddNullToObject(json, "sensor");
    }
    cJSON_AddBoolToObject(json, "sensorDetected", info.online && info.sensor_detected);
    cJSON_AddStringToObject(json, "firmware", info.firmware);
    cJSON_AddStringToObject(json, "state", kdp_camera_state(&info));
    cJSON_AddNumberToObject(json, "latencyMs", info.latency_ms);
    cJSON_AddNumberToObject(json, "uartErrors", stats.crc_errors + stats.timeouts);
    // Node identity for the bench (passthrough fields, benchDiagnostics).
    if (info.online) {
      cJSON *node = cJSON_AddObjectToObject(json, "node");
      cJSON_AddStringToObject(node, "session", info.session);
      cJSON_AddStringToObject(node, "resetReason", info.reset_reason);
      if (info.chip_revision >= 0) cJSON_AddNumberToObject(node, "chipRevision", info.chip_revision);
      if (info.heap_kb >= 0) cJSON_AddNumberToObject(node, "heapKB", info.heap_kb);
      if (info.psram_kb >= 0) cJSON_AddNumberToObject(node, "psramKB", info.psram_kb);
      if (info.sensor_pid[0] != '\0') cJSON_AddStringToObject(node, "sensorPid", info.sensor_pid);
      cJSON_AddBoolToObject(node, "autofocus", info.autofocus);
      cJSON_AddNumberToObject(node, "baud", NL_DEFAULT_BAUD);
    }
  }
  /*
   * What the viewfinder made of this camera, including the frames it threw
   * away.
   *
   * Here rather than in CAMERA_LINK_STATS, where viewfinderFpsX10 already sits
   * and where these arguably belong by kind - a preview frame is a capture, a
   * chunked read and a release over one UART, so a dropped one is a link
   * measurement. The deciding fact is reach: that handler NACKs CAMERA_OFFLINE
   * for anything but cam1, because camlink's stats are still one global set
   * from Milestone 1B, so a per-camera drop counter put there would answer for
   * one camera out of four and hide exactly the "which pane is dropping"
   * question it exists to answer. build_camera_info() is per camera for all
   * four and GET_CAMERA_INFO returns the whole set in one request, which is the
   * shape a bench actually asks in.
   *
   * Outside the index == 0 branch on purpose: the pumps run on all four
   * channels whatever the link driver reports, so cam2-4 have real counters
   * here rather than the faked zeroes that branch has to emit for fields it
   * cannot know.
   */
  {
    vf_status_t vf;
    viewfinder_status(index, &vf);
    cJSON *v = cJSON_AddObjectToObject(json, "viewfinder");
    cJSON_AddNumberToObject(v, "frames", vf.frames);
    cJSON_AddNumberToObject(v, "fpsX10", vf.fps_x10);
    cJSON *drops = cJSON_AddObjectToObject(v, "drops");
    for (int r = 0; r < VF_DROP_REASONS; r++) {
      /* Keyed by vf_drop_str(), the same word the klog line uses, so a line in
       * the ring and a field on the wire cannot drift apart. */
      cJSON_AddNumberToObject(drops, vf_drop_str((vf_drop_t)r), vf.drops[r]);
    }
  }
  cJSON_AddNullToObject(json, "lastCapture"); /* no synchronized captures yet */
  return json;
}

static void handle_camera_info(uint32_t seq) {
  cJSON *json = cJSON_CreateObject();
  cJSON *cameras = cJSON_AddArrayToObject(json, "cameras");
  for (int i = 0; i < 4; i++) cJSON_AddItemToArray(cameras, build_camera_info(i));
  send_json(KDP_CMD_GET_CAMERA_INFO, seq, json);
}

static int cam_index_from_request(cJSON *req) {
  const cJSON *cam = cJSON_GetObjectItem(req, "cam");
  if (!cJSON_IsString(cam)) return -1;
  static const char *ids[] = {"cam1", "cam2", "cam3", "cam4"};
  for (int i = 0; i < 4; i++) {
    if (strcmp(cam->valuestring, ids[i]) == 0) return i;
  }
  return -1;
}

static void handle_camera_status(uint32_t seq, cJSON *req) {
  int index = cam_index_from_request(req);
  if (index < 0) {
    send_nack(KDP_CMD_CAMERA_STATUS, seq, "INVALID_ARGUMENT", "cam must be cam1..cam4");
    return;
  }
  send_json(KDP_CMD_CAMERA_STATUS, seq, build_camera_info(index));
}

static void handle_link_stats(uint32_t seq, cJSON *req) {
  int index = cam_index_from_request(req);
  if (index < 0) {
    send_nack(KDP_CMD_CAMERA_LINK_STATS, seq, "INVALID_ARGUMENT", "cam must be cam1..cam4");
    return;
  }
  camlink_info_t info;
  camlink_get_info_ch(index, &info);
  camlink_stats_t stats;
  camlink_get_stats_ch(index, &stats);

  cJSON *json = cJSON_CreateObject();
  cJSON_AddStringToObject(json, "cam", cam_id_str(index));
  cJSON_AddNumberToObject(json, "baud", NL_DEFAULT_BAUD);
  cJSON_AddBoolToObject(json, "connected", info.online);
  cJSON_AddNumberToObject(json, "rxFrames", stats.rx_frames);
  cJSON_AddNumberToObject(json, "txFrames", stats.tx_frames);
  cJSON_AddNumberToObject(json, "rxBytes", stats.rx_bytes);
  cJSON_AddNumberToObject(json, "txBytes", stats.tx_bytes);
  cJSON_AddNumberToObject(json, "crcErrors", stats.crc_errors);
  cJSON_AddNumberToObject(json, "decoderResyncs", stats.resyncs);
  cJSON_AddNumberToObject(json, "timeouts", stats.timeouts);
  cJSON_AddNumberToObject(json, "retries", stats.retries);
  cJSON_AddNumberToObject(json, "duplicateFrames", stats.duplicates);
  cJSON_AddNumberToObject(json, "lastSequence", stats.last_sequence);
  cJSON_AddNumberToObject(json, "latencyMaxMs", stats.latency_max_ms);
  if (info.reset_reason[0] != '\0') {
    cJSON_AddStringToObject(json, "lastNodeBootReason", info.reset_reason);
  } else {
    cJSON_AddNullToObject(json, "lastNodeBootReason");
  }
  if (stats.last_error[0] != '\0') cJSON_AddStringToObject(json, "lastError", stats.last_error);
  else cJSON_AddNullToObject(json, "lastError");
  /* The viewfinder's own rate on this channel, tenths of a frame per second.
   * Every preview frame is a capture, a chunked read and a release over this
   * UART, so the finder's frame rate IS a link measurement and belongs here
   * rather than in a UI-only counter nothing outside the device can read. */
  cJSON_AddNumberToObject(json, "viewfinderFpsX10", viewfinder_fps_x10(index));
  send_json(KDP_CMD_CAMERA_LINK_STATS, seq, json);
}

static void handle_link_stats_reset(uint32_t seq, cJSON *req) {
  int index = cam_index_from_request(req);
  if (index < 0) {
    send_nack(KDP_CMD_CAMERA_LINK_STATS_RESET, seq, "INVALID_ARGUMENT", "cam must be cam1..cam4");
    return;
  }
  camlink_reset_stats_ch(index);
  cJSON *json = cJSON_CreateObject();
  cJSON_AddBoolToObject(json, "ok", true);
  send_json(KDP_CMD_CAMERA_LINK_STATS_RESET, seq, json);
}

/** Live LOG events for every klog() line, contract LogEntry shape. */
/*
 * The LOG event path, and why it has a queue in it.
 *
 * klog() is called from the UI task once a second, from the capture workers,
 * from the radio supervisor - from everything. It used to hand the event
 * straight to send_raw(), which takes the TX lock with portMAX_DELAY and then
 * calls usb_serial_jtag_write_bytes() with portMAX_DELAY. When no host is
 * draining USB-Serial-JTAG the TX FIFO fills and every one of those tasks
 * stops on the wire, for as long as nobody is listening. Measured on
 * KD4-D121BC: the UI watchdog reporting STALLED from 16 s uptime, and 17-22 s
 * gaps between consecutive klog() calls on the radio supervisor that looked,
 * on the coprocessor's console, like the transport pausing between RPCs.
 *
 * So the caller now does one non-blocking queue send and returns. A drain
 * task at low priority owns the wire. When the queue is full the event is
 * dropped and counted - the local ring in klog.c still has it, GET_LOGS still
 * serves it, and GET_RUNTIME_STATS says how many external events went
 * missing. Losing an event on a link nobody is reading is the correct trade;
 * stalling the shutter is not.
 *
 * The queue alone did not finish the job. The drain task took s_tx_lock and
 * then waited on the TX FIFO with portMAX_DELAY, so it could sit there
 * forever holding the lock server_task needs to answer a request: the tasks
 * calling klog() were free, but the one host that WAS talking to us got no
 * reply. The event write is therefore bounded at EVENT_WRITE_TIMEOUT_MS
 * (send_raw_event above) and a short write drops the event into the same
 * counter. The cost is a truncated frame on the wire, which the host decoder
 * resyncs past on the next magic.
 *
 * Responses kept the unbounded write for a while longer, on the argument that a
 * request with no answer is the one failure the contract forbids. That argument
 * was wrong by one step: an unbounded response write holds s_tx_lock, and the
 * drain task's 250 ms deadline is unreachable behind a lock taken with
 * portMAX_DELAY - so one host that stopped reading stalled both tasks anyway,
 * and the unanswered request happened regardless. Responses are now bounded at
 * RESPONSE_WRITE_TIMEOUT_MS with the lock bounded at TX_LOCK_TIMEOUT_MS, six
 * times the event budget, so a slow-but-real host still gets its reply.
 */
typedef struct {
  int64_t t_ms;
  int64_t t_us;
  char src[6];
  char msg[96]; /* KLOG_MSG_MAX */
} log_evt_t;

#define LOG_EVT_QUEUE_LEN 32
static QueueHandle_t s_log_q;

static void log_drain_task(void *arg) {
  (void)arg;
  log_evt_t e;
  for (;;) {
    if (xQueueReceive(s_log_q, &e, portMAX_DELAY) != pdTRUE) continue;
    cJSON *json = cJSON_CreateObject();
    /* `t` keeps its contract meaning: epoch milliseconds, wall clock. `us` is
     * additive - monotonic microseconds since boot, for ordering events that
     * land inside the same millisecond. See klog.h on why there are two. */
    cJSON_AddNumberToObject(json, "t", (double)e.t_ms);
    cJSON_AddNumberToObject(json, "us", (double)e.t_us);
    cJSON_AddStringToObject(json, "src", e.src);
    cJSON_AddStringToObject(json, "msg", e.msg);
    send_event(KDP_EVT_LOG, json);
  }
}

static void log_emitter(int64_t t_ms, int64_t t_us, const char *src, const char *msg) {
  if (s_log_q == NULL) return;
  log_evt_t e = {.t_ms = t_ms, .t_us = t_us};
  strlcpy(e.src, src, sizeof e.src);
  strlcpy(e.msg, msg, sizeof e.msg);
  if (xQueueSend(s_log_q, &e, 0) != pdTRUE) {
    atomic_fetch_add(&s_log_dropped, 1);
  }
}

static void handle_get_logs(uint32_t seq) {
  cJSON *json = cJSON_CreateObject();
  /* 64 B of headroom for the {"entries":[...]} envelope. */
  cJSON_AddItemToObject(json, "entries", klog_entries_json(KDP_MAX_PAYLOAD - 64));
  send_json(KDP_CMD_GET_LOGS, seq, json);
}

static void handle_clear_logs(uint32_t seq) {
  klog_clear();
  cJSON *json = cJSON_CreateObject();
  cJSON_AddBoolToObject(json, "ok", true);
  send_json(KDP_CMD_CLEAR_LOGS, seq, json);
}

static void handle_runtime_stats(uint32_t seq) {
  cJSON *json = cJSON_CreateObject();
  cJSON_AddNumberToObject(json, "uptimeS", (double)(esp_timer_get_time() / 1000000));
  cJSON_AddStringToObject(json, "resetReason", reset_reason_str());
  cJSON_AddNumberToObject(json, "freeHeapKB", heap_kb());
  cJSON_AddNumberToObject(json, "freePsramKB", psram_kb());
  /* Internal RAM is the scarce one: ESP-Hosted's DMA buffers, the SDMMC
   * driver and every ISR-touched buffer live there, and on the P4 the PSRAM
   * heap carries no MALLOC_CAP_DMA. The largest DMA-capable block is what a
   * radio recovery has to find (net_hosted.c, the recovery reserve). */
  cJSON_AddNumberToObject(json, "internalFreeKB",
                          (double)(heap_caps_get_free_size(MALLOC_CAP_INTERNAL) / 1024));
  cJSON_AddNumberToObject(json, "internalMinFreeKB",
                          (double)(heap_caps_get_minimum_free_size(MALLOC_CAP_INTERNAL) / 1024));
  cJSON_AddNumberToObject(json, "largestInternalDmaKB",
                          (double)(heap_caps_get_largest_free_block(MALLOC_CAP_INTERNAL | MALLOC_CAP_DMA) / 1024));
  /* Whether the C6 recovery reserve is fully held (#162). False means the radio
   * works but a C6 reset is not guaranteed to re-init without asserting;
   * additive and honest, so a boot never silently claims recoverability. */
  cJSON_AddBoolToObject(json, "recoveryReady", net_hosted_recovery_ready());
  /* The node scheduler (cam_sched.h): how often maintenance ran, how often it
   * stood aside for a capture, how often a capture waited for a probe to end.
   * Additive; the bench reads them to prove discovery keeps running. */
  {
    uint32_t probes_run = 0, probes_deferred = 0, capture_waits = 0;
    capture_sched_stats(&probes_run, &probes_deferred, &capture_waits);
    cJSON_AddNumberToObject(json, "probesRun", probes_run);
    cJSON_AddNumberToObject(json, "probesDeferred", probes_deferred);
    cJSON_AddNumberToObject(json, "captureProbeWaits", capture_waits);
  }

  // Real die temperatures or null — never a fabricated number.
  cJSON *temp = cJSON_AddObjectToObject(json, "tempC");
  float celsius = 0;
  if (s_tsens != NULL && temperature_sensor_get_celsius(s_tsens, &celsius) == ESP_OK) {
    cJSON_AddNumberToObject(temp, "p4", (double)((int)(celsius + 0.5f)));
  } else {
    cJSON_AddNullToObject(temp, "p4");
  }
  /* One entry per channel. A node's die temperature arrives in its STATUS
   * reply, which the probe sweep in main.c now asks of every online channel
   * (camlink_ping_ch); null for a channel that is offline or whose node has
   * not reported one. This was cam1 followed by three hardcoded nulls, from
   * before CAM2-4 had links. */
  cJSON *cams = cJSON_AddArrayToObject(temp, "cams");
  for (int i = 0; i < CAMLINK_CAMS; i++) {
    camlink_info_t info;
    camlink_get_info_ch(i, &info);
    if (info.online && info.temp_c != CAMLINK_TEMP_UNKNOWN) {
      cJSON_AddItemToArray(cams, cJSON_CreateNumber(info.temp_c));
    } else {
      cJSON_AddItemToArray(cams, cJSON_CreateNull());
    }
  }

  camlink_stats_t link;
  camlink_get_stats(&link);
  cJSON *protocol = cJSON_AddObjectToObject(json, "protocol");
  cJSON_AddNumberToObject(protocol, "droppedPackets", s_decoder.stats.resyncs);
  cJSON_AddNumberToObject(protocol, "crcFailures", s_decoder.stats.crc_failures);
  cJSON_AddNumberToObject(protocol, "cameraTimeouts", link.timeouts);
  cJSON_AddNumberToObject(protocol, "sdErrors", storage_sd_errors());
  /* Events this device could not deliver: no room in the queue, or the host
   * did not take the frame inside EVENT_WRITE_TIMEOUT_MS. Both mean nobody
   * was draining the link. Nonzero is not a fault; it is the price of the UI
   * and the request path not stalling behind it. */
  cJSON_AddNumberToObject(protocol, "droppedLogEvents",
                          (double)atomic_load(&s_log_dropped));
  /* Frames that never reached the wire: the TX lock was held past
   * TX_LOCK_TIMEOUT_MS, or the host did not take a whole frame inside its
   * write deadline. Responses count here, so nonzero means a host somewhere
   * saw a command time out - which is why it is not folded into
   * droppedLogEvents above. */
  cJSON_AddNumberToObject(protocol, "droppedTxFrames",
                          (double)atomic_load(&s_tx_dropped));

  /*
   * Per-task stack headroom, additive and optional.
   *
   * Thirteen long-lived tasks carry hand-chosen stack sizes that have never
   * been measured, and the 500-capture soak in M1 is exactly the workload that
   * would find one of them short. Cheap to expose now; expensive to discover
   * as a stack-overflow panic mid-soak.
   *
   * `minFreeBytes` is BYTES on this target and the unit is derived, not
   * assumed: uxTaskGetStackHighWaterMark() divides its byte count by
   * sizeof(StackType_t), and the ESP-IDF RISC-V port defines
   * portSTACK_TYPE as uint8_t, so that division is by one. FreeRTOS's own
   * header says "words" - true on ports where StackType_t is wider. See
   * taskmon.h.
   *
   * It is the MINIMUM FREE space the task has ever had, not the amount used.
   * Small is bad.
   */
  taskmon_row_t rows[TASKMON_MAX];
  const int rows_n = taskmon_snapshot(rows, TASKMON_MAX);
  cJSON *tasks = cJSON_AddArrayToObject(json, "tasks");
  for (int i = 0; i < rows_n; i++) {
    cJSON *t = cJSON_CreateObject();
    cJSON_AddStringToObject(t, "name", rows[i].name);
    if (rows[i].measured) {
      cJSON_AddNumberToObject(t, "minFreeBytes", rows[i].min_free_bytes);
    } else {
      /* Registered but no handle retained: the row exists and says it has no
       * measurement rather than reporting a plausible zero. */
      cJSON_AddNullToObject(t, "minFreeBytes");
    }
    /* Present only when true: a one-shot task that has finished, whose number
     * is its last reading rather than a live one. Emitting it for every row
     * would put a false on sixteen long-lived tasks to describe one. */
    if (rows[i].exited) cJSON_AddBoolToObject(t, "exited", true);
    cJSON_AddItemToArray(tasks, t);
  }
  cJSON_AddNumberToObject(json, "tasksUnmeasured", taskmon_unmeasured());

  /*
   * Is the UI task still turning over?
   *
   * The rows above say how close each task came to overflowing its stack and
   * nothing at all about whether it is still running - taskmon holds a handle,
   * not a heartbeat. The UI's own once-a-second klog line cannot answer it
   * either: that line runs ON the UI task, so a task blocked in a draw simply
   * stops producing it, and silence is indistinguishable from a healthy idle
   * camera with nothing to say. Reading the old line as a wedge, and then
   * having the boot evidence flooded out of the ring by it, is issue #140.
   *
   * This is the positive form. The loop stamps a pass counter and a timestamp;
   * this handler runs on the KDP server task at priority 9 and answers whether
   * or not that loop ever runs again. `lastPassAgeMs` should be a few tens of
   * milliseconds - the loop's own delay is 20-90 ms - so anything in seconds is
   * a wedge, positively, and `passes == 0` is a UI that never started rather
   * than one that stopped.
   */
  {
    uint32_t ui_passes = 0, ui_age_ms = 0;
    bool ui_stalled = false;
    ui_liveness(&ui_passes, &ui_age_ms, &ui_stalled);
    cJSON *ui = cJSON_AddObjectToObject(json, "ui");
    cJSON_AddNumberToObject(ui, "passes", ui_passes);
    cJSON_AddNumberToObject(ui, "lastPassAgeMs", ui_age_ms);
    /* The health watch's latched verdict: the loop is running and has not
     * presented a frame it owed. Not derived from lastPassAgeMs - a UI that
     * loops without presenting has a healthy age and a stale panel, which is
     * the failure the two fields exist to tell apart. */
    cJSON_AddBoolToObject(ui, "stalled", ui_stalled);
  }

  send_json(KDP_CMD_GET_RUNTIME_STATS, seq, json);
}

// ---- self test ----

#define SELFTEST_TOTAL 6

static void selftest_emit(int index, const char *name, const char *status,
                          const char *detail, cJSON *results) {
  cJSON *json = cJSON_CreateObject();
  cJSON_AddNumberToObject(json, "index", index);
  cJSON_AddNumberToObject(json, "total", SELFTEST_TOTAL);
  cJSON_AddStringToObject(json, "name", name);
  cJSON_AddStringToObject(json, "status", status);
  if (detail != NULL) cJSON_AddStringToObject(json, "detail", detail);
  if (results != NULL) {
    cJSON_AddBoolToObject(json, "done", true);
    cJSON_AddItemToObject(json, "results", results);
  }
  send_event(KDP_EVT_SELF_TEST, json);
}
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
