b5463/kino-d4/firmware/p4/main/pure.c

#include "pure.h"

#include <stdio.h>
#include <string.h>

/* ------------------------------------------------------------------ */
/* Capture                                                             */
/* ------------------------------------------------------------------ */

int pure_quality_to_sensor(int percent) {
  if (percent <= 0) return 0; /* "not specified" - let the node keep its own */
  if (percent > 100) percent = 100;
  const int q = 20 - ((percent - 60) * 15) / 35;
  if (q < 5) return 5;
  if (q > 40) return 40;
  return q;
}

void pure_frame_quality(bool sensor_owns, int applied_quality, int mode_quality,
                        int *cap_quality, int *record_quality) {
  int carry = 0;   /* what NL_CMD_CAPTURE sends */
  int record = 0;  /* what the register holds at exposure */

  if (sensor_owns && applied_quality > 0) {
    /* NL_CMD_SENSOR wrote it and still owns it: the CAPTURE must not carry a
     * quality, or it would overwrite the look's value an instant before the
     * exposure. What is recorded is what the node said it accepted. */
    record = applied_quality;
  } else if (mode_quality > 0) {
    /* Nothing stands in the register that we know of, so the CAPTURE carries
     * the mode default and the node writes it. Recorded after the node's own
     * clamp, because the clamp is what lands in the sensor. */
    carry = mode_quality;
    record = mode_quality;
    if (record < PURE_SENSOR_QUALITY_MIN) record = PURE_SENSOR_QUALITY_MIN;
    if (record > PURE_SENSOR_QUALITY_MAX) record = PURE_SENSOR_QUALITY_MAX;
  }
  /* Both zero: no quality was ever established for this camera. Say nothing.
   * A capture still happens - the sensor keeps whatever its driver left. */

  if (cap_quality != NULL) *cap_quality = carry;
  if (record_quality != NULL) *record_quality = record;
}

int pure_ev_to_ae_level(double ev) {
  /* NaN first, and without math.h: isnan() would drag libm into a test binary
   * the Makefile links without -lm, and every comparison below is false for a
   * NaN anyway, so it would fall through the clamps to the cast. */
  if (ev != ev) return 0;
  /* The clamps come BEFORE the cast, which is what makes the cast safe: a
   * look document can carry 1e300, and converting that to int is undefined
   * behaviour, not a large number. Both bounds are inclusive because a
   * half-step rounds away from zero - exactly -1.5 is -2. */
  if (ev >= 1.5) return 2;
  if (ev <= -1.5) return -2;
  /* Round half away from zero on a value now known to be within +/-1.5, so
   * the addition cannot leave the int range. */
  return (int)(ev + (ev >= 0.0 ? 0.5 : -0.5));
}

int pure_gain_to_ceiling(const char *gain) {
  if (gain == NULL) return 0;
  if (strcmp(gain, "low") == 0) return 4;
  if (strcmp(gain, "high") == 0) return 32;
  /* "auto" and anything unrecognised both mean "send no gainCeiling". They
   * are deliberately the same answer: a slot carrying a word this firmware
   * does not know must leave the AGC alone rather than pick a number for it. */
  return 0;
}

bool pure_parse_resolution(const char *s, uint32_t *width, uint32_t *height) {
  if (s == NULL) return false;
  const uint32_t MAX_DIM = 4096;

  uint32_t w = 0, h = 0;
  size_t i = 0;
  int digits = 0;
  for (; s[i] >= '0' && s[i] <= '9'; i++, digits++) {
    w = w * 10u + (uint32_t)(s[i] - '0');
    if (w > MAX_DIM) return false;
  }
  if (digits == 0 || s[i] != 'x') return false;
  i++;

  digits = 0;
  for (; s[i] >= '0' && s[i] <= '9'; i++, digits++) {
    h = h * 10u + (uint32_t)(s[i] - '0');
    if (h > MAX_DIM) return false;
  }
  /* Trailing characters mean we did not understand the whole string. */
  if (digits == 0 || s[i] != '\0') return false;
  if (w == 0 || h == 0) return false;

  if (width != NULL) *width = w;
  if (height != NULL) *height = h;
  return true;
}

/* ------------------------------------------------------------------ */
/* Storage                                                             */
/* ------------------------------------------------------------------ */

uint64_t pure_capture_reserve_bytes(int frames, uint32_t width, uint32_t height) {
  if (frames < 1) frames = 1;
  if (frames > 4) frames = 4;
  if (width == 0 || height == 0) {
    width = 2048;
    height = 1536;
  }
  const uint64_t per_frame = ((uint64_t)width * height) / 2u; /* 0.5 bpp bound */
  return per_frame * (uint64_t)frames + PURE_RESERVE_THUMB_BYTES + PURE_RESERVE_META_BYTES +
         PURE_RESERVE_MARGIN_BYTES;
}

bool pure_is_capture_dirname(const char *name) {
  if (name == NULL) return false;
  size_t n = 0;
  while (name[n] != '\0') {
    if (n > 36) return false; /* longer than a UUID; stop early */
    n++;
  }
  if (n != 36) return false;
  for (int i = 0; i < 36; i++) {
    const char c = name[i];
    if (i == 8 || i == 13 || i == 18 || i == 23) {
      if (c != '-') return false;
      continue;
    }
    const bool hex = (c >= '0' && c <= '9') || (c >= 'a' && c <= 'f');
    if (!hex) return false;
  }
  return true;
}

/* ------------------------------------------------------------------ */
/* Thumbnails                                                          */
/* ------------------------------------------------------------------ */

int pure_scale_sixteenths(uint32_t w, uint32_t h, uint32_t box_w, uint32_t box_h) {
  if (w == 0u || h == 0u || box_w == 0u || box_h == 0u) return 0;
  const uint32_t by_w = (box_w * 16u) / w;
  const uint32_t by_h = (box_h * 16u) / h;
  uint32_t n = by_w < by_h ? by_w : by_h;
  /* Below 1/16 the picture cannot be made to fit at all. Returning 1 here -
   * which this did - hands back a ratio whose output is LARGER than the
   * destination, and the PPA then writes outside the tile it was given. The
   * host test caught it: 1600 wide at 1/16 is 100 px into a 96 px box.
   *
   * No caller is currently reducing by more than 16x (UXGA into 320x240 is
   * 2.5x, into a 208x156 gallery tile is 7.7x), so nothing overflows today.
   * That is luck, not a guarantee, and the next box size someone picks is
   * where the luck runs out. 0 means "cannot fit" and both callers already
   * treat a zero output size as a refusal. */
  if (n < 1u) return 0;
  if (n > 16u) n = 16u;
  return (int)n;
}

/* ------------------------------------------------------------------ */
/* Clock                                                              */
/* ------------------------------------------------------------------ */

bool pure_epoch_plausible(int64_t epoch_ms) {
  return epoch_ms >= PURE_EPOCH_MS_MIN && epoch_ms <= PURE_EPOCH_MS_MAX;
}

int pure_clamp_utc_offset_min(int offset_min) {
  if (offset_min < -840 || offset_min > 840) return 0;
  return offset_min;
}

pure_clock_action_t pure_clock_restore_action(bool have_saved, int64_t saved_ms,
                                             int64_t system_now_ms) {
  const bool saved_ok = have_saved && pure_epoch_plausible(saved_ms);
  const bool system_ok = pure_epoch_plausible(system_now_ms);

  if (saved_ok && system_ok) {
    /* Both are real times, so take the later one. Equal counts as keep: there
     * is nothing to gain from a settimeofday() that changes nothing. */
    return saved_ms > system_now_ms ? PURE_CLOCK_RESTORE_SAVED : PURE_CLOCK_KEEP_SYSTEM;
  }
  if (saved_ok) return PURE_CLOCK_RESTORE_SAVED;
  if (system_ok) return PURE_CLOCK_KEEP_SYSTEM;
  return PURE_CLOCK_UNSET;
}

pure_clock_adopt_t pure_clock_adopt_action(int current_rank, int64_t current_ms,
                                           int incoming_rank, int64_t incoming_ms) {
  if (!pure_epoch_plausible(incoming_ms)) return PURE_CLOCK_REJECT_IMPLAUSIBLE;
  if (incoming_rank < current_rank) return PURE_CLOCK_REJECT_RANK;
  if (incoming_rank > current_rank) {
    /* A better source is allowed to move the clock backwards. Refusing here
     * would leave a unit that once had a wrong time permanently unable to be
     * corrected, which is worse than one backwards step. */
    return PURE_CLOCK_ADOPT;
  }
  if (incoming_rank == PURE_CLOCK_RANK_HOST) {
    /* A host at the same rank is a person typing a time in, which is what
     * SET_TIME has always been and what the bench uses to fix a clock that is
     * wrong the other way. The backwards guard is for automatic sources. */
    return PURE_CLOCK_ADOPT;
  }
  if (incoming_ms < current_ms) return PURE_CLOCK_REJECT_BACKWARDS;
  return PURE_CLOCK_ADOPT;
}

/*
 * Days-from-civil / civil-from-days, after Howard Hinnant's public-domain
 * chrono algorithms. Used instead of gmtime_r so the device and the host test
 * run identical arithmetic with no libc or timezone involvement — a formatter
 * that agreed with the test only because both called the same libc would be
 * testing libc.
 *
 * Era-based: shifts the year so March is month 1, which makes the leap day the
 * last day of the year and removes every special case from the month-length
 * table.
 */
static void civil_from_days(int64_t z, int *y_out, unsigned *m_out, unsigned *d_out) {
  z += 719468; /* shift epoch from 1970-01-01 to 0000-03-01 */
  const int64_t era = (z >= 0 ? z : z - 146096) / 146097;
  const unsigned doe = (unsigned)(z - era * 146097);                    /* 0..146096 */
  const unsigned yoe = (doe - doe / 1460 + doe / 36524 - doe / 146096) / 365; /* 0..399 */
  const int64_t y = (int64_t)yoe + era * 400;
  const unsigned doy = doe - (365 * yoe + yoe / 4 - yoe / 100);         /* 0..365 */
  const unsigned mp = (5 * doy + 2) / 153;                              /* 0..11 */
  const unsigned d = doy - (153 * mp + 2) / 5 + 1;                      /* 1..31 */
  const unsigned m = mp < 10 ? mp + 3 : mp - 9;                         /* 1..12 */

  *y_out = (int)(y + (m <= 2 ? 1 : 0));
  *m_out = m;
  *d_out = d;
}

void pure_format_iso8601(int64_t epoch_ms, int offset_min, char *out, size_t cap) {
  if (out == NULL || cap == 0) return;

  const int64_t local_ms = epoch_ms + (int64_t)offset_min * 60000;
  /* Floor division, so instants before the epoch still land on the right day
   * rather than rounding toward zero into the wrong one. */
  int64_t secs = local_ms / 1000;
  if (local_ms % 1000 != 0 && local_ms < 0) secs -= 1;

  int64_t days = secs / 86400;
  int64_t rem = secs % 86400;
  if (rem < 0) {
    rem += 86400;
    days -= 1;
  }

  int year = 0;
  unsigned month = 0, day = 0;
  civil_from_days(days, &year, &month, &day);

  const unsigned hh = (unsigned)(rem / 3600);
  const unsigned mm = (unsigned)((rem % 3600) / 60);
  const unsigned ss = (unsigned)(rem % 60);

  const int off = offset_min;
  const int abs_off = off < 0 ? -off : off;
  snprintf(out, cap, "%04d-%02u-%02uT%02u:%02u:%02u%c%02d:%02d", year, month, day, hh, mm, ss,
           off < 0 ? '-' : '+', abs_off / 60, abs_off % 60);
}

/* ------------------------------------------------------------------ */
/* Wi-Fi credentials                                                  */
/* ------------------------------------------------------------------ */

bool pure_wifi_ssid_valid(const char *ssid) {
  if (ssid == NULL) return false;
  size_t n = strlen(ssid);
  if (n == 0 || n > PURE_SSID_MAX) return false;
  for (size_t i = 0; i < n; i++) {
    const unsigned char c = (unsigned char)ssid[i];
    /* Reject C0 controls and DEL. Everything above 0x7f is left alone: an AP
     * named in UTF-8 is an AP the camera has to be able to join, and this
     * value is also an NVS key suffix, so rewriting it would save a network
     * that can never match the scan result it came from. */
    if (c < 0x20 || c == 0x7f) return false;
  }
  return true;
}

bool pure_wifi_passphrase_ok(const char *passphrase, bool is_open, bool keeps_stored) {
  const size_t n = passphrase == NULL ? 0 : strlen(passphrase);

  if (is_open) {
    /* An open network takes no passphrase. Accepting one and then not using
     * it would store a secret the radio never presents, which is worse than
     * refusing: it reads on the display as a protected network. */
    return n == 0;
  }

  /* The keep-what-is-stored case, checked BEFORE the length rule. Reversing
   * these two makes editing a saved network's autoJoin impossible, because
   * the host has only ever been given the mask. */
  if (n == 0) return keeps_stored;

  return n >= PURE_WPA_PASSPHRASE_MIN && n <= PURE_WPA_PASSPHRASE_MAX;
}

bool pure_api_base_ok(const char *url) {
  if (url == NULL) return false;
  const char *host;
  if (strncmp(url, "https://", 8) == 0) {
    host = url + 8;
  } else if (strncmp(url, "http://", 7) == 0) {
    host = url + 7;
  } else {
    return false;
  }
  if (*host == '\0') return false;
  size_t n = 0;
  for (const char *c = url; *c != '\0'; c++) {
    if (++n > PURE_API_BASE_MAX) return false;
    if ((unsigned char)*c <= 0x20 || (unsigned char)*c >= 0x7f) return false;
    if (*c == '@' || *c == '?' || *c == '#') return false;
  }
  /* Nothing after host[:port]: no path, no trailing slash. */
  for (const char *c = host; *c != '\0'; c++) {
    if (*c == '/') return false;
  }
  /* A port, if present, is digits only. */
  const char *colon = strchr(host, ':');
  if (colon != NULL) {
    if (colon == host || colon[1] == '\0') return false;
    for (const char *c = colon + 1; *c != '\0'; c++) {
      if (*c < '0' || *c > '9') return false;
    }
  }
  return true;
}


ui_health_report_t ui_health_step(ui_health_t *h, bool present_due, bool frames_advanced,
                                  bool input_latched) {
  if (h == NULL) return UI_HEALTH_QUIET;

  if (input_latched) {
    /* Saturating: at one tick a second this is 18 hours, and a wrap would let
     * a permanently stuck latch look briefly un-stuck. */
    if (h->latch_ticks < UINT16_MAX) h->latch_ticks++;
  } else {
    h->latch_ticks = 0;
  }

  /* The cause before the symptom - see the header note. */
  if (!h->latch_stuck && h->latch_ticks >= PURE_UI_LATCH_TICKS) {
    h->latch_stuck = true;
    return UI_HEALTH_LATCH_STUCK;
  }
  if (h->latch_stuck && h->latch_ticks == 0) {
    h->latch_stuck = false;
    return UI_HEALTH_LATCH_CLEARED;
  }

  if (!h->stalled) {
    if (present_due && !frames_advanced) {
      h->stalled = true;
      return UI_HEALTH_STALLED;
    }
    return UI_HEALTH_QUIET;
  }

  /* Two ways out, and they are not the same news. A frame arriving means the
   * compositor recovered. Work draining without one means the screen stopped
   * needing a frame it never drew - the episode is over and something was
   * dropped - and saying "presenting again" there would be a fresh lie of
   * exactly the kind this function exists to remove. */
  if (frames_advanced) {
    h->stalled = false;
    return UI_HEALTH_PRESENTING;
  }
  if (!present_due) {
    h->stalled = false;
    return UI_HEALTH_STALL_ENDED;
  }
  return UI_HEALTH_QUIET;
}

const char *capture_unavailable_reason(bool card_mounted, bool any_camera_ready) {
  /* capture_fire()'s own order. The first blocking fact is the useful one. */
  if (!card_mounted) return "No card to write the capture to";
  if (!any_camera_ready) return "No camera node answered";
  return NULL;
}

/* ------------------------------------------------------------------ */
/* Wigglegram playback                                                 */
/* ------------------------------------------------------------------ */

pure_wiggle_loop_t pure_wiggle_loop(const char *word) {
  if (word == NULL) return PURE_WIGGLE_BOUNCE;
  if (strcmp(word, "continuous") == 0) return PURE_WIGGLE_CONTINUOUS;
  if (strcmp(word, "sweep") == 0) return PURE_WIGGLE_SWEEP;
  /* Including "bounce" itself, and including anything this firmware has never
   * heard of. See the header: an envelope that has been through a host this
   * camera does not know still gets a wiggle. */
  return PURE_WIGGLE_BOUNCE;
}

bool pure_wiggle_direction_rtl(const char *word) {
  return word != NULL && strcmp(word, "rtl") == 0;
}

int pure_wiggle_sequence(pure_wiggle_loop_t loop, bool rtl, unsigned present, uint8_t *seq,
                         int cap, bool *repeats) {
  if (repeats != NULL) *repeats = loop != PURE_WIGGLE_SWEEP;

  /* The present frames in camera order. `have[p]` is the frame index at
   * position p, so everything below reasons in positions and only the final
   * write turns a position back into a frame - which is what makes the
   * missing-frame case fall out rather than needing its own arm. */
  uint8_t have[PURE_WIGGLE_FRAMES_MAX];
  int n = 0;
  for (int i = 0; i < PURE_WIGGLE_FRAMES_MAX; i++) {
    if (present & (1u << i)) have[n++] = (uint8_t)i;
  }
  if (n == 0 || seq == NULL || cap <= 0) return 0;

  const int len = (loop == PURE_WIGGLE_BOUNCE && n > 2) ? 2 * n - 2 : n;
  /* Refuse rather than truncate. A short order is not a shorter wiggle, it is
   * a swing that stops somewhere arbitrary and jumps back, and the caller's
   * still is a better picture than that. */
  if (len > cap) return 0;

  int k = 0;
  for (int p = 0; p < n; p++) seq[k++] = have[rtl ? n - 1 - p : p];
  if (loop == PURE_WIGGLE_BOUNCE) {
    /* The way back, ends excluded. Empty at one and two frames, which is why
     * the length above collapses to n there: the interior of a two-frame
     * bounce is empty and out-and-back is just the two frames, which still
     * loops correctly. */
    for (int p = n - 2; p > 0; p--) seq[k++] = have[rtl ? n - 1 - p : p];
  }
  return k;
}

int pure_wiggle_period_ms(int fps) {
  if (fps <= 0) fps = PURE_WIGGLE_FPS_DEFAULT;
  if (fps < PURE_WIGGLE_FPS_MIN) fps = PURE_WIGGLE_FPS_MIN;
  if (fps > PURE_WIGGLE_FPS_MAX) fps = PURE_WIGGLE_FPS_MAX;
  return 1000 / fps;
}

/* ------------------------------------------------------------------ */
/* Wigglegram alignment geometry                                       */
/* ------------------------------------------------------------------ */

/* sin and sqrt without math.h, because this file links on the host without
 * libm (see pure_format_iso8601's note - same rule). Accuracy only has to be
 * good enough for a crop inset that is then ceil()'d to a whole pixel, and the
 * rotation term is zero on every capture this firmware writes. Kept local so
 * the crop the panel computes and the crop the worker computes agree to the
 * pixel for the offsets a real calibration produces (a degree or two); the
 * worker's Math.sin and this Taylor series diverge only past the tens of
 * degrees no lens mount reaches. */
static double align_sqrt(double v) {
  if (v <= 0.0) return 0.0;
  double g = v > 1.0 ? v : 1.0; /* a seed at or above the root, so Newton descends */
  for (int i = 0; i < 40; i++) g = 0.5 * (g + v / g);
  return g;
}

static double align_sin(double rad) {
  /* Range-reduce into -PI..PI so the series stays accurate; the input is a
   * small positive angle in practice, but the absurd-offset guard test feeds
   * 45 degrees and the reduction costs nothing. */
  const double TWO_PI = 6.283185307179586;
  const double PI = 3.141592653589793;
  while (rad > PI) rad -= TWO_PI;
  while (rad < -PI) rad += TWO_PI;
  const double x2 = rad * rad;
  /* Taylor to x^9: within 1e-6 across the whole reduced range. */
  return rad * (1.0 - x2 / 6.0 * (1.0 - x2 / 20.0 * (1.0 - x2 / 42.0 * (1.0 - x2 / 72.0))));
}

static double align_abs(double v) { return v < 0.0 ? -v : v; }

static int align_ceil_i(double v) {
  int i = (int)v;
  return ((double)i < v) ? i + 1 : i;
}

static int align_floor_i(double v) {
  int i = (int)v;
  return ((double)i > v) ? i - 1 : i;
}

bool pure_align_has_offset(const pure_cam_offset_t *offsets, int n) {
  if (offsets == NULL) return false;
  for (int i = 0; i < n; i++) {
    if (offsets[i].x != 0.0 || offsets[i].y != 0.0 || offsets[i].rot != 0.0) return true;
  }
  return false;
}

pure_crop_t pure_align_overlap_crop(int w, int h, const pure_cam_offset_t *offsets, int n,
                                    double scale) {
  double max_x = 0.0, max_y = 0.0, max_rot = 0.0;
  for (int i = 0; offsets != NULL && i < n; i++) {
    const double ax = align_abs(offsets[i].x) * scale;
    const double ay = align_abs(offsets[i].y) * scale;
    const double ar = align_abs(offsets[i].rot);
    if (ax > max_x) max_x = ax;
    if (ay > max_y) max_y = ay;
    if (ar > max_rot) max_rot = ar;
  }
  /* Rotation sweeps corners by ~sin(rot) x half-diagonal. */
  const double half_diag = align_sqrt((double)w * w + (double)h * h) / 2.0;
  const double slack = align_sin(max_rot * 3.141592653589793 / 180.0) * half_diag;
  const int inset_x = align_ceil_i(max_x + slack) + 2;
  const int inset_y = align_ceil_i(max_y + slack) + 2;
  int cw = w - 2 * inset_x;
  int ch = h - 2 * inset_y;
  if (cw < 16) cw = 16;
  if (ch < 16) ch = 16;
  cw &= ~1;
  ch &= ~1;
  pure_crop_t crop = {align_floor_i((double)(w - cw) / 2.0), align_floor_i((double)(h - ch) / 2.0),
                      cw, ch};
  return crop;
}

pure_crop_t pure_align_plan(int src_w, int src_h, const pure_cam_offset_t *offsets, int n,
                            pure_frame_xform_t *out) {
  const double scale = (double)src_w / (double)PURE_ALIGN_SENSOR_BASE_W;
  if (out != NULL) {
    for (int i = 0; i < n; i++) {
      out[i].dx = (offsets != NULL) ? offsets[i].x * scale : 0.0;
      out[i].dy = (offsets != NULL) ? offsets[i].y * scale : 0.0;
      out[i].rot_deg = (offsets != NULL) ? offsets[i].rot : 0.0;
    }
  }
  return pure_align_overlap_crop(src_w, src_h, offsets, n, scale);
}

/* ------------------------------------------------------------------ */
/* JSON nesting depth                                                  */
/* ------------------------------------------------------------------ */

bool pure_json_depth_ok_n(const char *text, size_t len, int max_depth) {
  if (text == NULL || max_depth < 0) return false;
  int depth = 0;
  bool in_string = false;
  for (size_t i = 0; i < len && text[i] != '\0'; i++) {
    const char c = text[i];
    if (in_string) {
      if (c == '\\') {
        i++; /* the escaped character, whatever it is, is not a quote */
      } else if (c == '"') {
        in_string = false;
      }
      continue;
    }
    if (c == '"') {
      in_string = true;
    } else if (c == '{' || c == '[') {
      if (++depth > max_depth) return false;
    } else if (c == '}' || c == ']') {
      if (depth > 0) depth--;
    }
  }
  return true;
}

bool pure_json_depth_ok(const char *text, int max_depth) {
  if (text == NULL) return false;
  return pure_json_depth_ok_n(text, strlen(text), max_depth);
}

/* ------------------------------------------------------------------ */
/* Sync-edge attribution (#165)                                        */
/* ------------------------------------------------------------------ */

int pure_sync_classify(uint32_t last_seq, uint32_t seq, uint32_t expected, bool has_edge,
                       int64_t sync_to_cmd_us) {
  if (!has_edge || seq == 0) return PURE_SYNC_NONE;
  /* The edge must be before the command, and not by more than the window. */
  const bool in_window = sync_to_cmd_us >= 0 && sync_to_cmd_us <= PURE_SYNC_EDGE_WINDOW_US;
  if (!in_window) return PURE_SYNC_STALE_GENERATION;
  if (last_seq == 0 || expected == 0) return PURE_SYNC_UNVERIFIED; /* no baseline to hold it to */
  if (seq == last_seq + expected) return PURE_SYNC_OK;
  /* Counter went backwards (node rebooted, count re-based below ours) or moved
   * by the wrong amount - an edge this node counted that no pulse of ours
   * produced, or one it missed. Either way not provably this shutter's edge. */
  return PURE_SYNC_STALE_GENERATION;
}

const char *pure_sync_class_name(int cls) {
  switch (cls) {
    case PURE_SYNC_OK: return "ok";
    case PURE_SYNC_UNVERIFIED: return "unverified";
    case PURE_SYNC_STALE_GENERATION: return "stale-generation";
    default: return "none";
  }
}

/* ------------------------------------------------------------------ */
/* Lens cover                                                          */
/* ------------------------------------------------------------------ */

int pure_lid_update(pure_lid_t *st, const int *means, int n, uint32_t dt_ms) {
  if (st == NULL) return PURE_LID_UNKNOWN;
  if (means == NULL || n <= 0) {
    st->candidate = PURE_LID_UNKNOWN;
    st->held_ms = 0;
    st->answered = 0;
    st->agreed = 0;
    return st->state;
  }

  int answered = 0, dark = 0, lit = 0;
  for (int i = 0; i < n; i++) {
    if (means[i] < 0) continue; /* that camera did not answer */
    answered++;
    if (means[i] <= PURE_LID_DARK) {
      dark++;
    } else if (means[i] >= PURE_LID_LIT) {
      lit++;
    }
    /* Between the two thresholds a camera has no opinion, and because the
     * rules below want unanimity it withholds the whole decision. That is the
     * hysteresis: the state cannot chatter across one threshold. */
  }

  int candidate = PURE_LID_UNKNOWN;
  int agreed = 0;
  if (answered >= PURE_LID_MIN_CAMS) {
    if (dark == answered) {
      candidate = PURE_LID_CLOSED;
      agreed = dark;
    } else if (lit == answered) {
      candidate = PURE_LID_OPEN;
      agreed = lit;
    }
  }
  st->answered = answered;
  st->agreed = agreed;

  if (candidate == PURE_LID_UNKNOWN) {
    /* No opinion this round. Drop any part-built case rather than letting it
     * bridge a gap: evidence for "the cover just closed" has to be continuous
     * or it is not evidence of an event. */
    st->candidate = PURE_LID_UNKNOWN;
    st->held_ms = 0;
    return st->state;
  }

  if (candidate == st->state) {
    /* Already there. Nothing to prove, and held_ms cannot run away. */
    st->candidate = candidate;
    st->held_ms = 0;
    return st->state;
  }

  if (candidate != st->candidate) {
    st->candidate = candidate;
    st->held_ms = 0; /* first sample of a new case carries no elapsed time */
  } else {
    st->held_ms += dt_ms;
  }

  const uint32_t need = (candidate == PURE_LID_CLOSED) ? PURE_LID_CLOSE_MS : PURE_LID_OPEN_MS;
  if (st->held_ms >= need) {
    st->state = candidate;
    st->held_ms = 0;
  }
  return st->state;
}

const char *pure_lid_state_name(int state) {
  switch (state) {
    case PURE_LID_OPEN: return "open";
    case PURE_LID_CLOSED: return "closed";
    default: return "unknown";
  }
}
