b5463/kino-d4/firmware/p4/main/capture.c

#include "capture.h"
#include "cam_sched.h"

#include <stdarg.h>
#include <stdio.h>
#include <stdlib.h>
#include <string.h>

#include "board_d4v1.h"
#include "cJSON.h"
#include "clock.h"
/* storage.h already carries the card-access lock this path takes, so the
 * capture path no longer needs to know that uploads exist at all — the
 * coordination is with the *card*, not with a particular consumer of it.
 * Enqueue still arrives through capture_on_done(), the way the gallery does. */
#include "config_store.h"
#include "driver/gpio.h"
#include "esp_heap_caps.h"
#include "esp_log.h"
#include "esp_random.h"
#include "esp_rom_sys.h"
#include "esp_timer.h"
#include "freertos/FreeRTOS.h"
#include "freertos/event_groups.h"
#include "freertos/queue.h"
#include "freertos/semphr.h"
#include "freertos/task.h"
#include "hardware_validation.h"
#include "kdp/crc32.h"
#include "kdp_recipes.h"
#include "isr_watch.h"
#include "klog.h"
#include "meta.h"
#include "net_link.h"
#include "node_link/node_link.h"
#include "power.h"
#include "pure.h"
#include "roll_state.h"
#include "storage.h"
#include "taskmon.h"
#include "thumb.h"
#include "upload_queue.h"
#include "viewfinder.h"

static const char *TAG = "capture";

/* The trigger edge. 200 us is far longer than any receiver needs and short
 * enough to be invisible in the capture budget; it exists to be seen on a
 * scope during bring-up, not to meet a timing spec nothing implements yet. */
#define TRIGGER_PULSE_US CAPTURE_TRIGGER_PULSE_US

/* A node has to expose, encode a UXGA JPEG and answer. The bench run measured
 * 380-520 ms for that; four seconds is generous enough that a timeout means
 * something is wrong rather than merely slow. */
#define NODE_CAPTURE_TIMEOUT_MS 4000

/*
 * One chunk is 8192 B, about 89 ms of line time at 921600 baud, so this is
 * 2.8 times the cost of the thing it waits for.
 *
 * ("Eleven times" was written when this was 1000 ms and never re-derived as
 * the value came down through 400 to 250.)
 *
 * It was 4000 ms, sized on a bench run where a chunk read arrived 8075 bytes
 * of 8192 at 1528 ms and roughly every chunk needed a retry. That run has been
 * superseded: the compositor was blacking out the link ISR, and once that was
 * fixed the losses went away with it. A chunk now either arrives or is gone,
 * so a long budget only makes a doomed frame take longer to admit it - and the
 * budget is spent four times over, once per camera, on every failing capture.
 *
 * 400 ms, not 1000, since the four-camera transport bench (2026-09-02). With
 * all four channels streaming at once the RX FIFO loses the tail of a chunk
 * near the 8192-byte boundary - the historical offset-8192 loss, back under
 * concurrency: 107 of 112 READ timeouts held ~8.0-8.1 KB of the 8192 with
 * disc 0B, i.e. the node sent the chunk and the last ~120 bytes were dropped.
 * Those bytes are already gone, so the read only ever waits out the whole
 * timeout and the retry (same offset, uart flushed, node still holds the
 * frame) gets them. A chunk that does arrive does so in ~120 ms even under
 * four-way load, so 400 ms is >3x the healthy time and a lost tail now costs
 * 400 ms to retry instead of 1000 - the difference between cam2's 458 KB
 * frame finishing inside the budget and being abandoned at 98%.
 *
 * 250 since #158: a lost tail is never coming, so this timeout IS the price
 * of every retry, and the healthy chunk under four-way load measures ~120 ms
 * (latencyMaxMs 122 in CAMERA_LINK_STATS). Twice that is still a real
 * margin for a slow node; three times was paying for nothing. */
#define CHUNK_READ_TIMEOUT_MS 250

/* Attempts after the first. Two: measured captures now need zero, so this is
 * for a genuine glitch, and three attempts at CHUNK_READ_TIMEOUT_MS bounds a
 * bad chunk at 750 ms - the _Static_assert below is what holds that against
 * the frame budget. (This said "three attempts at 1000 ms bounds a bad chunk
 * at 3 s"; the timeout is 250, so the real bound is 750 ms.) */
#define CHUNK_RETRIES 2

/*
 * Total budget for one frame's transfer, and it exists for the screen.
 *
 * capture_fire holds the viewfinder for its whole duration - correctly, since
 * the node has one frame and the finder would invalidate the one being read.
 * But per-chunk retries have no collective bound: 30 chunks that each take a
 * 1000 ms timeout and two retries is 90 s, and every second of it is a
 * frozen preview and a frozen shutter. A capture that has spent this long is
 * not going to succeed; failing lets the finder and the UI have the machine
 * back, which matters more than the last attempt.
 *
 * 8 s is what a frame costs plus room to be unlucky. A 241 KB frame - the
 * largest this firmware asks for, QXGA at quality 95 - is 30 chunks, about
 * 2.7 s of line time at 921600 baud, so this is roughly 3x a full-size
 * transfer and about 15x a 50 KB one.
 *
 * It was 25 s, chosen from a run where captures took 18-35 s because roughly a
 * fifth of chunk requests lost bytes to a UART overrun; 15 s was tried then and
 * cut off captures that would have completed. That run was superseded by the
 * fix for the compositor blacking out the link ISR, which is what was causing
 * the losses. The comment there said this budget should come down once the
 * bytes stopped being lost, and it has.
 *
 * 12 s, not 8, since the four-camera transport bench (2026-09-02). 8 s was
 * sized for a single 241 KB frame; four cameras streaming at once share the
 * P4's CPU and memory bus, so one frame's own transfer runs ~4x slower in
 * wall-clock, and cam2's real scene made 458 KB frames whose healthy transfer
 * alone was ~7 s. With the tail-loss retries above that tipped three of
 * twenty sets past 8 s and cost cam2 its frame at 96-99%. 12 s is the largest
 * frame's ~7 s under four-way load plus room for a realistic run of the
 * now-cheap (400 ms) retries. A genuinely dead chunk still fails fast on
 * CHUNK_RETRIES, not on this backstop, so a doomed frame is not what waits
 * out the extra seconds. */
#define XFER_BUDGET_MS 12000

/* One bad chunk must never dominate a frame's budget: its whole worst case
 * (first try plus every retry, each bounded by the read timeout) has to stay a
 * small fraction of the per-frame budget, or a handful of bad chunks on the
 * largest frame blows it - which is exactly what the four-camera bench found
 * when the pairing was 1000 ms x 3 against 8000 ms. */
_Static_assert((CHUNK_RETRIES + 1) * CHUNK_READ_TIMEOUT_MS <= XFER_BUDGET_MS / 4,
               "a single chunk's retries must stay well inside the frame budget");

/*
 * Longest the flash is allowed to stay on.
 *
 * It is released as soon as every node reports its capture finished; this only
 * bounds the case where one never answers. At 350-500 mA the difference
 * matters to the battery.
 *
 * What the old comment did not say: this is NOT a safety bound, it is a
 * deadline. A node whose exposure and encode together exceed 900 ms has the
 * flash switched off BEFORE it exposes, and gets an underexposed frame with no
 * error anywhere - the capture succeeds and the picture is dark. Measured node
 * capture is 380-520 ms, so 900 has margin today, but NODE_CAPTURE_TIMEOUT_MS
 * allows 4000: any node that is merely slow lands in that window.
 *
 * Latent while BOARD_FLASH_EN is BOARD_GPIO_NONE - GPIO28/JP1-21 went to
 * BOARD_BTN_SHUTTER in ECN-0003, so nothing is driven. The assert below is
 * what makes it safe for the day a pin is assigned: the timeout has to cover
 * the capture the flash is lighting, or the two numbers are lying to each
 * other.
 */
#define FLASH_MAX_MS 4200

/* The flash must outlast the capture it is lighting, with margin for the
 * command's own round trip. If a future board wants a shorter flash than the
 * node's worst capture, the node timeout is what has to come down first -
 * and that needs a node-side p99, not an edit here. */
_Static_assert(FLASH_MAX_MS >= NODE_CAPTURE_TIMEOUT_MS,
               "the flash must not switch off before a slow node has exposed");

/* After switching the camera bank on, the nodes have to boot before they can
 * answer. Measured at 410 ms on the bench unit; 900 leaves margin without
 * making a first shot after an idle period feel broken. */
#define CAM_BANK_SETTLE_MS 900

#define ALL_CAMS_MASK ((1u << CAPTURE_CAMS) - 1u)

/* The largest frame a node is believed about. QXGA at quality 95 measured
 * 241 KB and a busy real scene 458 KB; 1 MiB is twice that, and a node that
 * claims more is describing a buffer it does not have (the S3 carries 8 MB of
 * PSRAM, most of it the sensor's own frame buffers). */
#define CAPTURE_MAX_JPEG (1024u * 1024u)

/* ---------------------------------------------------------------- */
/* module state                                                     */
/* ---------------------------------------------------------------- */
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
